fukawachan/PoseDollLab_Design/Hardware/PoseDoll44/docs/SHOULDER_REVH.zh-CN.md

# Rev H · 肩带与双臂机械集成

> 2026-09-20 分类修订：本版 8 个相交姿态均属于左右独立手臂的避让限制，查看页已改为橙色。42 个原样本未发现已建局部机构的结构冲突。下文历史设计进度及“不具备制造条件”的边界保持；新增肩部持姿机构请查看 Rev I。

本轮按“稳定节段包壳、活动区裸露”继续设计。Manny / Quinn 各有独立的肩带与双臂 CAD 总装，沿用 Rev G 的 1:2 候选比例，约 90.8 cm；没有改变关节中心或 44 轴定义。

先打开 [肩带与双臂机械查看页](../generated/revH/RevH_Shoulder_Review.html)。这里显示实际 CAD 的三角化结果，可以选择姿态、隐藏臂壳、显示占位件、旋转及点选零件。相交实体标红，失败样本保留。

## 这一轮增加了什么

每侧加入肩带前伸／后收、抬高／下压两轴，以及肩部屈伸、外展／内收、上臂扭转三轴，连接已有肘臂架。两侧合计 12 轴参与局部总装检查。头、躯干、手腕、前臂独立旋转、手、腿脚以及整机支架没有因此完成。

肩带根部两个竖轴的距离只有约 14.3 mm（Manny）、9.3 mm（Quinn）。新结构采用：

- 共用上轴承桥，保持两条原有竖直轴线。
- 两侧抬肩轴的轴承分别沿原轴线向前、向后移开，避免根部组件挤在一起；轴线本身没有平移。
- 前后转动的持姿摩擦盘上下分层，内侧切平，让相邻长轴通过。
- 肩部三轴共心，屈伸框架采用侧面开口的 U 形结构，让上臂侧举时能穿过开口。
- 上臂、前臂保留分体硬壳；肩带、肩关节和肘部裸露。

左右臂壳沿用各角色 Rev G 的左侧轮廓并镜像到右侧，是身体截面近似，不是左右 UE 皮肤表面的精确复制。肩、肘轴线仍分别取各侧原始配置。

## 已完成与尚未完成必须区分

本轮完成的是轴线、轴承位置、刚性承力框架与部分轴系的空间集成，不是已经能保持姿势、读出所有角度的完整肩部产品。

| 项目 | 当前状态 |
|---|---|
| 肩带 4 轴 | 有轴、轴套、框架及摩擦面候选；预紧受力闭环、轴端固定和调节方式未完成 |
| 肩部屈伸／外展 4 轴 | 共心支承与运动框架已集成；持姿组件尚未装入 |
| 上臂扭转 2 轴 | 轴套、轴及摩擦面候选已布置；固定、预紧与传感器未完成 |
| 肘部 2 轴 | 继承 Rev G 的局部结构；齿轮测角和预紧细节仍是候选 |
| 肩带测角 | 有 4 路磁铁、芯片和板形占位；板上器件、接插件、支架、走线和磁场验证待完成 |
| 肩部测角 | 6 路封装尚未布置，不能据空间检查认定已能读数 |
| 壳体和打印 | 已有臂壳；扣合、安装与接触边缘还需细化，没有制造放行 |

两块肩带前后转动的电路板外形向各自外侧偏置 4 mm，芯片仍对准转轴。这需要新的板上布局核对，不能直接当作旧 Rev B 电路板已经兼容。肩带磁铁与芯片之间的名义间隙只是几何候选。

## 如何看待姿态检查

原始对称抱臂会让两条前臂互相穿入；单纯同时给肩带和肩关节相同角度，也可能使手臂向中间相撞。这些样本仍保留为失败记录，没有通过缩小关节范围来隐藏它们。

新增的错开抱臂候选，让一条手臂位于另一条之前／之上，在两款当前局部 CAD 中都没有检测到超阈值穿插。它还没有包括头、手或完整躯干表面，因此只是可继续研究的姿势，不能视为完整人偶已经满足抱臂验收。

肩膀下压时让肩关节适当补偿，可使手臂保持竖直；肩带前伸加耸肩时，肩关节也可调节到双臂平行前伸。这些是新的明确姿态，不会替换原始失败数据，也不会自动修改用户的实际传感器输入。

[检查报告](../verification/REVH_REPORT.zh-CN.md)给出全部统计、失败样本、轴线核对、分件尺寸和单位末端载荷计算。

## 接下来需要解决的工程关口

1. 补齐肩部屈伸／外展持姿组件，并闭合各关节的金属预紧受力路径；不能靠加紧打印框架来冒充设计完成。
2. 完成轴端限位、正向传力、可拆固定及轴套的轴向保持，核对夹紧后是否仍有正确的转动间隙。
3. 完成 6 路肩部测角和 4 路肩带板的真实电子封装，检查组合运动中的引线长度与弯曲空间。
4. 加入躯干、颈头、手腕与手后重做组合姿态、质量、持姿力矩、操作力和全身碰撞检查。
5. 裸露区保留清楚的抓握和检修通道；壳体不再跨关节封闭。

目前不需要打印、测量或采购。STEP 文件是候选 CAD，金属件并未全部对应到已选定的采购件。UE 插件与 Python 模拟器保持原状；此前颈部位置误差和 Quinn 的独立 UE 适配仍待解决。
