fukawachan/PoseDollLab_Design/Hardware/PoseDoll44/docs/SHOULDER_REVI.zh-CN.md

# Rev I · 肩部持姿机构

本版继续 Manny / Quinn 各自的 1:2、约 90.8 cm 候选尺寸。新增左右肩部屈伸、外展的四套持姿机构，保持关节中心、轴线和臂长。外壳仍只覆盖稳定肢段，肩带与关节活动区裸露。

[打开交互查看页](../generated/revI/RevI_Shoulder_Review.html)，可以按“只看肩部”放大四套机构。页面呈现实际 CAD；橙色表示左右手臂需在摆姿时避让，红色才表示当前登记的局部结构冲突。详见 [检查和预算报告](../verification/REVI_REPORT.zh-CN.md)。

## 这次增加的机械连接

每侧屈伸轴的摩擦组件放在肩部内侧，外展轴组件放在前侧。通过沿既有轴线安排零件位置，保留人物关节中心。外展前轴的光滑轴径由 4 mm 改为 6 mm，后侧 4 mm 支点保留；屈伸光滑轴径继续为 6 mm。

每套组件包含 16 个独立 CAD 零件：

| 功能 | 零件 |
|---|---|
| 承载和传力 | 一体带盘金属轴、D 形连接、轴向固定垫片和内侧 M3 螺钉 |
| 摩擦保持 | 可更换带定位耳摩擦片、金属反力板 |
| 预紧 | 两片反向串联碟簧、钢垫片、带 D 槽止挡盖、外侧 M3 螺钉 |
| 支承与磨损界面 | 径向轴套、止推复合垫片 |
| 固定至打印框架 | 两颗 M3 螺钉、两颗嵌入式六角螺母 |

预紧受力路径为：金属止挡盖 → 碟簧 → 钢垫片 → 止推垫片 → 金属反力板 → 摩擦片 → 一体轴盘 → 轴和轴端螺钉。打印支座传递关节作用力，但不夹在这一轴向预紧回路中。M3 螺钉用于轴端和支座固定；真正转动支承的表面是光滑轴段。

打印输出端已有 D 形孔、轴端紧固件及实际让位孔。孔和轴的候选间隙不是最终加工公差，回差和抗松方案仍要验证。新摩擦片材料还未冻结，不可用假定的摩擦系数直接订料。

## 对原结构的改动

肩带连接路径绕开内侧摩擦盘，再从盘内侧连接肩部轴承。横梁提高至肩轴上方 30 mm，避开大幅抱臂时的同侧上臂壳。这改变的是支架走向，轴的运动中心没有移动。

外展盘的安装耳、螺母槽和加强连接与打印框架一体生成。外展内环开设 3.3 mm 直通工具孔和后支轴孔，供装配阶段从后方接近内侧 M3 螺钉。屈伸轴先在内环未装时固定。工具通道的名义 CAD 包络已检查，实物工具、公差、后支轴固定方式及维修手感仍待验证。

## 以后组装的先后关系

以下用于检查设计的可装配性，尚不是给用户执行的装配说明：

1. 先安装肩带轴承与屈伸外环，此时不装内部外展环。插入屈伸带盘轴，从关节中心装内侧垫片及螺钉。
2. 放入外展内环与前侧带盘轴；暂不装后侧 4 mm 支轴，也不装中心的扭转轴套和轴。从后侧穿过 3.3 mm 工具通道，装外展内侧螺钉。随后装回后支轴、扭转轴套与扭转轴。
3. 将摩擦片定位耳放入金属反力板，再用两颗 M3 和可从内侧接近的螺母固定反力板。
4. 按指定顺序放入止推垫片、钢垫片、两片反向碟簧和止挡盖，装外侧轴端螺钉。
5. 在单关节测试中确认预紧、轴向游隙和正反向回差，再制定正式垫片调整与防松要求。

预紧不是要求用户凭手感随便把螺丝拧紧；当前候选用金属止挡尺寸限定碟簧高度。零件误差与磨损补偿需要后续明确垫片档位及测量办法，日常摆姿时不应反复松紧螺丝。

## 制造与后续工作

新增的带盘轴、反力板、止挡盖等是定制金属加工候选，已输出独立 STEP，不能当作 PLA 零件打印。螺钉、螺母、碟簧与止推件是采购候选；加工图、公差、表面处理及采购清单仍待冻结。我会继续完成这些设计，不要求用户自己选型。

本版尚不能作为可制造全身。接下来需要细化新 D 形接口的夹紧与回差、摩擦材料与预紧调整，补齐六路肩部测角和线束，并逐步接上其余身体模块。四路肩带、上臂扭转及旧肘关节仍有历史未完成项。整机质量和全身干涉也要随新零件加入重新核算。

现在不用打印或购买零件。A1 mini、0.4 mm 喷嘴、PLA 继续作为刚性打印件的试制基线。

## 工程入口

- [CadQuery 总装源文件](../cad/revI/shoulder_integration.py) · [独立摩擦组件](../cad/revI/shoulder_clutch.py)
- [CQ-editor 入口](../cad/revI/open_in_cq_editor.py) · [重建脚本](../tools/Build-RevI.ps1)
- [Manny STEP 总装](../generated/revI/manny/Manny_shoulder_assembly.step) · [Quinn STEP 总装](../generated/revI/quinn/Quinn_shoulder_assembly.step)
- [Rev H 历史查看页](../generated/revH/RevH_Shoulder_Review.html)：原始相交数据保留，已同步采用新的避让分类。

UE 插件、Python 模拟器和原始下载方案未因本轮硬件设计修改。
