fukawachan/PoseDollLab_Design/Hardware/PoseDoll44/docs/SHOULDER_REVJ.zh-CN.md

# Rev J · 肩部夹紧与外展测角

本轮把四处 D 形传力接口细化为可拆卸金属夹头，并把左右肩外展的两路测角装进当前总装。Manny / Quinn 各自的关节中心、1:2 候选比例、44 轴顺序和运动范围均保持。

这是可审查的 CAD 安装方案，尚未制造放行。现在不用打印、测量或采购。

## 新增结构

每款增加四套相同的 D6 夹头，用于左右肩屈伸和外展。夹头为定制金属件，暂按铝建模；它不是 PLA 打印件，也不要求使用者自己加工。

- 6 mm D 轴进入 6.06 mm、平面距中心 2.53 mm 的开口金属孔。
- 横向 M2×10 螺钉收紧开缝；独立 M3 轴端固定件保留。
- 两个 M2×4 法兰螺钉把夹头接到打印关节框架，螺母嵌在可接近的六角槽内。
- 两个法兰孔在模块横截面中位于 (−5.9, −5.9) 和 (+5.9, −5.9) mm，避开原来的扭转摩擦面。
- 打印支撑使用半环连接肋，绕开夹头和收紧耳；外展内框增加两条 2.2 mm 工具通道。

D 形负责几何传力，夹紧负责消除轴孔松动，轴端件负责保持装配位置。夹紧后的真实回差尚未得到验证。法兰孔间隙、摩擦预紧、打印件蠕变和上臂扭转轴本身的间隙也会影响整机，不能仅凭缩小一个孔宣称精度提高到某个数值。

## 两路测角安装

沿肩外展轴的后端布置磁铁，电路板固定在外侧框架，磁铁跟随内侧外展框架转动。两款共用传感器组件尺寸，各自支架仍接在原关节中心。

| 项目 | 当前候选 |
|---|---|
| 电子板 | 现有 sensor_revB 的真实 STEP，18 × 20 mm |
| 板模型 | 包含板体、AS5048A、四个被动器件、背面插座，共 7 个实体 |
| 后端轴 | 定制非磁性 4 mm 铝轴，两段 D 形；径向 M2 固定到内框 |
| 磁铁 | 6 × 2.5 mm，径向充磁圆磁铁 |
| 名义间隙 | 磁铁表面至芯片封装表面 2.8 mm |
| 磁铁固定 | D 形杯、轴向固定螺钉、粘接防转床、可拆保护桥 |
| 电路板安装 | 6 mm 尼龙内螺纹支柱、绝缘垫片、尼龙 M2 螺钉 |
| 接线 | 背面插座为真实模型；配对插头和弯线空间仍是待核实占位 |

独立测角 STEP 是零件组；PCB 支撑桥与肩部外框是一体结构，包含在两款人物总装的 flex_ring 中，没有重复导出到独立零件组。

磁铁周围优先使用非磁性轴和紧固件。圆形磁铁必须和杯体可靠粘接以防相对转动；保护桥负责轴向防脱，不替代防转粘接。胶种、装配方式和旋转防滑试验尚未确定。磁杯 D 形连接的装配间隙也尚未做回差验收。

磁铁与芯片中心应同轴，气隙和偏心会影响测量，附近铁磁材料可能干扰磁场。这些原则来自 [ams 磁铁选型指南，第 3、9–13、20–21 页](https://ams-osram.com/documents/20143/80162/AnglePositionOnAxis_AN000271_2-00.pdf/bd13692b-b589-af7f-560c-4d62bf25d9dd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)。2.8 mm 是本设计的几何候选，并非厂家保证此总装精度的数值。

实际 STEP 板厚为 1.51 mm，制板接口名义为 1.6 mm；当前模型按真实 STEP 定位。生产前需要按板厚和器件高度重新完成公差链，不应把这 0.09 mm 差异当作已经实测的尺寸。

数字检查会计算相对转角、同轴偏差和封装表面气隙。左右安装方向不同，几何角度符号分别为 −1 / +1；这不是 AS5048A 原始读数的最终方向标定。传感器读数方向、零位和磁场诊断仍需后续验证。

## 装配顺序

以下是 CAD 工具通道所采用的顺序，还不是新手最终装配手册。检查使用 2 mm 的 M2 工具杆和 3 mm 的 M3 工具杆包络，没有验证手掌空间、拧紧力矩或完整插入轨迹。

1. 将夹头法兰固定在各自打印框架内。放入六角螺母，再装两颗 M2×4；内框的两条工具孔用于外展夹头。此时内部轴套、扭转轴和后端测角件尚未装入。
2. 将屈伸轴装入外侧框架，按顺序收紧其 D 夹头并装内端垫片与 M3。此时外展内框、扭转轴和手臂尚未装入。
3. 加入外展内框和前端外展轴，收紧外展 D 夹头，从后方中心通道装前端轴的内侧 M3。后端测角轴与扭转轴此时必须留空。
4. 加入后端测角轴，通过径向 M2 将 D 轴固定在内框。再装扭转轴系及手臂。
5. 套入磁杯并拧紧杯内轴向 M2；随后完成磁铁防转粘接与保护桥。电路板此时尚未装上，以便拧磁铁盖。
6. 安装绝缘支柱、垫片及真实 PCB，再安装线束。线束的插头、走向、应力释放和活动余量仍要另行完成设计。

金属轴、夹头孔和尼龙紧固件都尚未冻结采购规格。标准 M2 内六角头的名义 3.8 mm 直径、2 mm 高度可参照 [MISUMI 尺寸资料](https://uk.misumi-ec.com/files/images/products/docs/hexsocketheadcapscrews.pdf)。尼龙螺钉模型采用直径 3.5 mm、高 1.4 mm 的头部包络，这是待匹配采购件的尺寸约束，不代表已确认某个商品。

## 剩余四路肩部测角

本轮另外使用同一块真实 PCB，试排了屈伸轴向内侧延长、扭转轴向顶部延长的位置。完整碰撞结果在 [测角与试排记录](../verification/revJ_readout_check.json) 中。

这些试排没有被计入已集成轴数，也没有被画成已通过的占位。若 PCB 与同侧框架或轴端相交，仍是结构问题。下一轮应考虑独立的小板、调整轴端组件或传动取角；不能把当前两路外展的成功直接复制成六路都完成。

## 边界和下一步

- 当前肩带、肩部、双肘共 12 个轴进入局部运动总装。其余 32 轴尚未在此总装集成。
- 本轮实际安装候选仅覆盖两路肩外展测角；四路肩带仍是占位，肘部传动尚待完成。
- 新夹头、螺母支座、工具孔附近的强度与变形尚未验证。打印薄壁与长期夹紧后的压溃、金属开缝弹性、螺纹啮合、轴套固定和防松都需要继续设计或实测。
- 碟簧和摩擦片保持 Rev I 候选；材料、摩擦系数、预紧公差、耐久与手感未验证。
- 两臂互碰保留为摆姿限制；邻接肢段、关节内部及归属不明的碰撞仍是结构问题。
- 维持 A1 mini、0.4 mm 喷嘴、PLA 的刚性分件规划。包围盒能放下不等于已生成可打印包；本轮未生成制造放行的 STL 或切片。
- 头、颈、躯干表面、手、全身支架与线束尚未参加完整碰撞验收；既有颈部位置误差和 Quinn 独立 UE 适配仍待处理。

下一步优先补齐屈伸／扭转测角、轴向固定和线束，随后推进躯干与下肢。详细数字结论见 [Rev J 检查报告](../verification/REVJ_REPORT.zh-CN.md)。
