fukawachan/PoseDollLab_Design/Hardware/PoseDoll44/docs/SHOULDER_REVK.zh-CN.md

# Rev K · 紧凑扭转测角安装

状态：数字设计候选，未制造放行、未实测。现在不用采购、打印或补测工具。

## 支撑方式：按用户最新要求

人偶本体不依赖固定的桌夹、立柱或底座来限定动作。站、坐、仰卧、俯卧与侧卧列为后续全身设计场景；摆好后可由独立外部物体托住。**外部支撑物本轮不设计**。内部关节轴承座、测角板托座和胸部承力框仍属于人偶骨架，需要继续检查自身干涉。

当前局部 CAD 固定一个数学参考坐标，只用于算相对姿态，不代表要求人偶锁在实体支架上。原 44 轴中骨盆三轴的名字保留兼容性，但取消固定支架后，其实体参考方案要另行设计，不能把未知输入当作测得零值。当前 UE 的 Placement 仍可控制场景整体放置；本轮不改软件。

详见 [支撑方式约定](../mechanical_manifest/support_policy.json)。本轮肩臂检查不能代表完整站、坐、躺已经验证。

## 这轮完成的结构

Manny、Quinn 各加入左右两套上臂扭转测角组件。加上 Rev J 的左右外展，每款现在有四处肩部测角安装候选。肩屈伸两路仍未装入。保留 44 轴顺序、两款各自的关节中心与约 90.8 cm 的 1:2 候选尺度。稳定肢段用臂壳，肩部活动区继续裸露。

- 用独立的 **12 × 10 × 1.0 mm 小板**取代扭转位置原先放不下的 18 × 20 mm 板。AS5048A、供电和六线 SPI 网表与 Rev B 相同。
- 扭转金属轴与磁铁杯合成一个定制铝件，缩短顶部堆叠。磁铁为 6 × 2.5 mm 径向/直径方向充磁候选；不能用轴向充磁件代替。
- 磁铁加可拆机械保护盖，两颗黄铜 M2×3 顶丝固定；胶层只承担待验证的防转配合，轴向保持不只依赖胶。
- 轴下端增加 D4 形接口和径向 M2×6 固定螺钉，使手臂与磁铁轴建立机械传角关系。该接口尚未进行夹紧回差和耐久验证。
- 测角板由两个**后装可拆托座**和两个绝缘夹盖固定。托座必须独立，不能与肩框合并打印，否则带保护盖的磁铁轴装不进去。

[查看实际总装](../generated/revK/RevK_Shoulder_Review.html) · [检查报告](../verification/REVK_REPORT.zh-CN.md) · [紧凑扭转组件 STEP](../generated/revK/components/compact_twist_encoder_assembly.step)

## 局部基准尺寸

局部 +Z 沿扭转轴指向肩顶部；原肩关节中心为 Z=0。局部 X 在左肩对应世界 +X，在右肩对应世界 -X；小板托座沿前后方向布置，避开内侧螺钉。以下是名义设计值，不是测得精度。

| 特征 | 尺寸 / mm |
|---|---:|
| 金属轴下端 | Z=-24 |
| 下端 D4 平面距轴心 | 1.50 |
| 打印 D 孔候选 | D4.10，平面距轴心 1.55 |
| 修整后固定轴座顶面 | Z=5.50 |
| 一体轴杯底面 | Z=5.70 |
| 磁铁底面 / 顶面 | Z=6.50 / 9.00 |
| 保护盖顶面 | Z=9.60 |
| 传感器封装表面 | Z=10.50 |
| 磁铁至封装名义气隙 | 1.50 |
| 小板背面基准 | Z=12.495 |
| 固定立柱顶面 | Z=10.695 |
| 后装托座板面 | Z=11.495 |
| 板夹盖名义高度 | 0.80 |
| 板夹盖 M2×6 进入固定柱的长度 | 3.40 |

STEP 的 FR4 实体为 0.91 mm，KiCad 的制造板厚设置为 1.0 mm；铜层、模型偏置与制造板厚不能混用。托座按 1.0 mm 板厚设定。板厚公差、装配偏心和轴向窜动还会改变真实气隙。

轴杯到固定座的 0.20 mm 名义间隙、磁铁径向 0.10 mm 胶层空间、板边定位间隙都是待实物校核的候选，不应据此认为打印与装配已经合格。

## 必须遵守的装配顺序

这是一份供后续放行时细化的顺序，现在不要求动手。

1. 先完成原有屈伸与外展内部紧固件，再装外展后端测角轴。保持 Rev J 的内部螺钉先装顺序。
2. 在独立扭转轴上装磁铁、保护盖及两颗径向顶丝。此时轴尚未插入肩框，顶丝有直线工具通道。
3. 将完整的轴、磁铁、保护盖从上方插入扭转轴套。此时小板托座、板子、夹盖和轴下端径向螺钉均未安装。
4. 对齐手臂 D 形孔，插入轴下端，再装下端径向 M2×6 螺钉。
5. 放入左右两个可拆托座，再放小板、夹盖与 M2×6 螺钉。螺钉为几何候选，不能给尚未测试的打印螺纹指定装配扭矩。
6. 在外肩框装合前插入短 FPC 并关闭锁扣，再完成肩部总装。FPC 型号、转接板及全行程活动线束尚未完成设计。

工具检查使用明确的分步已装零件清单。它证明的是已建几何中的直杆、板子、轴及连接器服务包络没有超阈值阻挡；没有证明手指能伸入、实际扭矩合适、零件在公差极限下仍能装入，也没有证明无需拆解即可维护。

## 小板与连接器

原生 KiCad 工程：[sensor_revC_mini](../electronics/sensor_revC_mini/PoseDoll_AS5048A_revC_mini.kicad_pro)。

六线保持为：1 GND、2 +3V3、3 SCK、4 MOSI、5 MISO、6 CS_N。仅使用 3.3 V 供电。使用新连接器后不能直接插旧 JST 线束；排线两端编号、接触面和转接板需要单独设计。

连接器候选为 Hirose FH19C-6S-0.5SH(10)，0.5 mm 间距，适配厚度 **0.20 ± 0.03 mm** 的 FPC，六线排线宽度 3.5 mm。不能默认用常见 0.3 mm 排线。封装焊盘根据 [Hirose 原厂图 EDC3-155621-07](https://www.hirose.com/en/product/document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) 建立；已保存 [原始尺寸 PDF](../references/revK/FH19C-6S-0.5SH_drawing.pdf)。

CAD 中 U1、四个无源器件与板体来自实际 KiCad STEP；连接器使用 **5.15 × 3.15 × 1.0 mm 保守尺寸包络**，不是厂家精细 STEP。4 mm 短排线是服务占位，不能代替完整活动线束。锁扣打开的服务包络取 1.9 mm 高。

电气检查采用双层板、0.15 mm 走线／间距、0.25 mm 铜至板边、0.6/0.3 mm 过孔。连接器焊膏孔当前采用四边内缩 0.025 mm 的候选，投板前仍需对照厂家模板建议复核。没有输出量产下单包，也没有进行信号完整性或 EMC 验证。详情见 [提取接口与规则](../electronics/sensor_revC_mini/mechanical_interface.json)。

## 本轮保留的问题

肩屈伸板在 Quinn 的后收＋下压样本中仍会碰到胸部内部承力框，因此没有计入已完成安装。旧扭转直排试放也曾碰到内部螺钉；它已由本轮紧凑轴杯方案替代，失败记录保留用于追踪，不能当成当前总装结论。

四处肩带、两处肘测角仍有占位或转接未完成；肩带与扭转持姿预紧、完整轴向保持、全行程排线、供电转接、躯干、颈头、手与下肢尚未完成。完整 44 轴装配仍只有 12 轴参与当前局部总装。

真实磁场强度、偏心、附近铁磁件的影响、回差、蠕变、耐久与手感都待后续分阶段实测。本轮气隙和转角检查仅是几何关系，不代表 AS5048A 已有真实读数。
