fukawachan/PoseDollLab_Design/Hardware/PoseDoll44/docs/SHOULDER_REVL.zh-CN.md

# Rev L · 肩部屈伸测角安装

Manny、Quinn 各补入左右屈伸测角组件。加上已有的外展和扭转，**每款三轴肩关节的六处测角安装均已建立 CAD 候选**。这不包含肩带四轴，也不代表全身 44 轴完成。

[交互查看页](../generated/revL/RevL_Shoulder_Review.html) · [检查报告](../verification/REVL_REPORT.zh-CN.md) · [拆装层次图](../generated/revL/components/flex_exploded.png)

## 为什么这样改

Rev K 的小板直排试放在 Quinn 肩带后收、下压时碰到胸部内部承力框。这轮沿用 12 × 10 mm 小板，改用较矮的轴端螺钉、套在金属止挡帽外的磁铁杯，并把板子绕测量轴旋转 90°。小板背面从旧试排的 63.995 mm 移到 61.771 mm，缩短 2.224 mm。

不移动人物关节中心，不改臂长，不缩小原关节限位。仍采用约 90.8 cm 的 1:2 候选尺寸；稳定肢段包壳，肩部活动区裸露。**人偶本体不依赖固定外部支架，外部支撑物暂不设计**。站、坐、仰卧、俯卧、侧卧是后续全身场景，当前肩臂检查不代表全身场景已完成。

## 转角如何传递

机械路径为：屈伸输出框 → 原金属 D 形驱动与屈伸轴 → D 形止挡帽 → 带配合平面的磁铁杯 → 磁铁。测角板经两根独立固定柱连接屈伸反力板，与肩带输出框一起运动。

磁铁杯和止挡帽靠平面配合传角，两颗侧面顶丝负责轴向保持。磁铁暂按径向留 0.10 mm 胶层防转，并用可拆保护盖挡住外圈；粘接剂、真实回差和耐久尚待选型与实测。没有将磁铁只粘在螺钉头上，也没有让测角板承受手臂重量。

两根固定柱装在反力板上，固定孔与原离合安装螺钉分开。离合的弹簧、止挡高度与金属闭合受力路径保持；止挡帽材料改为铝，轴端螺钉改为钛合金候选，因此材料强度、局部接触压力、锁紧和持姿仍须验证。

## 主要名义尺寸

局部 +Z 从肩关节中心沿屈伸轴指向胸口，左侧对应世界 -Y，右侧对应世界 +Y。小板坐标相对该局部坐标绕 Z 转了 90°。

| 特征 | 名义尺寸 / mm |
|---|---:|
| 原离合基面 | Z=43.000 |
| 止挡帽底面 / 顶面 | Z=50.376 / 53.376 |
| M3 矮头螺钉头径 / 高度 | 5.70 / 1.65 |
| 磁铁杯底面 / 顶面 | Z=50.576 / 58.276 |
| 磁铁杯外径 | 17.40 |
| 杯底与螺钉顶面之间的轴向空隙 | 0.15 |
| 磁铁下面杯底厚度 | 0.60 |
| 磁铁底面 / 顶面 | Z=55.776 / 58.276 |
| 保护盖顶面 / 外径 | Z=58.876 / 19.00 |
| 传感器封装表面 | Z=59.776 |
| 磁铁到封装名义气隙 | 1.50 |
| 小板背面基准 | Z=61.771 |
| 两根固定柱中心 | X=0，Y=±11.90 |
| 固定柱本体高度 / 六角对边 | 12.771 / 3.50 |
| 固定柱底部 M2 进入反力板 | 2.50 |
| 板夹 M2×6 进入固定柱 | 3.20 |

反力板新增的两孔是贯通 M2 底孔，螺柱端部停在 Z=44.50，距摩擦片顶面保留 0.50 mm。不能让螺柱伸到摩擦片上。磁铁杯保护盖顶丝的底孔留了退刀深度，止挡帽侧面螺纹孔通至已有中心孔。CAD 螺纹按底孔与外螺纹包络表达，未画螺旋牙形。

打印保护盖的局部环壁约 0.75 mm，部分配合仅有 0.05 mm 径向余量；这些是**待调整的配合候选**，还不能当作 PLA 打印后可直接装好的尺寸。金属件孔位、公差与表面质量仍需后续加工图和实物校核。当前不要求打印、采购或测量。

## 分步装配顺序

以下是已建零件中的名义顺序，还不是制造放行说明书。

1. 完成原屈伸离合和内部 D 形驱动的紧固件。使用新铝止挡帽及 M3×8 矮头螺钉，先拧好轴端螺钉，再装磁铁杯。原弹簧高度由金属止挡决定。
2. 把空磁铁杯沿轴线套到止挡帽的配合平面上，装两颗 M2×4 侧面顶丝。此时固定柱、小板和板夹都未装。
3. 安放磁铁、保护盖与两颗 M2×3 顶丝。磁铁充磁必须沿直径方向；真实磁场与防转粘接还未验证。
4. 拧入两根六角固定柱。扳手从各固定柱朝关节外侧的方向接近，握住固定柱底部六角，避免穿过离合垫片。
5. 放入两个独立板托座，再沿轴向放小板、板夹和 M2×6 螺钉。固定柱及板夹均能拆下。
6. 在工作台上的局部组件中插入 FPC、操作连接器锁扣。先装好屈伸反力板与肩带输出框的 M3 安装螺钉，再与肩带上游机构合装；Quinn 若完全装合后再从该方向伸螺丝刀，会受到上游框架阻挡。

工具检查记录了每一步明确的已装零件。它涵盖直杆、扳手包络、磁铁杯几个插入位置以及各个板上器件的保守轴向插入包络；没有验证手指抓握、实际装配扭矩、全公差装配或无需拆解的维修。肩带上游的最终轴向保持仍待设计，不能将上述顺序理解为全身装配已经打通。

## 电子与校准

继续使用 [Rev C mini KiCad 工程](../electronics/sensor_revC_mini/PoseDoll_AS5048A_revC_mini.kicad_pro)，原理图、PCB 与六线 3.3 V SPI 接口没有改动。本轮不重新声称完成电子实测。

小板的板体、AS5048A 和四个无源件来自已有 KiCad STEP；FPC 连接器是厂家尺寸包络，短排线仍是占位。板旋转 90° 后，在我们的 CAD 参考轴定义中增加了 -90° 的名义零位偏置，检查脚本已显式扣除。这个数值不是 AS5048A 实际上电原始读数；实际磁铁方向、芯片零位与左右正负仍须校准。

轴端螺钉候选为 [Accu SSB-M3-8-TI5](https://accu-components.com/us/socket-button-screws/422924-SSB-M3-8-TI5)，厂家列出的头径 5.7 mm、头高 1.65 mm、2 mm 内六角用于当前包络；[来源记录](../references/revL/button_screw_source.json)保留具体字段。未确认供货与实际承载，不可随意用普通高头 M3 替换。铝帽、钛螺钉及黄铜顶丝减少磁铁附近的铁磁材料，但附近仍有钢轴、反力板和弹簧；当前几何气隙不能证明磁场质量。

## 继续设计的部分

肩带四轴测角、肘部传角转接、肩带与扭转持姿预紧、完整轴向保持、活动线束和转接、躯干、下肢、颈头及手尚未完成。取消固定外部支架后的骨盆三轴实体参考继续保留待定，不改原通道名字，不把未知测量当作零值。UE 插件和 Python 模拟器没有因本轮修改。
