fukawachan/PoseDollLab_Design/Hardware/PoseDoll44/docs/SIZE_REVIEW_BEFORE_EXTERNAL.zh-CN.md

# 外置改版前的尺寸评估

修正后的结论：下一版采用用户已同意的“局部采集 + 外置电源/USB 接口盒”。**现有文件不能直接等比例缩放，但尚无证据证明重新设计的小型版必然昂贵或不划算。** 现有 1:2 图纸暂作比较基线，不能把 91 cm 身高、6 mm 磁铁或当前关节外径当作不可突破的设计下限。是否缩小，应由重新布置后的关节尺寸、载荷、动作空间、装配步骤和实际报价决定。

本轮只完成尺寸、接口及装配约束评估；没有生成缩小版 CAD，也没有开始制造外置版电子设备。既有 Rev N1 模型、PCB、固件和查看器均未被这次评估修改。

## 当前实际基线

- Manny 的 UE 参考表面缩放高度为 907.93 mm，Quinn 为 907.70 mm，均约 91 cm。这里是角色参考高度，不是实物量测。
- Rev N1 含原背部设备和线束的估重分别约 3.20 / 3.16 kg。它们确实比普通美术人偶更大、更重；减重和降低操作阻力有价值。
- 每款已有 39 块 12 × 10 mm 小测角板、2 块 18 × 20 mm 肩外展测角板、M2/M3 紧固件、4/6 mm 工作轴颈和指定碟簧。接头为 1 mm 间距 SH6。小板尺寸已经从当前两款制造清单的实体包络核对。
- 现有方案仍需要加工方交付精密轴系和预装关节、贴片方交付 PCBA，以及预压接线束；它本来就不是完全靠打印和拧几颗普通螺丝完成的产品。

## 磁铁与关节尺寸补充核对（2026-09-23）

先前把“不允许直接缩放”进一步写成“小型化收益不足”，证据不充分，已在本文件和配套 JSON 中修正。此修正不表示已经完成更小的关节或批准某个缩小比例。

**6 mm 的来源是当前传感器方案和早期配套磁铁基线，不是市场买不到更小磁铁。** 本项目早期物料表采用 AS5048A 与 AS5000-MD6H-2（Ø6 × 2.5 mm）组合；没有做过足以证明该尺寸成本最优的报价比较。小型化也不必首先改磁铁，需先识别真正占空间的结构。

| 产品目录核对 | 可支持的结论 | 不可推断的结论 |
|---|---|---|
| [Magnet Baron 3 × 2 mm 直径方向充磁磁铁](https://themagnetbaron.com/products/100pcs-3mm-x-2mm-1-8-x-1-16-disc-magnets-diametrically-magnetized)，100 颗标价 USD 16.99 | 确有更小规格及并不高的目录单价（约 USD 0.17/颗，未含运税） | 页面库存信息混合显示，未确认可立即发货；没有磁场均匀性/传感器匹配鉴定，不能据此采购替换 |
| [K&J D24DIA](https://www.kjmagnetics.com/d24dia-neodymium-diametric-cylinder-magnet)，约 Ø3.175 × 6.35 mm，1–49 颗档 USD 0.35/颗 | 更小直径的直径方向充磁磁铁也有目录供应 | 此件更长，并非能直接减少本项目轴向高度的候选 |
| [Infineon AS5048A 产品资料](https://www.infineon.com/part/AS5048A)给出 30–70 mT 磁场范围 | 磁铁选择须与传感器磁场要求配合 | 目录吸力、磁铁直径或单点表面场强不能替代芯片感应区域的场分布与角度误差检查 |

价格仅为查阅时的页面记录，不是到手报价，也不是制造选型。更小的磁铁需要复核磁化方向、场分布、间距、偏心及角度误差；不能保证原 AS5048A 与任意小磁铁都兼容。必要时可比较另一种传感器架构，但当前没有更换器件或固件。

**关节有重新紧凑设计的空间，当前尺寸不是已证明的最小值。** 在当前 Manny 制造清单中，肘关节的磁铁 Ø6 mm，磁铁杯外径 16.4 mm、保持盖外径 19.2 mm，摩擦圆环外径约 26 mm（不含止转耳）。较大的杯还包围止挡帽和保持结构，所以把磁铁改成 Ø3 mm，并不会自动让这套关节缩小一半。腰部下摩擦环外径为 36 mm，胸部为 32 mm；这是现有摩擦和载荷方案的结果，不是磁铁强制的外径。

现有机构也已经有 4 mm 与 6 mm 工作轴颈的区别。紧凑化可以比较：减少输出连接耳和独立隔柱、缩短轴向堆叠、合并非活动支座、调整板和插头方向、按部位采用不同规格。以上均是设计研究方向，尚无新 CAD 或装配验证。

若保持同样的所需扭矩，缩小摩擦有效半径会增加所需预紧力（简化关系 T≈μ·F·r，多摩擦面另计）。但是人偶同时缩小、减重和移出设备后，所需保持力矩也会下降；应联合重算，不能拿原约 3.2 kg 设计的载荷要求当作小型版永远不变的条件。

加工成本取决于零件复杂度、装夹次数、公差、标准件/定制件比例、批量和预装工序。更小并不必然更贵；减少零件和装夹也可能抵消尺寸变小带来的难度。若必须采用更紧公差或微小紧固件，则可能增加加工和用户维修难度。目前没有报价，不能给出净成本结论。

## 为什么不能把所有文件一起缩放

| 约束 | 当前设计 | 等比例缩小造成的变化 |
|---|---|---|
| 磁铁与安装杯 | Ø6 mm 磁铁，示例杯孔 Ø6.2 mm | 缩至 90% 后孔为 Ø5.58 mm，现有磁铁装不下 |
| 小板与板托 | 12 mm 板宽，示例板托内侧宽 12.2 mm | 缩至 90% 后间距 10.98 mm，现有板装不下 |
| 插头、螺丝、碟簧 | 现成实物规格 | 改小安装位不会改小买来的实物；改型需重做配合和载荷核对 |
| 测角和转动配合 | 1.5 mm 名义芯片面间距、0.05 mm 等候选配合量 | 要按传感器磁场、加工和装配误差重新确定，不能与骨长一起缩放 |
| 走线和工具空间 | 活动传感器线候选弯曲半径 12 mm，电源 15 mm；螺丝刀/插拔通道另留 | 原线材和工具不会等比例变小，需要重新布置和检查 |

上述孔/板托例子取自现有通用关节源码；它们只证明直接缩放不兼容现有零件，**不能据此断言重新设计的小型关节做不出来**。线束弯曲半径仍是本项目候选，尚未得到实物反复弯曲寿命验证。[JST SH 官方图纸](https://www.jst-mfg.com/product/pdf/eng/eSH.pdf)给出了固定的插头尺寸和间距。

如果只缩短骨骼、保留原关节模块，关节和插头会相对更粗，肩、髋、肘、膝附近的可用空间减少，可能更早接触。具体哪些姿态受限需要对新模型重新检查；本轮没有把这种风险冒充为已经仿真出的碰撞结果。所有零件真能理想等比缩放时，纯几何碰撞关系反而不变，现实问题来自固定尺寸的器件、配合和线材。

## 缩小的收益和代价

| 相对当前线性尺寸 | Manny 参考身高 | Quinn 参考身高 |
|---|---:|---:|
| 100.0% | 90.8 cm | 90.8 cm |
| 90.0% | 81.7 cm | 81.7 cm |
| 80.0% | 72.6 cm | 72.6 cm |
| 66.7% | 60.5 cm | 60.5 cm |

这些是算术示例，不是已通过验证的尺寸选项。理想情况下所有材料、壁厚、器件都缩至 80%，质量可按 0.8³ ≈ 51.2% 变化，重力矩按 0.8⁴ ≈ 41.0% 变化，因此不能简单说“更小一定更弱或更难保持姿势”。真实人偶中的板、螺丝、线和配合不能全部照缩，不能按这两个比例预测实际减重和手感。

重新设计小型版有可能更轻、更便于搬动；代价是重做多轴关节、紧固与预紧件选型、测角板托、装配通道、全身动作和线束验证。若采用更细小零件或更紧密布置，预装、插拔、检验与后期维护要求也会上升。这些是需要检查的项目，不能只凭现有元件装不进缩小后的孔位，就判断重新设计的小型版代价大于收益。当前缺少紧凑关节对比、加工报价和小型样机，因此成本变化与可缩小百分比均未确定。设计和验证工作增加，也不等于用户最终采购、装配和维修成本一定增加。

0.2 mm 喷嘴可能改善部分打印细节，但不能解决现成芯片/接头尺寸、金属轴系配合和螺丝刀空间；此处没有必要先购买另一台打印机或喷嘴。

## 外置改版与后续尺寸比较的约束

1. 当前交付图纸仍为各自 UE 参考骨架的 1:2 基线。若研究缩小版，两款应各自统一缩放解剖长度，保留人物比例、测量轴语义和活动范围目标；新关节中心由新比例确定，不能为了塞入旧关节只缩短某几段肢体。
2. 重新紧凑布置本地采集板，取消背部大电子仓及只服务电子仓的突出载架，给背手动作让出空间；保留真正的肩颈/脊柱承重结构。
3. 把电源与 USB 网关放外部；小板、局部支路保护和柔性线仍需留在人偶内。原背部组件约 0.54 kg 不能全部当作确定减重。
4. 将真实插头、拔插和工具通道、线束服务弯纳入新布局，不以难维修的小型接头或削减动作范围换取外观紧凑。
5. 新布局完成后重新计算质量、重心与各关节保持需求，再决定哪些预紧参数能降低。重量减轻并不自动使原摩擦关节更容易掰动。
6. 继续 41 个相对测量轴 + 3 个固定骨盆协议槽；整体位置和全部整体转动由 UE 调整。固定支架和 IMU 不在此改版范围。

外置主要减少突出厚度和机内设备负担，**不会让人偶变矮**。若后续仍需更小身高，应作为保留人物比例的独立小型化设计，不能在切片器里缩放现有 STL。

证据：[两款比例复核](../verification/revM_proportions.json)、[当前 Rev N1 结果](../verification/revN_review_summary.json)、[本次尺寸计算与输入哈希](../verification/size_review_before_external.json)、[外置架构利弊](CHEST_AND_EXTERNAL_REVN.zh-CN.md)。
