fukawachan/PoseDollLab_Design/Hardware/PoseDoll44/verification/H0_REPORT.md

# H0 工程报告 · 整机布局 Rev A / 机械配合 Rev B

结论：继续数字设计，不以用户先完成试片实测为前提。Rev B 按 A1 mini / 0.4 mm / PLA 的工程假设调整通孔并生成未来试片；当前不要求用户打印或测量。整机制造与实物性能尚未验证。

## 已执行

- 44 轴映射，六区域 6/6/9/9/7/7；原虚拟轴顺序一致。
- 13 个编号打印件均为单一有效实体，单件包络不超过 160 mm；3 件 fit 试片留作设计完成后的验证。
- 单轴 0～145° 每 5° 共 30 个名义姿态：本模型参与检查的动/静实体无正体积干涉。不是连续扫角、公差或承载证明。
- KiCad ERC、DRC 与原理图一致性检查通过；详细启用/忽略规则见 JSON 报告，未添加违规豁免来隐藏失败。
- 单轴诊断固件在 ESP-IDF 6.1 编译；协议故障测试、诊断界面构造和现有模拟器测试已运行，见对应日志。
- 现有受版本管理的软件文件没有修改。本轮没有运行实体 UE Capture/Undo/重开测试。

## 布局与负载

中立头顶参考点 Z=681 mm，已超过原约500 mm目标；不是尺寸冻结。质量集中参数预算为 2.904 kg，不是称重。区域/网关 PCB、连接器维护空间和支架是候选包络。

三类关节是尺寸/能力假设：

|类别|圆柱半径×轴向长 mm|主螺栓/轴 mm|能力假设 Nm|模块质量假设 g|
|---|---|---|---|---|
|S|12×12|4|0.12|24|
|M|18×16|6|0.6|48|
|L|26×20|8|3.0|95|

H1 是较宽敞的台架夹具，不能当作已封装的 S/M/L 身体模块。当前 32 mm 传感器板和紧凑多轴支架还需共同缩小/避让。

预算采用 τ=轴方向·Σ(r×mg)；对给定形状另列 Σ(mg·垂轴距离) 的方向无关上界。后者是保守包络，**不是已经出现的实际最坏负载**；保持目标按上界×1.5+0.02 Nm 线束余量。质量集中、线束余量与能力假设都需实物修正。

|轴|12姿态重力最大 Nm|方向无关上界 Nm|设计保持目标 Nm|能力假设 Nm|
|---|---:|---:|---:|---:|
|pelvis.pitch|1.157|6.1891|9.3037|3.0|
|pelvis.roll|0.0421|5.9899|9.0049|3.0|
|waist.pitch|0.9591|3.3161|4.9941|3.0|
|waist.roll|0.0421|2.9739|4.4809|3.0|
|pelvis.yaw|0|2.2632|3.4148|3.0|
|chest.roll|0.0421|1.8939|2.8609|3.0|
|waist.yaw|0|1.8114|2.7371|3.0|
|chest.yaw|0.0|1.8114|2.7371|3.0|

结论：当前大关节能力假设无法覆盖保守预算。需要减重、收拢轴中心、重新布置支架和夹持面，而不能直接拧紧所有关节。强度/蠕变/疲劳未做结论。

## 碰撞与走线

完整布局保留 12 个具名姿态和 64 个固定种子随机姿态的球包络筛查。进一步对 12 个姿态中的关节、传感器板、区域板与接头维护包络做了 OCC 交集：

|姿态|相交包络对数|
|---|---:|
|neutral|23|
|arms_forward|23|
|arms_overhead|29|
|arms_side|23|
|hands_on_hips|24|
|arms_crossed|32|
|forehead|24|
|sitting|23|
|crouch|29|
|head_tilt|23|
|hip_abduction|23|
|palms_turn|23|

这些是实心设计包络的相交，不全等于真实空心支架撞击；它们也**不能被忽略当作已解决**。需要紧凑三轴支架详细设计和连续运动/工具/线束审查。具名姿态是设定角度，不证明手实际碰到额头或髋部。

六区域节点位置已调整。12 姿态中的端点直线距离+60 mm 假设余量上取整后，44 条最长 250 mm。它不是沿关节表面的走线长度，更不是可裁线单；弯曲、应力释放、插拔空间仍待设计。
CAN 候选线性顺序 G0→N1→N5→N6→N3→N2→N4，端点终端，电源单独分路。不是把多个分支星形连成 CAN。

## 电气预算与实现范围

44传感器、6 MCU、7 CAN收发器及缓冲余量，按3.3V负载和85%降压效率估算，5V输入 2.277 A；加30%余量 2.96 A。5V/4A仅为候选规格，未选择适配器或完成保护/热设计。
九传感器区域若用线性稳压，预算耗散 0.765 W，因此完整区域应设计降压电源，不能照抄台架DevKit的供电。
CAN：17帧/周期×100Hz×135bit + 60诊断帧/秒×135bit，500kbit/s下约47.52%；未含实测重发和错误风暴，不是通过60%占用目标的证据。
支架粗估力矩 12.27 Nm（重心150mm + 手20N作用于400mm），桌夹/桌面未选型。

只完成自制传感器板与单轴USB诊断。区域节点/网关PCB、保护/隔离供电、CAN固件、完整cohort USB协议、UE实体设备配置和校准尚未实现。无采购生产Gerber，无烧录、OTP写入或实物通电。

## Rev B 打印配合设计依据

已读取用户提供的《PLA材料比较》对话，并核对官方补偿功能文档及一条社区原始反馈。社区个例不作为精度保证。当前孔径：M2 2.6、M3 3.6、M4 4.8、M6 6.8 mm；多片支架 M3 3.8 mm。M5 5.8 mm 仅保留规则。
CAD 中的装配余量与切片补偿分开记录；未来切片初始 XY 补偿为0、自动圆孔补偿关闭，避免叠加未标定修正。轴套座和磁铁座单独处理，不套用螺丝通孔余量。
孔径误差 -0.4/-0.2/0/+0.1 mm 只是敏感性情景，不是实测分布；参见 print_fit_sensitivity.json 与 [设计依据](../docs/DESIGN_BASIS.zh-CN.md)。这些假设不能证明定位、承载或所有打印方向合格。

## 继续设计与后续实物验证

1. 采用 print_fit_profile_revB.json 中的未标定假设继续设计；不等待用户补工具或试片。
2. 设计端继续完成轴套保持、磁铁定心、五金选型、紧固件和工具净空；在最终实物测试包中明确装配件与检验方法。
3. 完成紧凑三轴详细结构，实测相邻磁铁、负载与手感后扩展一侧肢体。
4. 节点/网关与UE实体链路独立验收后进入全44台架和整机。

软件基线：7c22e075fe0efe295ce2935a8bb2a92cff0b6def。原profile SHA256：a7047b7c1bdefaee37acf547d5a823cc2f89d08f5c3e9cd9710a6f6bf79ef224。
