fukawachan/PoseDollLab_Design/Hardware/PoseDoll44/verification/REVL_REPORT.zh-CN.md

# Rev L · 肩部屈伸测角检查

状态：数字设计候选，未制造放行、未实测。两款各新增左右屈伸安装；加上已有外展、扭转，每款六处肩关节测角安装候选。肩带不包括在这六处中。

## 总装检查

| 角色 | 实体及占位 | 无局部结构冲突 | 同时没有双臂互碰 | 肩关节测角安装 |
|---|---:|---:|---:|---:|
| Manny | 335 | 36/36 | 32/36 | 6 |
| Quinn | 335 | 36/36 | 30/36 | 6 |

原有 72 个离散肩臂姿态通过局部结构检查。阈值为相交体积 0.02 mm³。10 个独立双臂相交样本继续作为橙色摆姿限制；内部及相邻节段冲突仍标红。另有两款合计 12 个“肩带极限位置＋屈伸角度”组合，仅复查涉及本轮新增／修改件的配对，未发现相交；它们不能作为全总装新增姿态通过数。

检查先核对 Rev K 及其 Rev J 继承几何、比例和结果的 SHA256，并断言未改零件保持原 Shape 对象。原有未改件配对复用此前检查结果；每个姿态中涉及本轮变化的配对都重新做 BRep 相交。同一运动节段内的变化配对另行检查，只有明确螺钉／螺纹底孔对被解释为预期配合。

每款增加 46 个实体／占位，并修改 6 个既有实体，共 335 个；板上元器件也分别计数，**不是采购 335 件**。全部逻辑实体有效、单一实体。当前仍为 12/44 轴参与局部总装，人物比例、关节中心和原角度限位不变。

## 新组件与胸部承力框的距离

| 角色 | 最近的原有样本 | 最近零件 | 距离 / mm |
|---|---|---|---:|
| Manny | back_down | l_flex_sensor_board_M2x6_0 | 9.144 |
| Quinn | down | l_flex_sensor_board_cap_0 | 1.805 |

这些是名义 CAD 距离，不包含制造公差、手部挤压、骨架变形或完整躯干表面。小板背面基准从旧直排试放的 63.995 mm 改为 61.771 mm，缩短 2.224 mm。前期小板方向试排见 [研究记录](revL_head_probe.json)，它只检查了板与连接器包络，最终总装结论以本报告为准。

## 装配、测角与电路

- 64 条原离合／外展工具通道、36 条原扭转装配通道、76 条新增屈伸工具与插入检查通过，共 176 条。记录中明确区分工作台子装配与肩带上游尚未装入的阶段。
- 六处测角在两款各 36 姿态下完成 432 条同轴、相对角度及封装表面气隙检查。外展名义气隙为 2.8 mm；扭转和屈伸为 1.5 mm。
- 独立屈伸模块另检查 -50° 至 160° 每 10° 一个角度，共 22 项。新板的 90° 安装方向在 CAD 参考中产生 -90° 零位偏置，检查明确处理了该偏置；不是对真实传感器原始零值的预测。
- 沿用 Rev C mini 的原理图与 PCB。哈希核对确认它们及既有 ERC、DRC、未连接和原理图一致性结果未变，既有检查均为零项；本轮没有进行电子实测。

工具包络通过不等于装配扭矩、公差极限、手指抓握或无需拆解维修已经验证。FPC 只有短直插段，完整活动线束与转接没有完成。[详细装配顺序](../docs/SHOULDER_REVL.zh-CN.md)

## 持姿估算

| 角色 | 最不利轴下游已建质量 / g | 加每腕 100 g 的取样力矩上界 / N·m | μ=0.15、552 N 假设下的余量 |
|---|---:|---:|---:|
| Manny | 184.3 | 0.372 | 2.01 |
| Quinn | 175.3 | 0.349 | 2.14 |

预算只覆盖现有屈伸和外展离合，按打印件实心 PLA、铝帽、钛螺钉与黄铜固定柱的假定密度计算；握力、动态、线束回弹、磨损与蠕变未计入验收。止挡高度保持原值，但铝帽的局部承压、螺纹强度和钛螺钉承载未验证，以上余量不是实测额定负载。完整假设见 [负载记录](revL_load_budget.json)。

## 双臂摆姿限制

| 角色 | 样本 | 独立双臂相交对数 |
|---|---|---:|
| Manny | arms_crossed | 9 |
| Manny | forward_shrug_reach | 13 |
| Manny | crossed_staggered | 4 |
| Manny | scan_abduct_-30 | 9 |
| Quinn | down | 1 |
| Quinn | back_down | 4 |
| Quinn | arms_crossed | 9 |
| Quinn | forward_shrug_reach | 52 |
| Quinn | crossed_staggered | 3 |
| Quinn | scan_abduct_-30 | 19 |

## 交付与后续

[交互查看页](../generated/revL/RevL_Shoulder_Review.html) · [Manny STEP](../generated/revL/manny/Manny_shoulder_assembly.step) · [Quinn STEP](../generated/revL/quinn/Quinn_shoulder_assembly.step) · [独立屈伸测角组件 STEP](../generated/revL/components/flex_encoder_assembly.step)

[44 轴状态](../mechanical_manifest/dual_character_mechanics_revL.json) · [CAD 清单，非采购表](../mechanical_manifest/revL_assembly_inventory.json) · [源文件与结果快照](revL_design_audit.json)

肩带测角、肘部传角、肩带／扭转持姿、轴向保持、完整线束、躯干和下肢等继续待设计。人偶本体不依赖固定外部支架，外部支撑物暂不设计；站、坐、躺尚未进入完整全身检查。原骨盆三轴实体参考待定，通道名称保留兼容性。UE 插件、Python 模拟器与原下载方案未修改。现在不用打印、采购或补测工具。
