fukawachan/PoseDollLab_Design/Hardware/PoseDoll44/verification/REVM_REPORT.zh-CN.md

# Rev M 完整数字原型验证报告

生成时间：2026-09-23T04:45:23.602021+00:00。状态：**完整数字原型候选，未制造放行、未实物鉴定**。

本次交付覆盖 Manny 与 Quinn 两款完整机械人偶。整体位置及全部整体旋转由 UE 手动调整；骨盆三槽为固定参考，其余 41 槽为测量。活动/形变部位裸露，稳定节段使用可拆刚性外壳。

## 两款整机结果

| 项目 | Manny | Quinn |
|---|---:|---:|
| 人物参考高度（mm） | 907.930 | 907.699 |
| 左臂肩至指尖总长 / 参考身高 | 0.403459 | 0.391168 |
| CAD 实体数量 | 1999 | 1999 |
| 打印候选 STL | 187 | 187 |
| 完整刚体离散姿态 | 164 | 164 |
| 发现相邻/内部结构交叠的姿态 | 0 | 0 |
| 41 轴测角几何复核次数 | 6744 | 6744 |
| 机械限位轴数 | 41 | 41 |
| 新增臂壳装配通道检查 | 18 | 18 |
| 含线束预留估重（kg） | 3.231 | 3.186 |
| 最小名义持姿 / 重力需求 | 1.564 | 1.630 |
| 线束跨度抽样比较次数 | 186240 | 186240 |
| 预算总输入电流（A） | 1.976 | 1.976 |
| 预算最低节点输入（V） | 4.074 | 4.074 |

两款关节中心与已提取人物比例基线一致；这不代表外壳逐点复制角色皮肤，也不保证 Quinn 的软件绑定无需额外适配。最小持姿余量对应 manny / waist.pitch, quinn / waist.pitch。

颈部使用 neck_01、neck_02 与 head 参考位置的等效共心枢轴；它不是 UE 的 head 骨原点。635 个最终配置离线样本中，头部参考点最大轨迹差异为 Manny 14.32 mm、Quinn 16.52 mm，超出此前 1% 身高的参考目标；躯干分布式转动带来的上肢根部差异约 3.68 / 3.86 mm。结果没有标成全姿态位置一致。当前交付保留 41 轴机制，后续目标适配或 IK 应单独评估接触姿势，Quinn 预测也不等于 live Control Rig 已验证。

## 碰撞、限位与测角

检查包含每轴端点/中点及全身组合动作，共每款 164 个离散姿态。体积超过 0.02 mm³ 的同体、同区域、相邻机构交叠计为结构问题；设计中的指定螺纹接触单独限定。每款 neutral、trunk_bend、arms_forward 三种姿态用不缓存的完整检查复核缓存结果。

保留的非相邻接触按用户确认的规则列为摆姿限制：Manny 42 个姿态，Quinn 49 个姿态。查看器以橙色标出；原始接触对和体积没有删除。不能把“结构项通过”解释为这些动作可以直接穿过别的肢体。

41 轴均检查允许端点内无止挡交叠、越界 1° 出现止挡接触。实体芯片/磁铁面核对及刚体变换检查确认名义 1.5 mm 气隙与同轴关系；这不是磁场、14 位实际精度或实体零点校准。

仅新增的六组臂壳固定点验证了直线刀杆、螺钉头与螺母进入通道；按独立臂段先装壳的顺序。没有对全部紧固件做自动装配运动规划。整机碰撞是离散采样，不是连续全关节空间无碰撞证明。

## 持姿、强度与打印

载荷计算检查 191 个相对姿态，对每姿态使用任意重力方向的轴向力矩上界。包含真实 CAD 零件质量估算、PCBA 质量分配及线束 15% 质量预留。PEEK 干摩擦系数 0.15、弹簧名义力均为待测假设；不包含线束恢复力、冲击、加速、磨损和 PLA 蠕变。

腰部名义持姿约 5.19 N·m，在 100 mm 有效力臂处理想操作力约 52 N。完整人偶约 3.2 kg，手感须与持姿能力一起验收。强度文件只列螺钉、螺纹、键面及梁的简化需求，没有执行 FEA、没有给出材料合格裕量或整机额定载荷。

187 个打印候选的名义包络均可进入 180 mm 打印空间并在 X/Y 保留 3 mm 裙边。Manny 右小腿梁最紧，含裙边约 179.55 mm。未实际切片；支撑足迹、层间强度、孔位和翘曲仍须首件验证。金属轴系、POM/PEEK、弹簧、PCBA 需要采购或加工。

STL 还经过逐件闭合边、尺寸与体积检查。每款有 6 个名义实体的相切边需要半径 0.10 mm 的小圆筋作为打印工艺修正，另附同名 `_print_process.step`。名义总装 STEP 保留设计基准，打印使用已经修正的 STL；全部修正件在同样 164 个姿态中检查了与整机其余部件的干涉，并回算质量与持姿需求。网格闭合仍不替代实际切片和强度验收。

## 电路、线束与数据

四套 KiCad 工程的 ERC、DRC 和原理图/PCB 一致性为零违规。两种传感器板、区域板、电源板均有原生工程、Gerber/钻孔候选、BOM 与贴装坐标。区域/电源板原生 STEP 缺 5 / 1 个供应商模型，整机 CAD 用相应尺寸包络补充。USB 阻抗叠层、散热过孔工艺与代料要由制板方确认。

每款线束包含 41 条传感器、5 条 CAN 和 6 条电源线。164 个检查姿态加 1,000 个随机姿态独立验证端点距离不超过预留跨度；这只证明长度上界，不是弹性线束避碰、弯曲疲劳或信号完整性模拟。电源预算用 150 mA MCU 分配及 80% 效率等假设；200 mA 敏感性工况另列，不能当作已经满足全部余量。

六个节点已在 ESP-IDF 6.1 构建并打包。离线验证：55 项 Python 测试、9 个 C 核心场景及 C/Python 黄金字节一致性通过。未烧录，未打开硬件端口，未采集实物数据。校准工具使用显式设备和角色绑定、至少三角度/轴；交付校准工单仍标为未测。

UE 插件与模拟器保留用户原先测试通过的状态。本轮只新增硬件诊断、实体校准流程及离线协议转换；正式实时桥接、Quinn 专属绑定和实体 Capture 仍需接入测试。

## 证据与执行入口

- [整机检查原始记录](revM_complete_audit.json) · [比例核对](revM_proportions.json) · [离线映射轨迹差异](revM_kinematic_mapping.json) · [装配通道](revM_cover_assembly_access.json)
- [打印网格检查](revM_print_exports.json) · [工艺变体记录](revM_print_mesh_export.json) · [变体干涉复核](revM_print_process_clearance.json)
- [重力/持姿预算](revM_load_work.json) · [强度与操作力需求](revM_strength_handling_screen.json)
- [电路检查与哈希](revM_electronics_package.json) · [固件镜像记录](revM_firmware_package.json) · [离线测试](revM_offline_tests.json)
- [Manny 线束/电源计算](revM_harness_power_manny.json) · [Quinn 线束/电源计算](revM_harness_power_quinn.json)
- [查看器检查](browser_revM/checks.json) · [文件指纹清单](../generated/revM/delivery_manifest.json)
- [完整交付入口](../START_HERE.zh-CN.md) · [装配手册](../docs/ASSEMBLY_REVM.zh-CN.md) · [分阶段实物验收](../docs/BUILD_AND_CALIBRATE_REVM.zh-CN.md)

先由加工方完成一套高负载关节和受力梁首件，再验证单板/最长线束、单肢与一款整机。当前无需一次制造两整套；上述待测项目都有验收入口，未填写为通过。
