fukawachan/PoseDollLab_Design/Hardware/PoseDoll44/docs/revO2_review_source/REVIEW_AND_ITERATION2_PLAN.zh-CN.md

# PoseDoll Rev O：第一轮独立审查与第二轮执行方案

审查对象：`fukawachan/PoseDollLab_Design`，分支 `design/revO-desktop-external`。
固定审查提交：`f59e4d3a7ea3d0940b1810702cd5e1df181e0364`；父提交：`458f3b0646f724f3b74769defc98f5f6e9ec45a8`。

本文件是一份设计审查与实现任务书，不是已完成的第二轮 CAD、PCB、固件补丁或制造放行文件。阅读范围包括审查请求、核心关节与电路生成器、尺寸/载荷计算、Manny 480 明细、关节报告、板级检查汇总、G0/区域节点与传输核心、离线结果和验收脚本。未独立重跑 CadQuery、KiCad、ESP-IDF、UE；没有实物试验。随包 Python 只重算明确列出的算术与条件调度场景，不能替代工程验证。

标记：**E = 已有源码/报告证据**；**C = 条件推算**；**P = 推荐设计、尚待建模/选型/实测**。以下任何新尺寸均为探索目标，除明确标注厂家规格外，都不表示现成零件或已通过布局。

## 1. 总体结论和不变项

继续以 480 mm 解剖参考进行紧凑化，不因为现有 40×66 mm 采集板放不进上臂就升到 550 mm。优先关闭“金属预紧路径是否成立、能否装入/拆出、真实板位与线束、8 ms 时序”的问题。保留已经实现的 G0/N1 职责分离、44 槽协议及故障状态语义。

第二轮推荐主线：**可径向装配的精密轴承盒 + 与测角轴向基准分离的浮动制动盘；高载荷关节先验证双摩擦面；N3/N4 各拆为胸腔近端控制板和上臂四路端口板；先关闭一个高载荷单关节和一条完整单臂，再展开整机。**

不改变以下要求：41 测量轴 + 3 骨盆固定参考槽；N1–N6 通道数 3/6/9/9/7/7；G0 不采样；现有动作清单；Manny/Quinn 各自比例；480 参考完整直立本体目标 ≤500 mm、最终硬限制 ≤600 mm；本体含所有内部部件目标 ≤1.2 kg；不对标准件全局缩放；不修改旧 5 V 板为可接 12 V；不用软件固定骨盆代替物理支撑设计；原 Rev N1 备份不变。

拆板增加物理 PCB 数，但不增加逻辑采集节点、传感器槽或 CAN 测量记录。本方案中 N3/N4 每个变为两块板，体内主要采集 PCB 因而可以从六块变成八块，仍是六个采集节点。新增板间接头和线束必须计入质量。

## 2. 优先级问题表

P0 表示阻止 B 级单关节或结构定型；P1 表示阻止板件定型/单臂/整机验收。不是“先把 P1 忽略”。

| ID | 级别/证据 | 触发与影响 | 必须修改 | 验收证据 |
|---|---|---|---|---|
| R01 新增 | P0 / E | `compact_joint.py` 后盖 z=-10…-7.4；壳体切掉 z<-7.4 的同轴材料，实际轴向螺纹重叠为 0。不是仅仅未画螺旋线；预紧反力没有可靠的后盖保持结构。 | 恢复实际金属承力后盖/压环及啮合段，定义螺纹中径/小径、啮合长、公差、肩面、防松；或采用另行验算的螺钉端板。 | 接触/保持图、螺纹参考几何、最小啮合与拔脱/剥牙计算；不能仅凭零相交通过。 |
| R02 对应 O-02 | P0 / E | S4 孔径 6 mm，转轴进入包络 8.4 mm；M6/L6 孔 8 mm、挡肩 9 mm。装不进去。 | 优先可径向闭合的精密轴承盒。拆开外壳但留下不可穿过的一体衬套不算解决。 | 逐步装配/拆卸轨迹、工装包络、每步自由度、闭合后的同轴度与锁定方式。 |
| R03 新增 | P0 / E+C | 预紧经过转子盘和前方 POM 垫片；注释中的“独立轴向基准”未由实际力路实现。垫片还构成未计入的一处摩擦接触。 | 将测角转轴轴向定位与制动夹紧分离；为每个受力环建立自由体图。 | 调节全范围、磨损与温度组合下的轴向位置/间隙预算；实测预紧变化对测角误差和零位的影响。 |
| R04 新增 | P0 / C | 0.06 mm 直径间隙、4.6 mm 支承长度对应约 0.75° 倾斜量级；不是实测读数误差，但不能忽略。 | 双支承或加长有效支承，精密定位，跑合后再确定配合。 | 实际载荷方向反转、倾覆力矩下的转轴摆角、回差与重复性。 |
| R05 O-01 | P1 / E | 九路板仍是裁短的旧布局；480 上臂的约 40 mm 轴向空间容不下 66 mm。反向跨关节的近端传感器支路也可能增加肩部线束。 | 按近端五路/远端四路重新组织 N3/N4；实件布局先于走线。 | PCB、配合头、线尾、拔插路径、保护罩及动作路径一起验证。 |
| R06 O-03/O-04，新增加载荷解释 | P0/P1 / E+C | 1387 g 是混合预算；整关节质量集中到轴节点，头部重力矩全零；仅用固定骨盆的子树重量不足以涵盖足底支撑。 | 逐零件材质、所属刚体、本地 COM；补支撑/接触工况；按每轴结果选规格。 | 质量账闭合、真实 COM、各支撑模式的受力报告与保持/操作力区间。 |
| R07 O-05/O-08 | P1 / E | 五种板未布线，九路板有 335 个未连接项，另有 12 个过孔规则问题；5 V 只是分配模型。 | 选板厂工艺、调整热焊盘孔实现，完成布线和全链路保护。 | 完整 ERC/DRC、零未连接、电源最坏角、板间/支路短路、USB 回灌验证。 |
| R08 新增具体反例，O-08 | P1 / C | 每次相同 EPOCH 仍触发六节点 BOOT/ACK，节点在阻塞发送后才处理已排队 SYNC；可使 8 ms 窗失败。 | 把稳定采样与入网维护分开，消除无条件周期 ACK 风暴。 | 事件调度回归、加入/重启/断线、8/14 ms 实测和新鲜批次统计。 |
| R09 O-06/O-07 | P1 / E | 工具用实心圆柱、插头用盒子；多轴、实际偏置、支撑和动作路径未完成。 | 建真实中空工具/配合头/线尾，补关节刚体 owner、轴变换与扫掠。 | 能装、能拆、能维护、带线动作路径及实际 profile 一致性。 |
| R10 证据链 | P1 / E | 若干门槛硬编码；验证器失败后仍跑依赖金样；现有总结果会失败，但后续局部 PASS 可能复用旧文件。 | 每次独立 run_id，依赖失败即 BLOCKED，报告必须有当前输入哈希及完整记录集。 | 故意删除/替换报告、制造前序失败时不能得到相关 PASS。 |

## 3. 机械方案：先修能否承力和装配，再谈缩小

### 3.1 后盖不是“画出螺纹就好了”

E：`compact_joint.py::module()` 里：

```python
cap = ring(ro-.05, r+.3, -10, -7.4)
rows[0]['shape'] = rows[0]['shape'].cut(cylinder(ro, -9.1, -7.4))
```

切除半径覆盖整段壳体外半径。报告中 S4 壳体最低 z 也确为 -7.4。后盖与壳体只有端面边界，没有提供螺纹所需的重叠材料。在后盖被弹簧向外推时，不能依靠这个端面“贴着”承载。

P：后盖保留金属螺纹调节方式作为紧凑首选，但必须有真实内外螺纹参考包络。初始研究有效啮合不少于约 3 mm，最终数值由选定螺纹、实际材料、边缘壁厚、最大预紧和供应商加工能力确定；3 mm 本身不是强度合格证。外形实心相交检查中，配合线程用明确匹配的螺纹对规则处理，同时单独检查啮合、端面、止退；不能通过删除母材让相交归零。端板螺钉备选也必须计入耳座、工具空间、剪切/拉力、质量和尺寸。

### 3.2 可装配关节方案对比

| 方案 | 推荐级别 | 优点 | 代价和必须证明的条件 |
|---|---|---|---|
| 可径向闭合的精密轴承盒，磁铁座随转轴保留 | 首选 | 不依赖磁铁座穿过小轴承孔；保留测角转轴与磁铁的稳定关系。 | 两半定位与重复装配精度、壳体/衬套装入路径；配合靠止口/销及成对加工，而不是螺钉孔间隙。 |
| 整体轴承座 + 可拆的正向定位磁铁座或挡肩 | 备选 | 外座加工简单，有机会减少外形凸出。 | 增加同轴度、轴向定位和扭转松动误差；必须用台肩、键/定位面和正向防脱，不可仅靠胶或顶丝摩擦固定。 |
| 只拆外壳、衬套仍一体；或只删除磁铁防脱/挡肩 | 不接受 | 外观看起来可装。 | 装配障碍或安全/定位问题仍存在。 |

P：工作轴颈仍先研究 4/6 mm。高载荷模块把有效支承跨度约 12–16 mm 作为第一轮探索，采用两个支承区；直径间隙约 0.02–0.03 mm 仅作为供应商审查起点，需考虑材料、温度、夹紧变形和润滑，不能直接用作所有轴的生产公差。若跨度 14 mm、直径间隙 0.03 mm，几何倾斜量级约 0.123°；该值不包含轴挠曲、盒体误差或磁铁误差。

支承长度不必全部加到关节外部，可优先利用原输出轴颈一侧安排第二支承。若必须增加轴向长度，应进入肩/髋嵌套碰撞检查，不能以局部精度改进掩盖整机变大。

建议装配顺序如下，必须由新 CAD 验证每一步，而不是只照文字通过：

1. 供应方加工并配对前后/左右轴承盒的定位面、衬套和转轴，先确认夹紧后的圆度、同轴度和轴向定位面。
2. 在轴上安装需要从输出端套入的零件。浮动制动盘的驱动键、轴向滑动行程及可拆输出端保持件必须允许这一顺序；不得在不可拆挡肩两侧生成无法套入的环件。
3. 转轴及其磁铁座就位后，轴承盒从径向围合。所有衬套和止推定位件也必须支持该路径；若某件仍需穿越大磁铁座，要重新设计。
4. 安装不承担制动预紧的轴向定位/防脱结构，检查转轴转动阻力和轴向游隙。
5. 再装摩擦定子、两侧摩擦片、压板、导向件、选定弹簧和金属调节后盖，形成封闭预紧力路。
6. 调节并检查制动盘仍能轴向浮动，转轴轴向基准不随预紧移动。
7. 最后装磁铁机械保持件、传感板、板夹和线缆；检测气隙，标定，记录供应方预装结果。

日常用户装配应以预装校准的关节芯为单位，不要求用户在家调整精密半轴承盒的配合。更换板件和外部线束应有独立维护路径。

### 3.3 预紧路径必须真正独立

E：旧路径是后盖→弹簧→带键压板→摩擦片→转子盘→POM 垫片→壳体。POM 垫片是轴向受力的一环，且转子与它有摩擦接触。径向衬套不承担轴向力，并不能推出整个轴向基准不受预紧影响。

P：先在高载荷 L6 类模块实现独立支承轴 + 轴向浮动制动盘。推荐的夹紧闭环是：金属壳体/前定子→前摩擦片→浮动制动盘→后摩擦片→压板→碟簧→金属后盖→壳体。制动盘通过正向驱动结构传递扭矩，但允许必要的轴向滑动；磁铁转轴由独立的轴向定位件保持位置。

必须分析：浮动结构卡死后的力路、驱动键回差、定子平面度、两侧压力分布、接触面积、磨屑、温升、弹簧偏载及最坏磨损。制动盘刚性锁死在轴上、然后声称轴向浮动，也不能通过。允许滑移量要覆盖公差和磨损；不能凭一个任意 0.1 mm 数字决定。

小关节之后按实际载荷派生，不要求把新增高载荷结构不加区别复制到 41 个轴。

摩擦件询价/样片任务应立即启动而非等待整机：L6 初始样片按当前外径 24 mm、内径 8.4 mm、单片厚约 0.6 mm 的环面提供图纸，以约 50–350 N 夹紧范围、低速手动起停和 1000 次初筛为试验条件，请供应方提供可追溯衬片材质、匹配金属表面、厚度/平面度公差和允许面压。这些是询价与筛选输入，不是任何材料已额定合格。测试至少区分首次起动、跑合、磨损后和不同装配预紧；无法提供可追溯材料与实测摩擦区间时，不锁定弹簧和量产图。

## 4. 保持力、弹簧与手感

### 4.1 保持力推算

E：Manny 480 的分配模型给出腰俯仰重力矩 0.238393 N·m；假设线缆 0.02 N·m，乘 1.5 后要求 0.387590 N·m。它不是已完成整机的最坏真实载荷。

C：沿用 L6 摩擦环外半径 12 mm、内半径 4.2 mm，最低假设 μ=0.08：

| 模型 | 有效半径 | 满足 0.387590 N·m 所需轴向夹紧力 |
|---|---:|---:|
| 原单面，均匀压力 | 8.72593 mm | 555.23 N |
| 双面，均匀压力 | 8.72593 mm | 277.61 N |
| 双面，均匀磨损近似 | 8.10 mm | 299.07 N |

因此优先比较两个受控摩擦面，而不是把 350 N 探索上限随意改成 600 N。仍需使用真实最小摩擦系数、弹簧最小力、接触/磨损/温度最坏角重新计算。均匀磨损也只是一个近似模型，不是所有磨损状况的包络。

在上述双面近似中，350 N 对应约 0.4536 N·m；相对于当前 0.3876 预算有余量，但不能直接作为放行依据。压力约为 299 N / 397 mm² = 0.753 MPa（每个完整接触面），还未计平面度、开槽或局部压力峰值。

### 4.2 用可追溯弹簧替代未定义的波簧占位

厂家来源 SCHNORR 2024-02 目录印刷第 11 页：002100 的外径 12 mm、内径 6.2 mm、厚度 0.5 mm、自由高度 0.85 mm；在约 0.75h0 的目录点为 326 N。002200 同外/内径、厚度 0.6 mm、自由高度 0.95 mm，对应目录点为 552 N。这两者只是曲线比较候选，不是推荐直接购买的最终件。

P：优先比较 002100 或 002200 的两片/四片串联组，使用供应商完整力—位移曲线及公差选择工作点。串联保持同级力而增加可用位移，利于降低磨损和调节误差带来的力变化；不以并联盲目提高刚度。

C：四片 002100 理想串联，自由高度 3.40 mm，目录工作点高度约 2.35 mm，弹簧本体约 1.24 g。当前 3.2 mm“工作空间”不能据此宣布可装入，因为还需自由态装入、导向、垫片、调节行程和拆卸空间。先以约 4–4.5 mm 弹簧腔空间进行封装研究，再按实际装配方式复核。

目录点不能代替实物保持力：尤其 326 N 相比上述 299 N 需求的余量不大，还要考虑弹簧力公差及摩擦不确定性。不得只取一行目录值就锁定零件。

### 4.3 两个摩擦面不会自动让人偶更好掰

C：按现有 μ 范围 0.08–0.22，若以低端 μ 调到满足保持要求，高端摩擦假设对应约 1.066 N·m。60 mm 握持力臂的“仅摩擦”操作力约 17.76 N；逆重力抬起时还需加上 0.2384 + 0.02 N·m，约为 22.07 N。

这不是实测手感，也不能把 0.22/0.08 当成测得的静/动摩擦比。但它暴露了原操作力公式只算摩擦、未算抬起/放下外载差别的问题。增加摩擦面主要降低所需夹紧力，不会在保持能力相同的条件下自动降低需要克服的制动扭矩。

修改载荷报告：分别列保持力矩、起动力矩、滑动力矩，抬起/放下两方向操作力，真实握持位置和邻接关节是否同时被带动。实测摩擦副的重复性比凭空提高 μ 更重要。用户无需预先选择摩擦系数；若最终需改成“松开锁钮才可摆姿”，才构成交互要求变更。

## 5. N3/N4 板件与线束：近端五路、远端四路

### 5.1 为什么不是再裁一次板边

E：当前 `build_revo_electronics.py` 从旧生成器拿元件和原位置，删端口后重画边框。九路板仍有 126 个元件、40×66 mm；导出的 XY 是真实库 courtyard，但 Z、配合插头和线尾仍多为假设。上臂 1D 放不下只说明这个布局失败。

### 5.2 推荐主线 A：控制/近端留胸腔，四路端口在上臂

保持每侧 N3/N4 的九路编号不变，将锁骨两轴、肩部三轴作为近端五路；肘屈伸、前臂扭转、腕屈伸/偏转作为远端四路。这里是网络分区，不表示五个传感器都固定在胸腔：肩部中间旋转件的线路仍需按真实所属刚体走线。

每侧布置：

- 胸腔内一块 MCU + CAN + 降压 + 近端五端口板，初始边界研究 36×48 mm。
- 上臂刚性段一块四端口板，初始边界研究 26×30 mm，保留每端口缓冲和保护/去耦。
- 两板间跨肩是共用 SPI + 四条 CS + 电源/回流，不增加 MCU 或 CAN 节点。

最少逻辑导线是 3 条 SPI + 4 条 CS + V3V3 + GND = 9 条，不应把它当成推荐物理线芯数。初始比较 14 芯线：3 SPI、4 CS、2 电源、5 GND；最终针序由信号回流与电流预算确定。各信号方向、保护、断电状态和 CS 上拉必须与当前端口语义一致。

参考连接器可研究 JST SM14B-SRSS-TB 的 14 路侧入头，与匹配的 SH 线端件配套；厂家头部宽 16 mm。四个传感器口使用 SM06B-SRSS-TB/BM06B-SRSS-TB 对应的六路 SH 头，宽 8 mm。厂家侧入头约 2.9 mm 高、顶入头约 4.25 mm 高，但必须加上配合头、针脚、线尾和动态弯曲，不把头部高度当作线束总高。

N3/N4 的 CAN 接口随 MCU 留在胸腔，避免为上臂 MCU 专门将 CAN 干线折返进手臂。原始近端传感器支路也不再被迫全部朝远端 MCU 汇集。净跨肩线芯数要按每条线的固定/转动 owner 统计，不能笼统宣称“所有肩部线都只剩 14 根”。

SPI 初始仍用 250 kHz。控制板—端口板连线先以 ≤120 mm、最远芯片路径 ≤250 mm 做工程长度预算，之后按真实走线调整；这不是 AS5048A 规定的通用距离极限，也不是 250 kHz 一定可用的保证。用端接候选阻值、真实柔性线、返回地和示波器测量建立条件；不能为了腾空间取消每端口三态隔离。 远端 SCK/MOSI 支路应有独立的驱动/源端阻尼研究，返回 MISO 的三态、源端阻尼和失电状态也须核对；不能把原来只在板内使用的共享 SPI 直接拉成长 T 形线而不增加验证。新增驱动器和阻尼件要纳入原理图、PCB、功耗和质量。

胸腔必须同时容纳 N2、N3、N4、真实胸腰/肩轴机构、插头和维护路径。若它们只能靠突出背包/胸包安装，主线 A 不通过。

### 5.3 备选 B 和换控制器的边界

| 方案 | 初始尺寸研究 | 线束/维护 | 判断 |
|---|---|---|---|
| A：胸腔五路控制板 + 上臂四路端口板 | 36×48 + 26×30 mm | 跨肩共享 SPI，检查断电与信号完整性；新增板间预压接线束 | 默认主线；先验证真实胸腔容积。 |
| B：整个 N3/N4 留在上臂，主控和九路端口折叠/叠放 | 主控约 32×36、端口约 32×34 mm；总厚度由实物决定 | 板间短连接不跨活动关节；近端传感器线和 CAN 仍要出入肩部 | 当 A 的胸腔确实容不下时启用；尤其检查臂横截面和抱臂/背手。 |
| C：换更小 MCU/取消模块 | 未定 | GPIO、供电、开发板转量产、固件端口和烧录均增加工作 | A/B 证实失败后再升级，不作为第一反应。 |
| 九路原始传感器线全移到外部桌面 | 无合理紧凑收益证明 | 大量跨关节导线，长 SPI 与柔性阻力 | 不采用。 |

两种板位研究应止于真实元件布局、线束和动作包络比较，选中后再完成布线；不需要先完成两套可制造 PCB。

### 5.4 可量化的封装修改

优先保留 ESP32-S3-WROOM-1-N8、TPS62162DSGR 和 TCAN332DR，不在第一轮引入新 MCU。WROOM-1 的厂家尺寸是 18×25.5×3.1 mm。所有板型重新布局，不复制旧板元件坐标。

端口缓冲可由 SN74LVC125APWR 的 TSSOP-14 换为 **SN74LVC125ABQAR** 的 WQFN-14，厂家尺寸由含引脚约 5×6.4 mm 变成 3×2.5 mm。九个缓冲芯片的名义封装面积差约 220.5 mm²；这不是 PCB 能减少同样面积的保证。更新厂家推荐焊盘、引脚对应、热/裸露焊盘连接和钢网，保持 OE/CS 上下电状态；小封装由 PCBA 厂完成，用户不手焊。

板可以研究四层结构，但线宽、孔径、层叠、阻抗/回流与装配工艺必须明确。不能把用更小封装或更多层写成“自动可布通”。

5 V 电源并未因拆板而自动保持六支路保护：每节点的支路必须包含其远端端口板和传感器用电；远端 3.3 V 线的压降、失联和信号回灌也要测试。

## 6. 质量和载荷模型必须一起重做

E：762.139 g 关节实体子集 + 625 g 工程分配 = 1387.139 g，超目标 187.139 g；这既不是实称，也不是完整 CAD 总质量。当前全部 sensor STEP 实体统一赋予 PCB 密度，钢针/塑料/芯片等材料没有区分。所有关节质量集中在轴节点，头部质量点同样位于节点，解释了头俯仰重力矩也为零的现象。

P：新增 `mass_properties_revO2.json`，每个实体具备 `part_id/material/owner/local_com/mass/mass_source/uncertainty`。PCBA 用元件质量或 PCBA 实称取代统一体积密度；未建模分配仍须保留并分项，不删除。轴承固定件归父刚体、转子归子刚体，实际线束分段归属，不把整模块都算到转动端。

支撑工况至少包含：骨盆被手或支撑件托住、双脚接触桌面、单脚/坐姿/跪姿、左右侧卧与俯卧。站立时踝/膝可能承受上身经接触反力传来的力矩，不能继续只算“骨盆固定时脚部后代的重量”。接触分配不确定时采用合理包络并注明假设，不给出虚假的唯一反力。

减重路线按以下顺序做，并交付每项前后体积/质量及新增零件账：

1. 先用真实质量和 COM 纠正预算；修正方向可能增重，不能只接受有利变化。
2. 在承载区域之外轻量化固定座、合并重复安装耳和 PCB 托；保持预紧闭环、定位面和螺纹根部材料。
3. 比较带加强筋铝压板 + 薄耐磨钢片，而不是把钢压板等厚换成塑料。
4. 按每一轴真实载荷、支撑模式和精度选族；取消 `family()` 仅靠名称硬绑定大规格的最终选型逻辑。
5. 最后优化外壳、头脚空腔和连杆截面；保留人体可握持形状和安全边缘。

C：按现有三档环面和 11/16/14 个数量，1.2 mm 钢压板的纯环面约 108.9 g。研究 1.5–1.8 mm 铝承力层 + 0.2 mm 钢耐磨片，纯环面可少约 34.6–43.9 g；未计定位键、加强筋、粘接/机械保持和新双面夹紧件，且须验证挠度。这不是已取得的整机净减重。

板件拆分首先解决位置，不是大幅减重。主线 A 的两个候选板总面积 2508 mm²，相比旧 2640 mm²，按 1.2 mm 和旧 FR4 密度，每侧裸板只少约 0.293 g；新连接器、线束可能使电子部分净增重。

建议设内部设计检查点：名义完整预算争取 ≤1150 g，留下约 50 g 不确定量，但正式用户目标仍是 ≤1200 g，不能用这个内部预算掩盖缺失零件。后续若无法达到，应提交真实超重来源和取舍，而不是修改分配数获得 PASS。

## 7. 电气、时序与数据有效性

### 7.1 已经可以保留的固件部分

E：Rev O 已以独立编译角色实现 G0；G0 不初始化 SPI，N1 三路腰数据经 CAN 接收。`pd_o_dispatch()` 覆盖 N1–N6，核心保留固定/缺失/故障字语义，批次开始会清除旧数据。这个改动方向正确，不需要回退成 N1 兼任网关。

### 7.2 相同 EPOCH 反复 BOOT/ACK 的具体风险

E：G0 每约 100 ms 发 EPOCH。区域节点对每一个 EPOCH 都阻塞发送 BOOT 和 ACK，即使 epoch 未变化；之后才从队列处理 SYNC。`acquire(e.us,...)` 把从 SYNC 的 ISR 接收时间到采样完成的时间与 8000 µs 比较，所以排队和控制发送消耗的时间属于采样窗。

C：随包脚本提供一个条件调度场景：相同 EPOCH 后，六节点均先处理该 EPOCH；G0 的 SYNC 优先上总线；BOOT ID 又高于 ACK 优先级，先完成六个 BOOT，再完成 ACK。沿用仓库每帧 135 bit、每轴 700 µs 的保守分配：

| 节点 | 处理 SYNC 前等待 | 采样分配 | 从 SYNC 接收到采样结束 |
|---|---:|---:|---:|
| N1 | 1.89 ms | 2.10 ms | 3.99 ms |
| N2 | 2.16 ms | 4.20 ms | 6.36 ms |
| N3 | 2.43 ms | 6.30 ms | 8.73 ms |
| N4 | 2.70 ms | 6.30 ms | 9.00 ms |
| N5 | 2.97 ms | 4.90 ms | 7.87 ms |
| N6 | 3.24 ms | 4.90 ms | 8.14 ms |

这个场景尚无 SDK 延迟，却已有节点超过 8 ms。它不是实物必然行为，也不是逐比特真实填充仿真；它足以说明常规 48.6% 总线占用和 11.49 ms 理想数据调度不能证明要求满足。

P：稳定状态的同一 epoch 不得无条件触发每个节点双回复。将新 epoch 建立、节点加入、重启与正常采样分状态，正常有效数据可以作为在线证据；入网/恢复握手采取定向或分时、限速，并保留超时重试和完整 boot/epoch 防陈旧关系。旧 epoch、旧 seq 和重启后的旧包不得接受；不能仅删除 ACK 破坏初次入网。

初次建立与故障恢复可以报告缺失/故障，但不能把这种时间窗纳入“全部正常有效”统计后伪称达到正常态指标。健康稳态、注入故障和恢复时延分别报告；分母和预热边界预先定义。

### 7.3 不优先靠提高 SPI 时钟或缩减诊断解决时序

E：当前每轴读取 5 个寄存器，每个 `read_reg()` 为命令 + NOP 两个 16 bit 帧，线上的正常读取共 10 帧，在 250 kHz 下是 640 µs，尚不含 SDK。

P/C：可研究相邻读命令的流水回应，将 5 次读组织为 5 个命令 + 最后一次取回，若厂家协议与台架证实等价，则纯线时为 384 µs，九路约少 2.304 ms。此次未取得并复核当前官方 AS5048A 完整 SPI 数据手册，故此项只列为优化研究，不能直接替换生产驱动。实现前必须确认 CS 帧间要求、返回数据归属、首帧丢弃、跨传感器切换、parity/EF、清错后的恢复，以及断线、非零 OTP 和磁场异常的语义一致。没有厂家序列依据时保留现有驱动。

保持 8/14 ms 门槛；补高优先级任务、绝对周期调度、回调/队列延迟记录。不能把 `vTaskDelay(1)` 的调度抖动忽略为零，也不能仅靠平均采样耗时放行。

### 7.4 99.9% 指标不能只看 presence

E：传输核心故意允许“节点在线且有 PD_FAULT 字”的完整诊断批次，这是正确的故障表达。presence=63 不等于 41 个角度正常。

P：健康台架分别记录：六节点新鲜批次率、41 个角度均正常的批次率、故障字比例、陈旧数据误判次数。故障注入时验证 PD_FAULT/PD_MISSING 和正常零角度的区分，不把故障字当可用于运动的正常样本。固定骨盆槽保持 PD_FIXED，不变成传感器读到的零。

### 7.5 电源与 PCB

C：沿用当前电流分配和 85% 降压效率，3.3 V 总负载预算约 6.026 W，输入约 7.089 W。1 m 的 24 AWG 电源对加 0.06 Ω 接触电阻，在电源 -5% 时：5 V 方案约 1.618 A、线末约 4.380 V、外线和接触损耗约 0.598 W；12 V 约 0.630 A、11.256 V、0.091 W。两者均未计内部干线、支路保护压降、启动电流和真实效率，不代表实物结果。

推荐本轮电气台架先保持 5 V/24 AWG 基线，完整建立保护、压降和温升模型。只有在满足供电余量与线缆柔性的情况下才定为最终；若无法满足，制作独立的 12 V 合格电路版本重新检查，不能将旧板直接接 12 V。

必须交付六个内部受保护分支、外部入口反接/过压或瞬态保护、连接器额定值/针序、远端端口板供电与失电 IO 状态、USB 仅数据/防回灌、G0 与 N4 两端端接，以及每段 CAN 的实际长度/支线/折返。星形供电不代表 CAN 可以星形连接。

0.2 mm 过孔有两条合法修法：确认供应商支持该孔径及焊盘/塞孔/钢网工艺后采用真实板厂规则；或改成规则允许的孔径并按模组推荐热焊盘重新排布。不得只缩小 DRC 最小孔径，也不能在拥挤焊盘内把所有孔机械改成 0.3 mm 而不检查短路/焊接。ERC/DRC 应包含 warning 审查与明确 disposition，不仅 errors；必须零未连接、检查原理图与板网表一致。

## 8. 文件改动和依赖顺序

新文件名为建议；可与仓库命名风格统一。不要运行 `Build-RevO.ps1 -Stage Initialize`。修改应在现有分支的新提交完成，保留审查快照和旧版独立生成目录。

| 次序 | 现有文件/建议新增 | 交付 | 前置条件 |
|---|---|---|---|
| 0 | `verify_revo.py`、`report_revo.py`、`build_revo_firmware.py`、`Build-RevO.ps1` | run_id、输入/工具链/输出哈希、依赖图、BLOCKED 状态；历史报告只读 | 固定 f59e4d3 为比较点 |
| 1A | `compact_joint.py`、`desktop_revO.json`；新增 `assembly_plan_revO2.json`、`load_path_revO2.json` | L6 装配版、实际后盖、径向轴承盒、独立轴向定位、浮动制动盘、弹簧候选 | 0；先画接口/剖面及装配顺序 |
| 1B | `build_revo_electronics.py`、`network_revO.json`；新增 `board_partition_revO2.json`、`harness_graph_revO2.json` | A/B 真实布局比较，近端/远端接口与端口一一对应，带线 3D 包络 | 0；与 1A 接口同步，不先布两套板 |
| 2 | `export_joints.py`；新增 `check_assembly_paths.py`、`check_load_paths.py`、`check_service_envelopes.py` | 拆装轨迹、约束/保持/线程啮合、动态间隙、真实工具验证 | 1A；不能靠相交表替代所有检查 |
| 3 | `study_revo.py`；新增 `mass_properties_revO2.json`、`support_cases_revO2.json` | 真实 owner/COM、支撑反力、分轴保持/操作力；重新确定 S4/M6/L6 选型 | 1A/1B 实体质量和装配方式 |
| 4 | 新 PCB 工程、实际连接器 STEP、弹簧/摩擦副图纸及报价需求 | 一套选中的可布线/可装配主板架构，B 级样件工艺包候选 | 2/3；供应方工艺确认 |
| 5 | `Firmware/PoseDollFullBody/revO/main/main.c`、`pd41_gateway.c`、G0 测试 | 握手状态机、调度对抗测试、当前协议回归；选做 SPI 流水研究 | 网络映射冻结；不改变旧核心/备份 |
| 6 | 新多轴 CAD、实际机械 profile；`revO_pose_cases.json` | 肩/髋/腕嵌套、完整单臂、位置偏置/镜像/限位和线束路径 | 单关节及板位数字门槛通过；真实摩擦/线束试验作为实物门槛 |
| 7 | 整机 CAD/线束/BOM/viewer 和生成报告 | Manny/Quinn 完整高度/质量/动作；完成 480 后比较 450/420 | 6；更大候选只在小型失败原因明确后研究 |

时序和证据脚本可与机械设计并行，但不能因固件通过就跳过机械门槛。不是要求用户先买齐全身件再测试。

## 9. 下一轮验收门槛

### V0：结果可追溯

每个报告必须包含提交、源文件及配置/参考 STEP 哈希、生成器/工具链版本、run_id、完整命令、退出码、输出哈希和测试范围。全套 PCB 必须恰好覆盖预期板型及逻辑节点，不能对空列表调用 all() 得到 PASS。解析失败/缺文件/错误 schema 都不能判 PASS。

测试运行目录隔离；上游编译失败时金样检查为 BLOCKED_DEPENDENCY，不读旧 golden。缺失本地 5.16 GB 备用输出应标 BLOCKED_MISSING_LOCAL_ARTIFACT，不能当作软件回归，也不能宣称备用版完整通过。当前历史总离线结果有实际退出码 0 的记录，不因为潜在证据链风险就追溯声称它造假。

### V1：能装、能拆、能承力

每一实体有正确刚体 owner 和固定/活动/服务角色；装配计划可逆；需要的防脱、键、螺纹、衬套、板夹和弹簧导向不是占位。预紧闭环以及承载连接成立；主轴轴向定位独立；最坏公差/温度/磨损下仍能装配和工作。必须计算动态小间隙，不能仅用“交叠体积低于阈值”来忽略小刮碰。

真实中空 pin-spanner 可绕过输出轴：内径按轴的最大包络、工具公差和装卸余量选择。例如 D6 对应内径约 ≥6.6 mm 只是首轮工具探索值；带联轴件/挡圈后的最大包络可能更大。该改动不允许将工具区域整体列白名单。

### V2：真实板位和线束

全部 PCBA、焊点/针脚、配合头、线尾、应力释放、固定件和可拆盖建模；主线 A 的胸腔三节点布局与远端板均通过；各节点完整端口数和管脚保留。检查上臂轴向及横截面、胸肩转动、维护通道、线束可达与弯曲。短 SPI 使用示波器确认上升/下降、振铃、门限/采样裕量；250 kHz 是时钟条件，不是长线认证。

### V3：保持/精度与实物单关节

沿用测试计划：全行程校准后误差目标 ≤1°，重复性 ≤0.3°；真实线束下持姿 60 s 漂移 ≤0.5°；邻轴转动引入的寄生读数变化 ≤0.3°，并区分机械串动与磁干扰；至少 1000 次代表性往返后复测。记录 30/60 mm 或实际可握持位置的正反操作力，不改变原阈值换 PASS。没有实际记录，保持 NOT_RUN_PHYSICAL。

### V4：板级与七节点电气台架

全 ERC/DRC、网表、零未连接、六支路保护和 USB 回灌检查完成。七个物理 CAN 节点、六份测量记录，500 kbit/s、60 Hz；最长节点从 SYNC 接收到采样完成 ≤8 ms，批次合格数据接收 <14 ms（核心的 14 ms 边界是拒收，测试需要明确严格边界）；分别记录排队、采样、CAN、USB和调度延迟。

健康台架至少 30 min，完整新鲜批次目标 ≥99.9%，同时报告全 41 轴正常值批次率；陈旧/故障冒充正常新鲜角度为 0。故障实验覆盖每个节点和传感器的断线、启动、重启、欠压以及队列压力；专门覆盖相同 EPOCH 和新 epoch。不能扩大采样窗或把故障帧算作正常角度来满足指标。

### V5：单臂→整机→UE

真实肩/髋/腕轴偏置、关节嵌套和镜像方向进入 device profile；解剖参考文件不能作为已校准机械 profile。动作包含原清单，侧卧/俯卧要有世界姿态、支撑接触与外接线，不能保留空角度字典当作已检查。

先 5° 路径采样，近接触按 1° 或适应细分/扫掠；离散结果只覆盖所检查轨迹，不宣称连续全空间。除不穿透，还要保证线材应变、松弛和连接器不受拉，允许接触只限明确的人体/支撑接触对，不能整个相邻机构白名单。

完整直立本体目标 ≤500 mm（480 参考），硬限制 ≤600 mm；本体全部内部部件 ≤1.2 kg，外置盒和外接线分别记录。先数字质量，再实称确认。最后验证实际标定后的 Capture、Undo/Redo、Clutch、区域遮罩和冻结后编辑。通过 V1/V2 不表示 V3–V5 已通过。

## 10. 只有用户才能决定的取舍

目前建议不修改任何目标；板型拆分、小封装 PCBA、精密轴承盒和电源详细实现属于设计工作，不需要把这些普通技术选择推给用户。

仅在数据证明必要时请求：放宽 480 参考对应的 ≤500 mm 完整本体目标、接受超过 1.2 kg、改变可直接掰动的交互（例如每次需解锁）、放弃某个既定动作，或引入改变原主控/传感器基线且增加预算/重验证范围的架构。未经用户明确同意不得越过硬限制或删轴。报价尚未取得，不能宣称本路线更便宜或给出虚假的到手成本。

## 11. 证据入口

仓库链接全部固定到审查提交；后续应在自己的提交中生成新证据而非覆盖旧记录。

- [审查请求](https://github.com/fukawachan/PoseDollLab_Design/blob/f59e4d3a7ea3d0940b1810702cd5e1df181e0364/Hardware/PoseDoll44/docs/REVIEW_REQUEST_REVO.zh-CN.md)
- [状态总表](https://github.com/fukawachan/PoseDollLab_Design/blob/f59e4d3a7ea3d0940b1810702cd5e1df181e0364/Hardware/PoseDoll44/verification/revO/status.json)
- [关节源码](https://github.com/fukawachan/PoseDollLab_Design/blob/f59e4d3a7ea3d0940b1810702cd5e1df181e0364/Hardware/PoseDoll44/cad/revO/compact_joint.py)
- [关节生成与检查](https://github.com/fukawachan/PoseDollLab_Design/blob/f59e4d3a7ea3d0940b1810702cd5e1df181e0364/Hardware/PoseDoll44/cad/revO/export_joints.py)
- [关节参数](https://github.com/fukawachan/PoseDollLab_Design/blob/f59e4d3a7ea3d0940b1810702cd5e1df181e0364/Hardware/PoseDoll44/mechanical_manifest/desktop_revO.json)
- [关节原始报告](https://github.com/fukawachan/PoseDollLab_Design/blob/f59e4d3a7ea3d0940b1810702cd5e1df181e0364/Hardware/PoseDoll44/verification/revO/joint_study.json)
- [尺寸/质量/时序计算](https://github.com/fukawachan/PoseDollLab_Design/blob/f59e4d3a7ea3d0940b1810702cd5e1df181e0364/scripts/study_revo.py)
- [Manny 480 明细](https://github.com/fukawachan/PoseDollLab_Design/blob/f59e4d3a7ea3d0940b1810702cd5e1df181e0364/Hardware/PoseDoll44/generated/revO/layouts/manny_480/study.json)
- [电路生成器](https://github.com/fukawachan/PoseDollLab_Design/blob/f59e4d3a7ea3d0940b1810702cd5e1df181e0364/scripts/build_revo_electronics.py)
- [沿用的元件/网络定义](https://github.com/fukawachan/PoseDollLab_Design/blob/f59e4d3a7ea3d0940b1810702cd5e1df181e0364/Hardware/PoseDoll44/tools/build_regional_revM.py)
- [电气检查汇总](https://github.com/fukawachan/PoseDollLab_Design/blob/f59e4d3a7ea3d0940b1810702cd5e1df181e0364/Hardware/PoseDoll44/verification/revO/electronics_placement.json)
- [电源/布线说明](https://github.com/fukawachan/PoseDollLab_Design/blob/f59e4d3a7ea3d0940b1810702cd5e1df181e0364/Hardware/PoseDoll44/docs/WIRING_AND_POWER_REVO.zh-CN.md)
- [固件入口](https://github.com/fukawachan/PoseDollLab_Design/blob/f59e4d3a7ea3d0940b1810702cd5e1df181e0364/Firmware/PoseDollFullBody/revO/main/main.c)
- [G0 分发](https://github.com/fukawachan/PoseDollLab_Design/blob/f59e4d3a7ea3d0940b1810702cd5e1df181e0364/Firmware/PoseDollFullBody/revO/main/pd41_gateway.c)
- [传输核心](https://github.com/fukawachan/PoseDollLab_Design/blob/f59e4d3a7ea3d0940b1810702cd5e1df181e0364/Firmware/PoseDollFullBody/main/pd41_core.c)
- [离线验证器](https://github.com/fukawachan/PoseDollLab_Design/blob/f59e4d3a7ea3d0940b1810702cd5e1df181e0364/scripts/verify_revo.py)
- [离线原始结果](https://github.com/fukawachan/PoseDollLab_Design/blob/f59e4d3a7ea3d0940b1810702cd5e1df181e0364/Hardware/PoseDoll44/verification/revO/offline/results.json)
- [门槛汇总生成器](https://github.com/fukawachan/PoseDollLab_Design/blob/f59e4d3a7ea3d0940b1810702cd5e1df181e0364/scripts/report_revo.py)
- [现有验收要求](https://github.com/fukawachan/PoseDollLab_Design/blob/f59e4d3a7ea3d0940b1810702cd5e1df181e0364/Hardware/PoseDoll44/docs/TEST_PLAN_REVO.zh-CN.md)

厂家资料（本次核对封装/目录页，不代表已完成板级或机械资格鉴定）：

- [TI SN74LVC125A，Rev T，p1 封装表，订货表 BQAR](https://www.ti.com/lit/ds/symlink/sn74lvc125a.pdf)
- [Espressif ESP32-S3-WROOM-1/1U v1.8，印刷 p42 尺寸](https://www.espressif.com/sites/default/files/documentation/esp32-s3-wroom-1_wroom-1u_datasheet_en.pdf)
- [JST SH 官方目录，p3 接头尺寸](https://www.jst-mfg.com/product/pdf/eng/eSH.pdf)
- [SCHNORR 2024-02，印刷 p11 弹簧尺寸及工作点](https://www.schnorr-group.com/fileadmin/4_Downloads/Brochures/SCHNORR_Produktbroschuere_EN_2024-02.pdf)
- [TI TPS6216x 数据手册](https://www.ti.com/lit/ds/symlink/tps62162.pdf)
- [TI CAN Physical Layer Requirements](https://www.ti.com/lit/an/slla270/slla270.pdf)
- [Infineon AS5048A 产品页](https://www.infineon.com/part/AS5048A)。本次产品页可读，但完整 SPI 手册链接未能取回；SPI 流水项因此保留为有条件研究。

随包 `review_calculations.py` 与 JSON 是可复算的独立算术，不是本仓库生成器的替代品，也不得导入 `status.json` 后让任何 CAD/硬件项变 PASS。
