fukawachan/PoseDollLab_Design/Hardware/PoseDoll44/generated/revM/electronics/THIRD_PARTY_NOTICES.md

# Third-party library notice — Rev M electronic design package

Pinned KiCad symbols, footprints and associated 3D library models originate from the installed KiCad 10 official libraries, compiled by the KiCad community. Original names and available in-file source/author metadata are retained in the project libraries. Project edits include board-specific connectors/envelopes, pin definitions and local model paths.

KiCad libraries use Creative Commons Attribution-ShareAlike 4.0 with KiCad's electronic-design exception. The official license and exception are at:
https://www.kicad.org/libraries/license/
https://creativecommons.org/licenses/by-sa/4.0/legalcode

This notice does not assign a new license to the user's repository or third-party semiconductor documentation. Manufacturer names identify components; no manufacturer approval of PoseDoll is implied.

`GRM219R61E106KA12D_max_with_solder.step` and the additional maximum-size envelopes in the mechanical assembly were generated for this design from cited dimensions. They are not vendor-supplied exact models. Regional and power `board_native.step` exports lack some vendor models; use the full mechanical assembly for the stated allocation checks.

The local library copy is a design-specific subset. Retain this notice and the corresponding library license documents when redistributing it.
