fukawachan/PoseDollLab_Design/Hardware/PoseDoll44/verification/REVC_REPORT.zh-CN.md

# Rev C 数字设计审查

**已完成这一版的数字检查；整机尚未达到制造放行状态。现在无需打印、采购或填写测量表。**

## 当前证据

- 保留原来的 44 路轴 ID、排列、父子链和正方向；实体轴位单独导出。
- 全身模型 251 个装配对象，中立姿势无实体穿插。13 个离散姿势中 12 个无穿插。
- 保留的碰撞：双腿外展 60° 且双臂垂下时，手腕与膝叉架相碰；把双臂外展 35° 后，同样的腿部姿势无穿插。没有从报告中删除原测试姿势。
- H2 三种独立摩擦夹具：所有零件实体有效，所有非预期零件相交为零；每种按 15° 步长检查一圈，共 72 个角度样本，无动静干涉。
- 12 个打印 STL 为闭合网格，逐件在 160 mm 包络内。它们仍是研究件，不是整机打印包。
- 18×20 mm 双面 AS5048A 板：ERC、DRC、未连接项和原理图一致性均为零违规。

## 负载与需要继续解决的问题

当前质量预算 2.01 kg，含未建模五金/节点/线束余量；它不是实际 BOM 称重。357 个重力情景中，pelvis.pitch 的样本保持目标最高，为 2.52 N·m。对应的全配置三角不等式上界目标为 6.91 N·m。两者分别是抽样设计依据和保守上界，不能混称为已证实的最大负载。

H2 是便于逐层检查的独立夹具。按当前轴分级直接复制，光这些夹具就约 7.55 kg，不能装进 2.01 kg 的全身预算。正式关节必须与叉架共用支座，减少重复金属框架，再重新计算质量、运动和持姿力。

完整摩擦组件、最终紧固件、线束/插头弯曲空间、固定支架、区域节点与网关都还没有进入全身可制造装配。**这些是尚未完成的设计工作，不能归因于用户没有实测。**

## 可查看的文件

- [最新入口](../START_HERE.zh-CN.md)
- [全身 STEP](../generated/revC/step/HW44_revC_candidate.step)
- [H2 结构与装配说明](../docs/H2_CLUTCH.zh-CN.md)
- [完整机器可读审查](revC_review.json)
- [全部碰撞样本](revC_motion_samples.json)
- [负载计算及每项质量假设](revC_load_sizing.json)

全部物理验收继续保持 not_run/null。数字检查没有覆盖实物摩擦、磁场串扰、磨损、供电、总线和 UE 全身实时链路。
