fukawachan/PoseDollLab_Design/Hardware/PoseDoll44/verification/REVE_REPORT.zh-CN.md

# Rev E 双角色比例与运动检查

## 当前结论

**Manny、Quinn 两款的中立比例基准已建立并通过数字检查；动态一致性与机械制造均未放行。**

| 检查 | Manny | Quinn |
|---|---:|---:|
| 44 轴 ID、顺序、轴定义、父子链保持不变 | 通过 | 通过 |
| 主要肢体长度、肩宽、髋宽，相对误差 ≤ 1% | 通过 | 通过 |
| 中立骨骼标志点误差 ≤ 身高 0.5% | 通过 | 通过 |
| 14 组多轴目标中心 | 组内间距为 0 | 组内间距为 0 |
| 参考 STEP 几何有效性 | 92 个有效参考实体 | 92 个有效参考实体 |
| 独立运动比较 | 1087 个样本 | 1087 个样本 |
| 最大手腕位置误差 | 2.399 mm | 2.516 mm |
| 最大头部位置误差 | 9.547 mm | 11.014 mm |
| 动态位置目标：身高的 1% | ≤ 6.053 mm，未通过 | ≤ 6.051 mm，未通过 |
| 该角色既有 UE 适配 | 5 组已有引擎结果用于交叉核对 | 尚未完成 |
| 新实体配置在 UE 中验收 | 未运行 | 未运行 |
| 实际装配/持姿/测角/寿命测试 | 未运行 | 未运行 |

数字模型的长度误差接近浮点运算精度，只说明参数一致，不代表打印或装配能达到同样精度。

## 为什么颈部没有通过

最大误差发生在头部 yaw=75°、pitch=55°、roll=35° 同时达到上限时。当前人偶以一个共心三轴关节转动头部；UE 分别转动 neck_01、neck_02、head，头部的位置轨迹因此不同。Manny 偏差约 9.55 mm，Quinn 约 11.01 mm。四肢比例已经纠正，颈部仍需机构和目标适配联合设计。

进行了两种枢轴调整研究：移动单个共心枢轴，以及分别移动颈部三轴。后一方案在拟合姿势中误差较小，但在未参与拟合的极端姿势中仍失败，因此**没有应用到正式参数**。不得把拟合样本通过当作全范围通过。

[单枢轴研究](revE_neck_pivot_study.json) · [分轴研究](revE_distributed_neck_pivot_study.json)

## 检查方法和适用范围

每款有 232 个设计样本（16 个命名姿势、88 个单轴端点、128 个随机组合），另有 855 个独立样本（不同随机种子的 512 个组合及 7×7×7 的颈部网格）。每个样本用物理参数做正向运动学，再与角色自己的中立骨长及 UE 的旋转分配规则比较，不是只从同一张 CAD 图上重复量尺寸。

Manny 的预测模型另与仓库保存的 5 组实际 UE 骨骼结果交叉核对，最大差异约 0.000012 mm。这证明当前坐标转换和骨链推导与那些已有样本一致；本轮没有重新执行真实 Control Rig 采集与关键帧写入验收。

Quinn 的预测使用她自己的网格骨长；当前导出的共享 Control Rig 初始骨架与她的网格参考骨架最大相差约 17.90 mm（1:3 尺度）。因此 Quinn 的离线比较不能代替她在 UE 中的验收。需要独立适配、指纹和 N 姿势校准。

双手靠拢与手到额头样本已经按参考表面的指定指端点求解到达；这只证明点可达，不证明整个手掌贴合、不穿插、能操作或站得稳。全身零件干涉、握持外形、地面接触及固定支架还要在实际机构模型中检查。随机角度组合也不等于全部可实现的动作范围。

## 提取与出处

参考数据来自当前本地 UE 5.8.2 项目：每款 89 根网格参考骨骼，Manny 46,098 个顶点 / 92,178 个三角形，Quinn 43,761 个顶点 / 87,280 个三角形。使用 GeometryScript 从临时 DynamicMesh 读取几何及权重，不保存或改写角色资产。网页仅使用减面后的显示数据；所有尺寸和运动计算使用完整源数据。

提取使用独立无界面 UE 进程；早期 FBX 导出在 NullRHI 下失败，正式结果来自后续 GeometryScript 路径。该进程完成两套 JSON 后，因项目已有的 GameFeatures AssetManager 错误返回 1；因此记录的是“提取文件完整且读取成功”，不是“命令行项目检查全部成功”。相关输出保留在 `reference_export_ue.log` 和 `reference_export_console.log`。

- [原始提取登记](../reference/ue58/extraction.json)
- [两款尺寸与来源哈希](revE_proportion_baselines.json)
- [全部角度和误差明细](revE_kinematic_comparison.json)
- [CAD 参考实体登记](revE_layout_geometry.json)
- [数字设计登记表](../mechanical_manifest/dual_character_design_revE.json)

## 下一阶段

围绕正确的肩、髋等中心重做承力叉架与共心结构，集成摩擦组件、传感器和走线；解决颈部运动差异；为 Quinn 做独立 UE 适配；用两款完整装配重新计算质量、保持扭矩和支架负荷，再生成最终装配与打印包。旧 Rev C 全身比例已经被替代，旧关节研究与电路成果仍可继续使用。
