fukawachan/PoseDollLab_Design/Hardware/PoseDoll44/cad/revG/shoulder_review.template.html

POSEDOLL 44 · REV G · HUMAN FORM STUDY

# 分段保留人形，活动区域保持裸露

Manny / Quinn · 约 90.8 cm 候选尺寸 · 肩带运动参考 · 稳定部位包壳，形变部位裸露

正面侧面斜侧面运动参考点重置视图

拖动旋转 · 滚轮缩放
完整体表仅作比例与动作参考；实体肩带保持裸露。

## 原有肩带两轴的作用

0.0 mm

当前左肩中心相对自然姿势的位移

方向 | 位移 / mm

肩带及上臂骨架参考线胸背参考点（不是外壳安装点）随肩移动的参考点（该区裸露）

当前外壳规则

上臂、前臂等稳定主体保留分段硬壳。肩带、肩胛活动区、腋下和关节连接区露出机械骨架。

不设置软皮、关节护套或浮动肩盖。壳片只固定于单个刚性节段，并在运动区提前收边。

当前验证边界

44 轴模型已有肩带前伸／后收及抬降。新比例下的实体肩带机构、完整壳边、走线与实际抓握仍未验证。

绿色与橙色点显示相对运动，不能理解为两点之间将安装外壳。

分段硬壳与裸露区域设计说明
截面、位移与检查结果
Quinn 弯肘 145° 与裸露活动区
Quinn 中线臂壳 CAD 研究
