fukawachan/PoseDollLab_Design/Hardware/PoseDoll44/references/migrated_datasheets/JST_SH_drawing.png

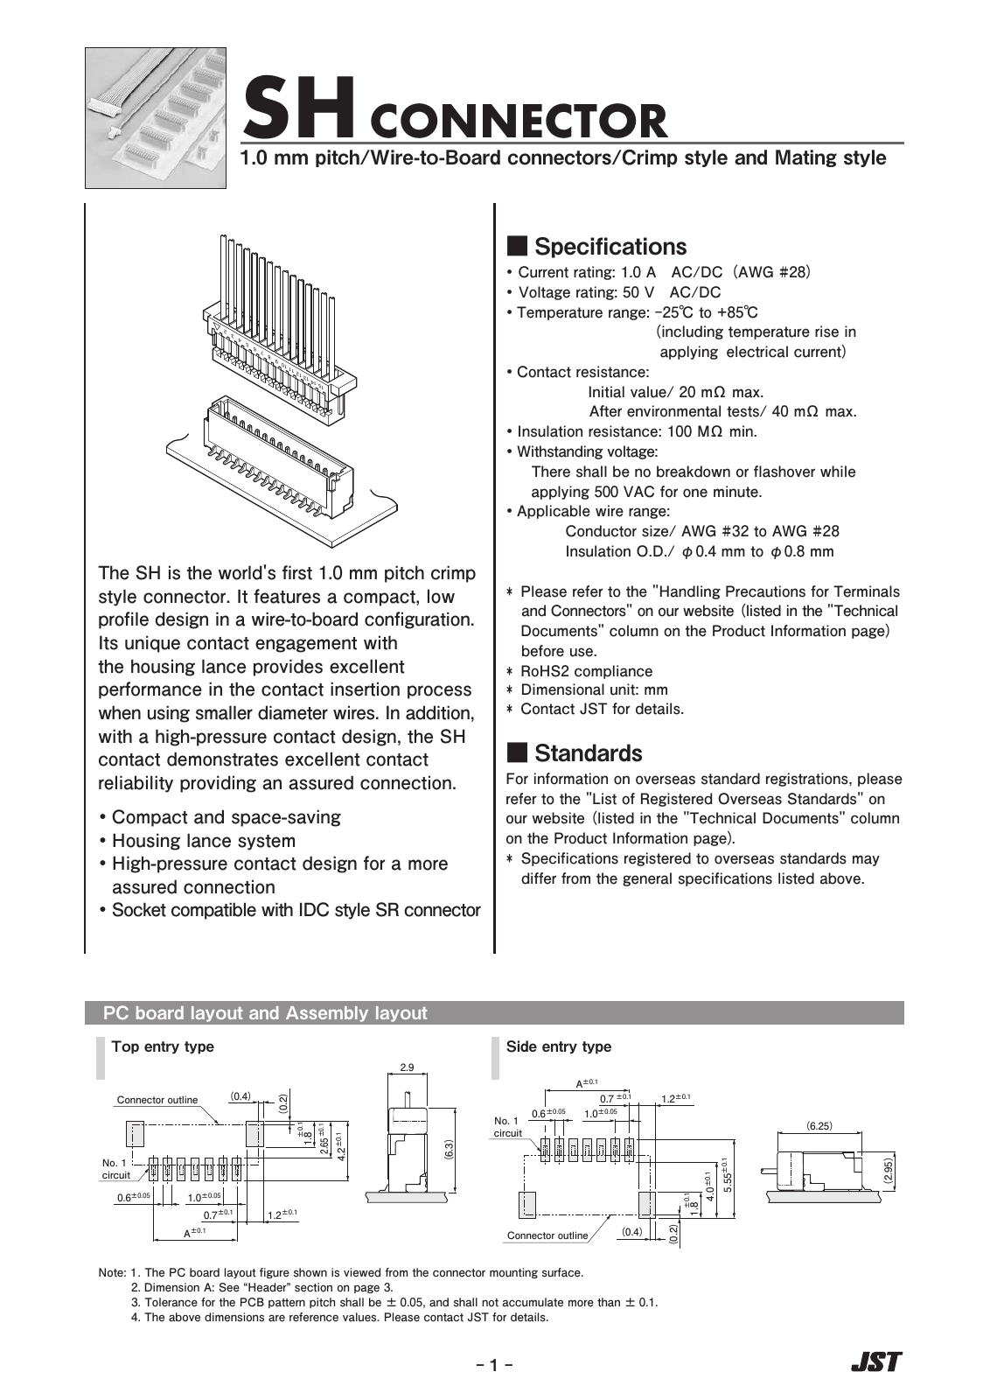
Hardware/PoseDoll44/references/migrated_datasheets/JST_SH_drawing.png
