fukawachan/PoseDollLab_Design/Hardware/PoseDoll44/references/migrated_datasheets/PJ-002AH_drawing.png

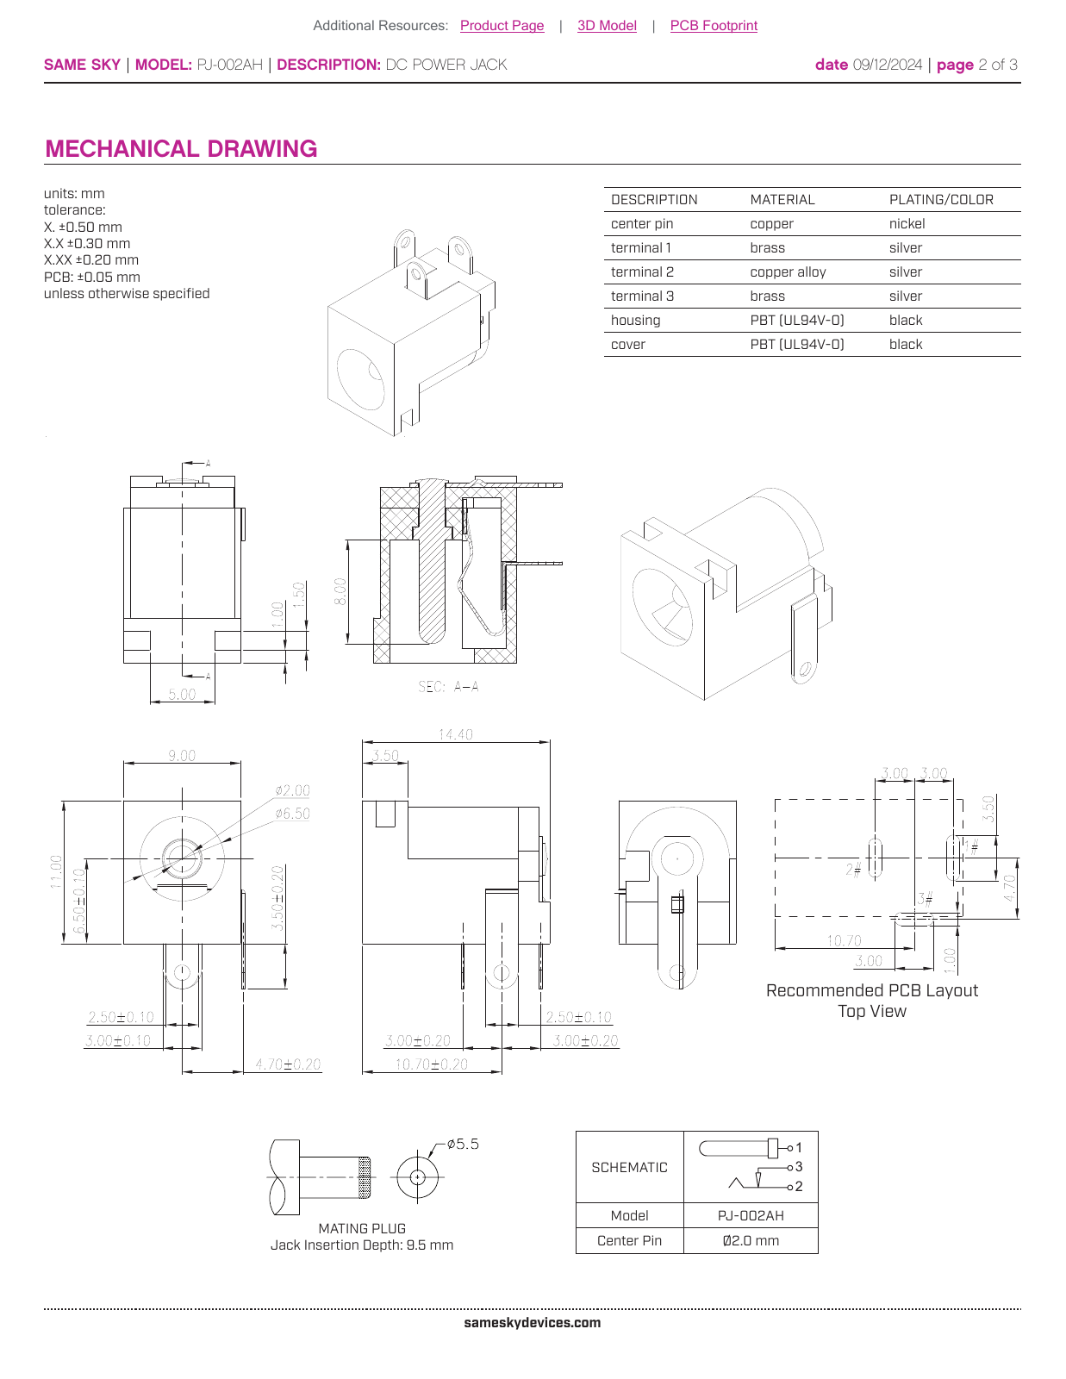
Hardware/PoseDoll44/references/migrated_datasheets/PJ-002AH_drawing.png
