fukawachan/PoseDollLab_Design/Hardware/PoseDoll44/references/revK/FH19C_drawing-2.png

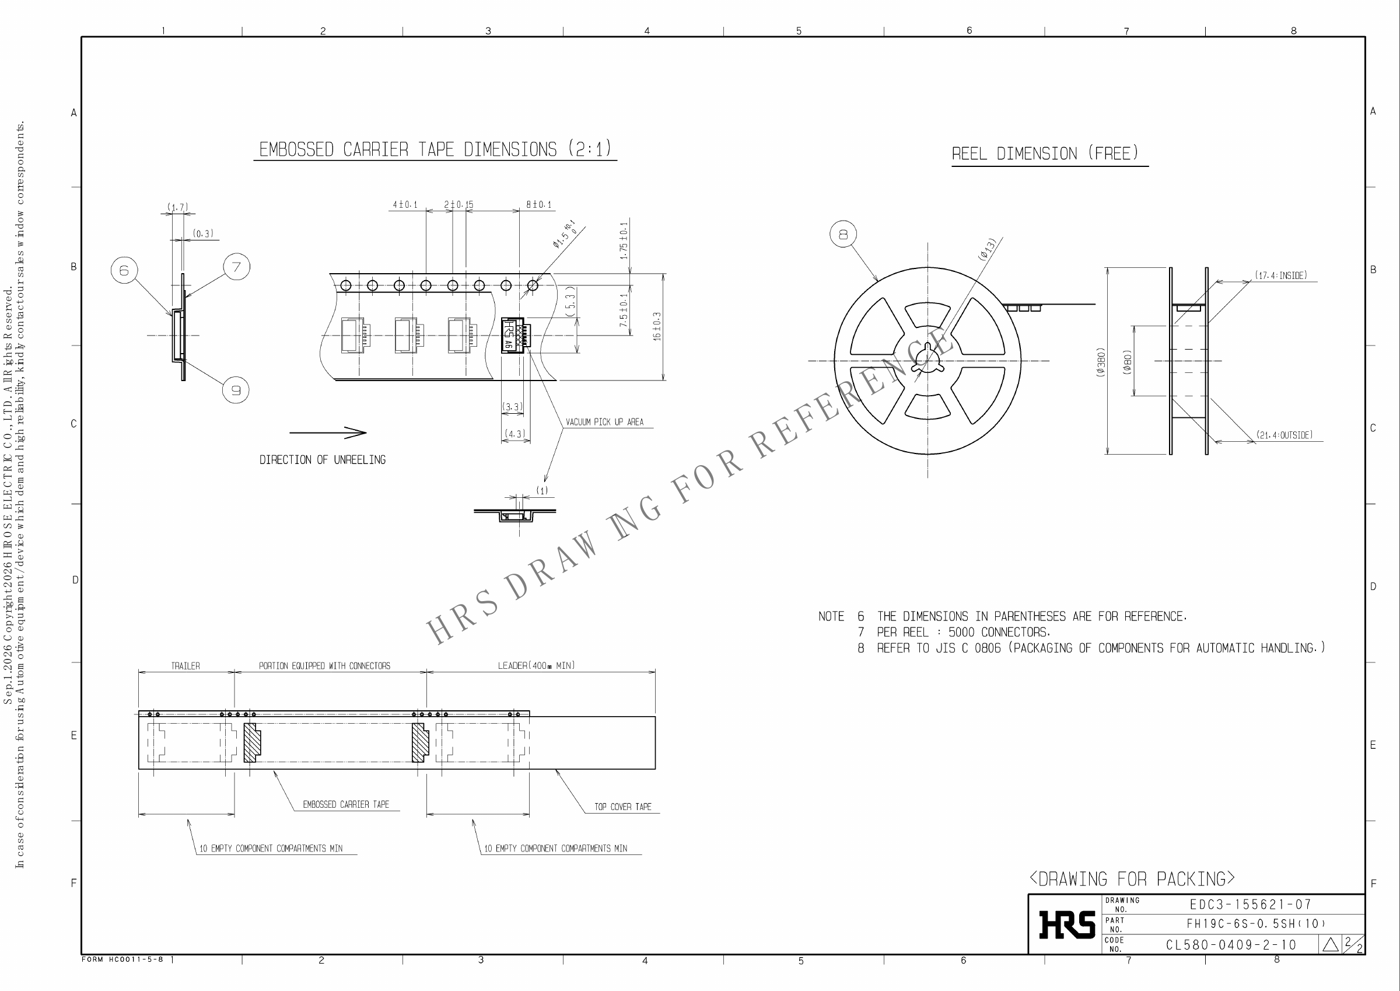
Hardware/PoseDoll44/references/revK/FH19C_drawing-2.png
