fukawachan/PoseDollLab_Design/Hardware/PoseDoll44/verification/browser_revM/electronics.png

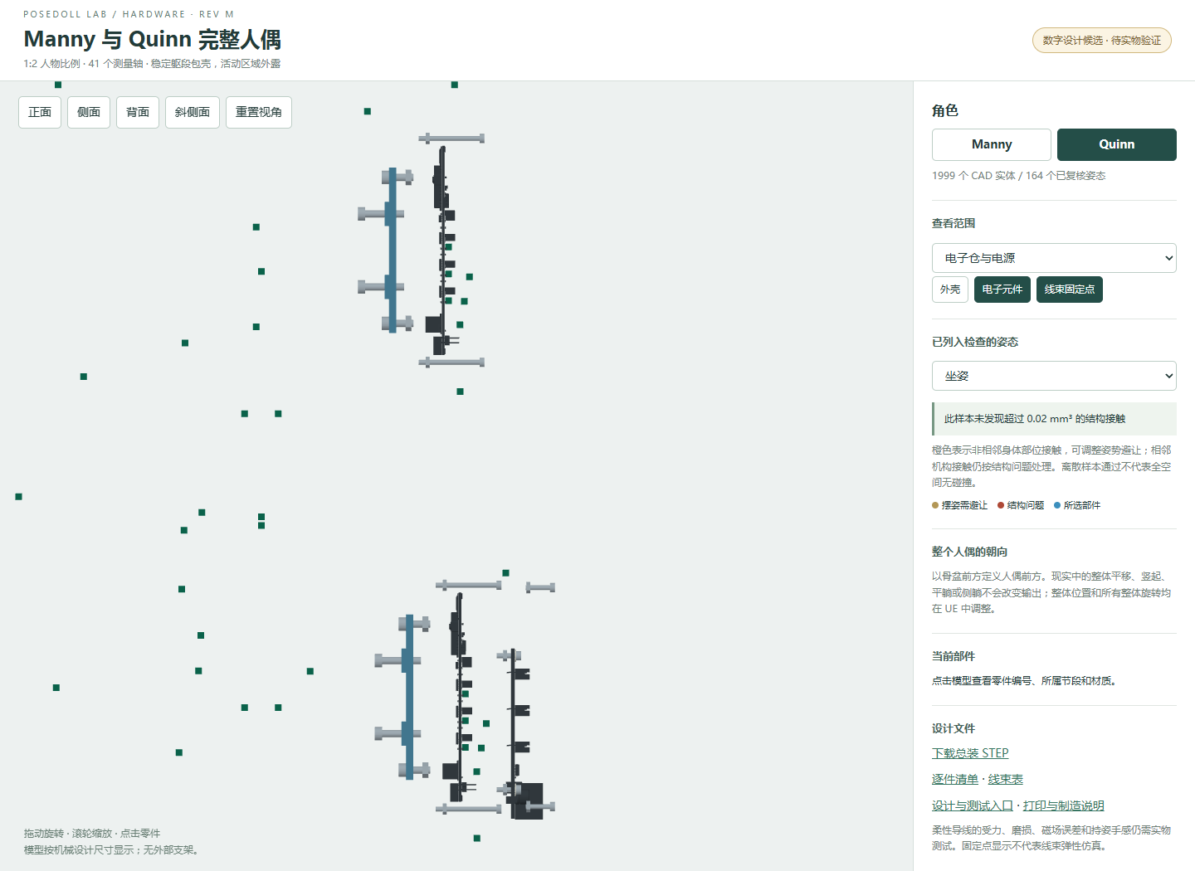
Hardware/PoseDoll44/verification/browser_revM/electronics.png
