fukawachan/PoseDollLab_Design/Hardware/PoseDoll44/verification/revO/physical_test_log_template.csv

test_id | date | operator | specimen | material | nozzle_mm | layer_mm | nominal_dimension_mm | measured_dimension_mm | instrument | uncertainty_mm | raw_log_path | status | notes
A01 |  |  |  |  |  |  |  |  |  |  |  | NOT_RUN
A02 |  |  |  |  |  |  |  |  |  |  |  | NOT_RUN
B_angle |  |  |  |  |  |  |  |  |  |  |  | NOT_RUN
B_holding |  |  |  |  |  |  |  |  |  |  |  | NOT_RUN
C_crosstalk |  |  |  |  |  |  |  |  |  |  |  | NOT_RUN
D_arm |  |  |  |  |  |  |  |  |  |  |  | NOT_RUN
E_electrical_30min |  |  |  |  |  |  |  |  |  |  |  | NOT_RUN
F_full_body_UE |  |  |  |  |  |  |  |  |  |  |  | NOT_RUN
