fukawachan/PoseDollLab_Design/Hardware/PoseDoll44/generated/revM/manny/procurement_routes.csv

part_id | owner | category | material | quantity | candidate_part_number | thread | length_mm | fastener_form | CAD_envelope_mm | action | STEP | STL | note
l_yaw_bush_top | chest | 加工塑料 | pom | 1 |  |  |  |  | 6.0 x 6.0 x 10.0 | POM-C / 未填充 PEEK / PA12 按材质分别加工；薄件不等同 PLA 打印 | parts/l_yaw_bush_top.step |  | Machined POM-C plain sleeve. CAD is installed/compressed state; free OD is +0.030 +/-0.005 mm above nominal, housing bore +0.000..+0.010. Finish running bore after installation. No clutch axial preload. Pull-out and thermal qualification required.
l_yaw_bush_lower | chest | 加工塑料 | pom | 1 |  |  |  |  | 6.0 x 6.0 x 8.0 | POM-C / 未填充 PEEK / PA12 按材质分别加工；薄件不等同 PLA 打印 | parts/l_yaw_bush_lower.step |  | Machined POM-C plain sleeve. CAD is installed/compressed state; free OD is +0.030 +/-0.005 mm above nominal, housing bore +0.000..+0.010. Finish running bore after installation. No clutch axial preload. Pull-out and thermal qualification required.
l_elev_bush_27 | clavicle_l.protract_frame | 加工塑料 | pom | 1 |  |  |  |  | 6.0 x 6.0 x 6.0 | POM-C / 未填充 PEEK / PA12 按材质分别加工；薄件不等同 PLA 打印 | parts/l_elev_bush_27.step |  | Machined POM-C plain sleeve. CAD is installed/compressed state; free OD is +0.030 +/-0.005 mm above nominal, housing bore +0.000..+0.010. Finish running bore after installation. No clutch axial preload. Pull-out and thermal qualification required.
l_elev_bush_43 | clavicle_l.protract_frame | 加工塑料 | pom | 1 |  |  |  |  | 6.0 x 6.0 x 6.0 | POM-C / 未填充 PEEK / PA12 按材质分别加工；薄件不等同 PLA 打印 | parts/l_elev_bush_43.step |  | Machined POM-C plain sleeve. CAD is installed/compressed state; free OD is +0.030 +/-0.005 mm above nominal, housing bore +0.000..+0.010. Finish running bore after installation. No clutch axial preload. Pull-out and thermal qualification required.
l_yaw_carriage | clavicle_l.protract_frame | 加工金属 | aluminum_7075 | 1 |  |  |  |  | 25.0 x 28.367 x 68.05 | 按 STEP 加工并检验配合；复杂框架先反馈 DFM | parts/l_yaw_carriage.step |  | Machined yaw carriage, keyed D4 end and two original elevation bearings; bolt-on G4 reaction plate support; reamed press-fit sleeve seat, see retained_bushes manifest; reamed press-fit sleeve seat, see retained_bushes manifest
l_flex_bush_-36.5 | clavicle_l | 加工塑料 | pom | 1 |  |  |  |  | 5.0 x 8.0 x 8.0 | POM-C / 未填充 PEEK / PA12 按材质分别加工；薄件不等同 PLA 打印 | parts/l_flex_bush_-36.5.step |  | Machined POM-C plain sleeve. CAD is installed/compressed state; free OD is +0.030 +/-0.005 mm above nominal, housing bore +0.000..+0.010. Finish running bore after installation. No clutch axial preload. Pull-out and thermal qualification required.
l_flex_bush_-27.5 | clavicle_l | 加工塑料 | pom | 1 |  |  |  |  | 5.0 x 8.0 x 8.0 | POM-C / 未填充 PEEK / PA12 按材质分别加工；薄件不等同 PLA 打印 | parts/l_flex_bush_-27.5.step |  | Machined POM-C plain sleeve. CAD is installed/compressed state; free OD is +0.030 +/-0.005 mm above nominal, housing bore +0.000..+0.010. Finish running bore after installation. No clutch axial preload. Pull-out and thermal qualification required.
l_clavicle_output_frame | clavicle_l | 加工金属 | aluminum_7075 | 1 |  |  |  |  | 41.5 x 62.587 x 69.41 | 按 STEP 加工并检验配合；复杂框架先反馈 DFM | parts/l_clavicle_output_frame.step |  | Machined clavicle link, D4 middle key transfers elevation torque, M2 radial retainer; original shoulder centre preserved; reamed press-fit sleeve seat, see retained_bushes manifest; reamed press-fit sleeve seat, see retained_bushes manifest
l_abduct_bush_-20.5 | upperarm_l.flex_frame | 加工塑料 | pom | 1 |  |  |  |  | 5.0 x 6.0 x 6.0 | POM-C / 未填充 PEEK / PA12 按材质分别加工；薄件不等同 PLA 打印 | parts/l_abduct_bush_-20.5.step |  | Machined POM-C plain sleeve. CAD is installed/compressed state; free OD is +0.030 +/-0.005 mm above nominal, housing bore +0.000..+0.010. Finish running bore after installation. No clutch axial preload. Pull-out and thermal qualification required.
l_abduct_bush_20.5 | upperarm_l.flex_frame | 加工塑料 | pom | 1 |  |  |  |  | 5.0 x 8.0 x 8.0 | POM-C / 未填充 PEEK / PA12 按材质分别加工；薄件不等同 PLA 打印 | parts/l_abduct_bush_20.5.step |  | Machined POM-C plain sleeve. CAD is installed/compressed state; free OD is +0.030 +/-0.005 mm above nominal, housing bore +0.000..+0.010. Finish running bore after installation. No clutch axial preload. Pull-out and thermal qualification required.
l_flex_ring | upperarm_l.flex_frame | 加工金属 | aluminum_7075 | 1 |  |  |  |  | 32.0 x 42.0 x 77.895 | 按 STEP 加工并检验配合；复杂框架先反馈 DFM | parts/l_flex_ring.step |  | Rev J removable split metal drive hub; flange fixed with two M2 screws, nut pockets and tool relief; strain/creep not verified; 7075-T6 metal candidate required for reamed interference-fit radial bush seats; no PLA press-fit claim; reamed press-fit sleeve seat, see retained_bushes manifest; reamed press-fit sleeve seat, see retained_bushes manifest
l_abduct_ring_and_twist_seat | upperarm_l.abduct_frame | 加工金属 | aluminum_7075 | 1 |  |  |  |  | 20.645 x 28.0 x 31.0 | 按 STEP 加工并检验配合；复杂框架先反馈 DFM | parts/l_abduct_ring_and_twist_seat.step |  | Machined metal shoulder abduction ring and twist reaction face; top thrust face Z5.5, radial bush does not carry preload; integral positive travel stops; D6.04 nominal sleeve seat and captured D7.4 lower flange; outer friction contact radius increased to 10 mm
l_twist_bush | upperarm_l.abduct_frame | 加工塑料 | pom | 1 |  |  |  |  | 7.4 x 7.4 x 13.8 | POM-C / 未填充 PEEK / PA12 按材质分别加工；薄件不等同 PLA 打印 | parts/l_twist_bush.step |  | Flanged POM-C D6 sleeve, D4.06 running bore; D7.4 x0.8 flange trapped between lining top -9 and housing shoulder -8. Nominal axial float .2 mm.
l_twist_rotor_face | upperarm_l | 加工金属 | aluminum_7075 | 1 |  |  |  |  | 2.8 x 20.0 x 20.0 | 按 STEP 加工并检验配合；复杂框架先反馈 DFM | parts/l_twist_rotor_face.step |  | Positive D4 drive; axial spring force reacts into the fixed metal shoulder seat; integral travel tab reacts directly into bearing frame; outer friction contact radius increased to 10 mm
l_twist_lining | upperarm_l.abduct_frame | 加工塑料 | peek | 1 |  |  |  |  | 1.0 x 20.0 x 20.0 | POM-C / 未填充 PEEK / PA12 按材质分别加工；薄件不等同 PLA 打印 | parts/l_twist_lining.step |  | ; unfilled PEEK ring R3.15..10, dry contact candidate
l_arm_upperarm_shell_front | upperarm_l | 打印 | shell | 1 |  |  |  |  | 31.857 x 62.724 x 63.005 | PLA 候选，按随件 STL 和切片复核要求 | parts/l_arm_upperarm_shell_front.step | print_candidates/l_arm_upperarm_shell_front.stl | 1.8 mm partial rigid arm cover; two M2x20 through captive rear nuts into closed centreline rail lugs; front straight hex access, remove before servicing joints; pose clearance sampled digitally
l_arm_upperarm_shell_back | upperarm_l | 打印 | shell | 1 |  |  |  |  | 39.431 x 63.372 x 73.533 | PLA 候选，按随件 STL 和切片复核要求 | parts/l_arm_upperarm_shell_back.step | print_candidates/l_arm_upperarm_shell_back.stl | 1.8 mm partial rigid arm cover; two M2x20 through captive rear nuts into closed centreline rail lugs; front straight hex access, remove before servicing joints; pose clearance sampled digitally
r_yaw_bush_top | chest | 加工塑料 | pom | 1 |  |  |  |  | 6.0 x 6.0 x 10.0 | POM-C / 未填充 PEEK / PA12 按材质分别加工；薄件不等同 PLA 打印 | parts/r_yaw_bush_top.step |  | Machined POM-C plain sleeve. CAD is installed/compressed state; free OD is +0.030 +/-0.005 mm above nominal, housing bore +0.000..+0.010. Finish running bore after installation. No clutch axial preload. Pull-out and thermal qualification required.
r_yaw_bush_lower | chest | 加工塑料 | pom | 1 |  |  |  |  | 6.0 x 6.0 x 8.0 | POM-C / 未填充 PEEK / PA12 按材质分别加工；薄件不等同 PLA 打印 | parts/r_yaw_bush_lower.step |  | Machined POM-C plain sleeve. CAD is installed/compressed state; free OD is +0.030 +/-0.005 mm above nominal, housing bore +0.000..+0.010. Finish running bore after installation. No clutch axial preload. Pull-out and thermal qualification required.
r_elev_bush_27 | clavicle_r.protract_frame | 加工塑料 | pom | 1 |  |  |  |  | 6.0 x 6.0 x 6.0 | POM-C / 未填充 PEEK / PA12 按材质分别加工；薄件不等同 PLA 打印 | parts/r_elev_bush_27.step |  | Machined POM-C plain sleeve. CAD is installed/compressed state; free OD is +0.030 +/-0.005 mm above nominal, housing bore +0.000..+0.010. Finish running bore after installation. No clutch axial preload. Pull-out and thermal qualification required.
r_elev_bush_43 | clavicle_r.protract_frame | 加工塑料 | pom | 1 |  |  |  |  | 6.0 x 6.0 x 6.0 | POM-C / 未填充 PEEK / PA12 按材质分别加工；薄件不等同 PLA 打印 | parts/r_elev_bush_43.step |  | Machined POM-C plain sleeve. CAD is installed/compressed state; free OD is +0.030 +/-0.005 mm above nominal, housing bore +0.000..+0.010. Finish running bore after installation. No clutch axial preload. Pull-out and thermal qualification required.
r_yaw_carriage | clavicle_r.protract_frame | 加工金属 | aluminum_7075 | 1 |  |  |  |  | 25.0 x 28.367 x 68.05 | 按 STEP 加工并检验配合；复杂框架先反馈 DFM | parts/r_yaw_carriage.step |  | Machined yaw carriage, keyed D4 end and two original elevation bearings; bolt-on G4 reaction plate support; reamed press-fit sleeve seat, see retained_bushes manifest; reamed press-fit sleeve seat, see retained_bushes manifest
r_flex_bush_-36.5 | clavicle_r | 加工塑料 | pom | 1 |  |  |  |  | 5.0 x 8.0 x 8.0 | POM-C / 未填充 PEEK / PA12 按材质分别加工；薄件不等同 PLA 打印 | parts/r_flex_bush_-36.5.step |  | Machined POM-C plain sleeve. CAD is installed/compressed state; free OD is +0.030 +/-0.005 mm above nominal, housing bore +0.000..+0.010. Finish running bore after installation. No clutch axial preload. Pull-out and thermal qualification required.
r_flex_bush_-27.5 | clavicle_r | 加工塑料 | pom | 1 |  |  |  |  | 5.0 x 8.0 x 8.0 | POM-C / 未填充 PEEK / PA12 按材质分别加工；薄件不等同 PLA 打印 | parts/r_flex_bush_-27.5.step |  | Machined POM-C plain sleeve. CAD is installed/compressed state; free OD is +0.030 +/-0.005 mm above nominal, housing bore +0.000..+0.010. Finish running bore after installation. No clutch axial preload. Pull-out and thermal qualification required.
r_clavicle_output_frame | clavicle_r | 加工金属 | aluminum_7075 | 1 |  |  |  |  | 41.5 x 54.413 x 69.41 | 按 STEP 加工并检验配合；复杂框架先反馈 DFM | parts/r_clavicle_output_frame.step |  | Machined clavicle link, D4 middle key transfers elevation torque, M2 radial retainer; original shoulder centre preserved; reamed press-fit sleeve seat, see retained_bushes manifest; reamed press-fit sleeve seat, see retained_bushes manifest
r_abduct_bush_-20.5 | upperarm_r.flex_frame | 加工塑料 | pom | 1 |  |  |  |  | 5.0 x 6.0 x 6.0 | POM-C / 未填充 PEEK / PA12 按材质分别加工；薄件不等同 PLA 打印 | parts/r_abduct_bush_-20.5.step |  | Machined POM-C plain sleeve. CAD is installed/compressed state; free OD is +0.030 +/-0.005 mm above nominal, housing bore +0.000..+0.010. Finish running bore after installation. No clutch axial preload. Pull-out and thermal qualification required.
r_abduct_bush_20.5 | upperarm_r.flex_frame | 加工塑料 | pom | 1 |  |  |  |  | 5.0 x 8.0 x 8.0 | POM-C / 未填充 PEEK / PA12 按材质分别加工；薄件不等同 PLA 打印 | parts/r_abduct_bush_20.5.step |  | Machined POM-C plain sleeve. CAD is installed/compressed state; free OD is +0.030 +/-0.005 mm above nominal, housing bore +0.000..+0.010. Finish running bore after installation. No clutch axial preload. Pull-out and thermal qualification required.
r_flex_ring | upperarm_r.flex_frame | 加工金属 | aluminum_7075 | 1 |  |  |  |  | 32.0 x 42.0 x 77.895 | 按 STEP 加工并检验配合；复杂框架先反馈 DFM | parts/r_flex_ring.step |  | Rev J removable split metal drive hub; flange fixed with two M2 screws, nut pockets and tool relief; strain/creep not verified; 7075-T6 metal candidate required for reamed interference-fit radial bush seats; no PLA press-fit claim; reamed press-fit sleeve seat, see retained_bushes manifest; reamed press-fit sleeve seat, see retained_bushes manifest
r_abduct_ring_and_twist_seat | upperarm_r.abduct_frame | 加工金属 | aluminum_7075 | 1 |  |  |  |  | 20.645 x 28.0 x 31.0 | 按 STEP 加工并检验配合；复杂框架先反馈 DFM | parts/r_abduct_ring_and_twist_seat.step |  | Machined metal shoulder abduction ring and twist reaction face; top thrust face Z5.5, radial bush does not carry preload; integral positive travel stops; D6.04 nominal sleeve seat and captured D7.4 lower flange; outer friction contact radius increased to 10 mm
r_twist_bush | upperarm_r.abduct_frame | 加工塑料 | pom | 1 |  |  |  |  | 7.4 x 7.4 x 13.8 | POM-C / 未填充 PEEK / PA12 按材质分别加工；薄件不等同 PLA 打印 | parts/r_twist_bush.step |  | Flanged POM-C D6 sleeve, D4.06 running bore; D7.4 x0.8 flange trapped between lining top -9 and housing shoulder -8. Nominal axial float .2 mm.
r_twist_rotor_face | upperarm_r | 加工金属 | aluminum_7075 | 1 |  |  |  |  | 2.8 x 20.0 x 20.0 | 按 STEP 加工并检验配合；复杂框架先反馈 DFM | parts/r_twist_rotor_face.step |  | Positive D4 drive; axial spring force reacts into the fixed metal shoulder seat; integral travel tab reacts directly into bearing frame; outer friction contact radius increased to 10 mm
r_twist_lining | upperarm_r.abduct_frame | 加工塑料 | peek | 1 |  |  |  |  | 1.0 x 20.0 x 20.0 | POM-C / 未填充 PEEK / PA12 按材质分别加工；薄件不等同 PLA 打印 | parts/r_twist_lining.step |  | ; unfilled PEEK ring R3.15..10, dry contact candidate
r_arm_upperarm_shell_front | upperarm_r | 打印 | shell | 1 |  |  |  |  | 31.857 x 62.724 x 63.005 | PLA 候选，按随件 STL 和切片复核要求 | parts/r_arm_upperarm_shell_front.step | print_candidates/r_arm_upperarm_shell_front.stl | 1.8 mm partial rigid arm cover; two M2x20 through captive rear nuts into closed centreline rail lugs; front straight hex access, remove before servicing joints; pose clearance sampled digitally
r_arm_upperarm_shell_back | upperarm_r | 打印 | shell | 1 |  |  |  |  | 39.431 x 63.372 x 73.533 | PLA 候选，按随件 STL 和切片复核要求 | parts/r_arm_upperarm_shell_back.step | print_candidates/r_arm_upperarm_shell_back.stl | 1.8 mm partial rigid arm cover; two M2x20 through captive rear nuts into closed centreline rail lugs; front straight hex access, remove before servicing joints; pose clearance sampled digitally
l_flex_clutch_flanged_shaft | upperarm_l.flex_frame | 加工金属 | aluminum_7075 | 1 |  |  |  |  | 27.0 x 27.0 x 33.376 | 按 STEP 加工并检验配合；复杂框架先反馈 DFM | parts/l_flex_clutch_flanged_shaft.step |  | Custom steel 6 mm journal; integral flange, inner D drive, outer D cap seat, two M3 blind threads; integral travel tab reacts directly into bearing frame
l_flex_clutch_keyed_lining | clavicle_l | 加工塑料 | peek | 1 |  |  |  |  | 1.0 x 25.0 x 27.2 | POM-C / 未填充 PEEK / PA12 按材质分别加工；薄件不等同 PLA 打印 | parts/l_flex_clutch_keyed_lining.step |  | 1 mm replaceable lining; coefficient and wear unqualified; inner radius 6.8 mm leaves a 0.3 mm radial clearance to protected inner travel tabs; unfilled machined PEEK candidate, dry contact; actual torque and creep must be qualified
l_flex_clutch_reaction_plate | clavicle_l | 加工金属 | aluminum_7075 | 1 |  |  |  |  | 4.0 x 27.4 x 42.0 | 按 STEP 加工并检验配合；复杂框架先反馈 DFM | parts/l_flex_clutch_reaction_plate.step |  | 3 mm steel reaction plate with keyed lining recess and two M3 frame mounts; spring thrust closes through plate; Rev L two M2 through pilot bores at +/-11.9 for separate brass sensor standoffs; 1.0 mm minimum radial ligament; integral positive travel stops; D14.50 x0.85 upper retaining counterbore, flat Z3.15
l_flex_clutch_radial_bush | clavicle_l | 加工塑料 | pom | 1 |  |  |  |  | 2.8 x 14.4 x 14.4 | POM-C / 未填充 PEEK / PA12 按材质分别加工；薄件不等同 PLA 打印 | parts/l_flex_clutch_radial_bush.step |  | POM radial guide, clear of thrust faces; press fit/retention pending; D14.40 x0.70 flange at Z3.20..3.90, captured below thrust washer Z4.00; 0.15 total nominal axial float
l_flex_clutch_thrust_washer | clavicle_l | 采购标准件 | thrust | 1 | PCMW 102001.5 E |  |  |  | 1.5 x 20.0 x 20.0 | SKF PCMW 102001.5 E；以当前 STEP 尺寸核对 | parts/l_flex_clutch_thrust_washer.step |  | SKF dimension candidate; PTFE face towards rotating spring seat; washer retention pending
l_flex_clutch_spring_seat | upperarm_l.flex_frame | 加工金属 | metal | 1 |  |  |  |  | 0.5 x 20.0 x 20.0 | 按 STEP 加工并检验配合；复杂框架先反馈 DFM | parts/l_flex_clutch_spring_seat.step |  | Steel spring seat; thrust washer separates rotation from fixed reaction plate
l_flex_clutch_disc_spring_a | upperarm_l.flex_frame | 采购碟簧 | spring | 1 | SCHNORR 002200 |  |  |  | 0.688 x 12.0 x 12.0 | 按弹簧型号和装配方向，不按 CAD 色彩选型 | parts/l_flex_clutch_disc_spring_a.step |  | SCHNORR 002 200 dimensional candidate at catalog test height
l_flex_clutch_disc_spring_b | upperarm_l.flex_frame | 采购碟簧 | spring | 1 | SCHNORR 002200 |  |  |  | 0.688 x 12.0 x 12.0 | 按弹簧型号和装配方向，不按 CAD 色彩选型 | parts/l_flex_clutch_disc_spring_b.step |  | Opposed pair in series: force is not doubled
l_flex_clutch_keyed_stop_cap | upperarm_l.flex_frame | 加工金属 | aluminum | 1 |  |  |  |  | 3.0 x 12.8 x 14.0 | 按 STEP 加工并检验配合；复杂框架先反馈 DFM | parts/l_flex_clutch_keyed_stop_cap.step |  | Rev L aluminum stop cap retains original metal stop heights and adds outside D flat for magnet cup; local contact stress and fatigue unqualified
l_flex_clutch_outer_M3x8 | upperarm_l.flex_frame | 采购紧固件 | titanium | 1 | SSB-M3-8-TI5 | M3 | 8 | button_head | 5.7 x 5.7 x 9.65 | 按螺纹、长度、材料和实际头部包络一起核对 | parts/l_flex_clutch_outer_M3x8.step |  | Rev L M3x8 titanium Grade 5 button screw dimension candidate (Accu SSB-M3-8-TI5); cylindrical head envelope 5.7 x 1.65, 2 mm hex, strength/procurement not released
l_flex_clutch_drive_retainer_washer | upperarm_l.flex_frame | 加工金属 | metal | 1 |  |  |  |  | 1.0 x 10.0 x 10.0 | 按 STEP 加工并检验配合；复杂框架先反馈 DFM | parts/l_flex_clutch_drive_retainer_washer.step |  | Separate washer retains D drive in printed output hub
l_flex_clutch_inner_M3x8 | upperarm_l.flex_frame | 采购紧固件 | fastener | 1 |  | M3 | 8 | button_head | 5.7 x 5.7 x 9.65 | 按螺纹、长度、材料和实际头部包络一起核对 | parts/l_flex_clutch_inner_M3x8.step |  | M3x8 ISO7380-1 low-profile button screw, 1.65 mm nominal head height; independent output-hub retention, no spring adjustment
l_flex_clutch_mount_M3x10_0 | clavicle_l | 采购紧固件 | fastener | 1 |  | M3 | 10 | screw_head_to_drawing | 5.5 x 5.5 x 13.0 | 按螺纹、长度、材料和实际头部包络一起核对 | parts/l_flex_clutch_mount_M3x10_0.step |  | Reaction plate to printed support; simplified thread
l_flex_clutch_mount_M3_nut_0 | clavicle_l | 采购紧固件 | fastener | 1 |  | M3 |  | hex_nut | 2.4 x 5.5 x 6.351 | 按螺纹、长度、材料和实际头部包络一起核对 | parts/l_flex_clutch_mount_M3_nut_0.step |  | Captured hex nut, accessible from inside of support
l_flex_clutch_mount_M3x10_1 | clavicle_l | 采购紧固件 | fastener | 1 |  | M3 | 10 | screw_head_to_drawing | 5.5 x 5.5 x 13.0 | 按螺纹、长度、材料和实际头部包络一起核对 | parts/l_flex_clutch_mount_M3x10_1.step |  | Reaction plate to printed support; simplified thread
l_flex_clutch_mount_M3_nut_1 | clavicle_l | 采购紧固件 | fastener | 1 |  | M3 |  | hex_nut | 2.4 x 5.5 x 6.351 | 按螺纹、长度、材料和实际头部包络一起核对 | parts/l_flex_clutch_mount_M3_nut_1.step |  | Captured hex nut, accessible from inside of support
l_abduct_clutch_flanged_shaft | upperarm_l.abduct_frame | 加工金属 | aluminum_7075 | 1 |  |  |  |  | 25.376 x 27.0 x 27.0 | 按 STEP 加工并检验配合；复杂框架先反馈 DFM | parts/l_abduct_clutch_flanged_shaft.step |  | Custom steel 6 mm journal; integral flange, inner D drive, outer D cap seat, two M3 blind threads; integral travel tab reacts directly into bearing frame
l_abduct_clutch_keyed_lining | upperarm_l.flex_frame | 加工塑料 | peek | 1 |  |  |  |  | 1.0 x 25.0 x 27.2 | POM-C / 未填充 PEEK / PA12 按材质分别加工；薄件不等同 PLA 打印 | parts/l_abduct_clutch_keyed_lining.step |  | 1 mm replaceable lining; coefficient and wear unqualified; inner radius 6.8 mm leaves a 0.3 mm radial clearance to protected inner travel tabs; unfilled machined PEEK candidate, dry contact; actual torque and creep must be qualified
l_abduct_clutch_reaction_plate | upperarm_l.flex_frame | 加工金属 | aluminum_7075 | 1 |  |  |  |  | 4.0 x 27.4 x 42.0 | 按 STEP 加工并检验配合；复杂框架先反馈 DFM | parts/l_abduct_clutch_reaction_plate.step |  | 3 mm steel reaction plate with keyed lining recess and two M3 frame mounts; spring thrust closes through plate; integral positive travel stops; D14.50 x0.85 upper retaining counterbore, flat Z3.15
l_abduct_clutch_radial_bush | upperarm_l.flex_frame | 加工塑料 | pom | 1 |  |  |  |  | 2.8 x 14.4 x 14.4 | POM-C / 未填充 PEEK / PA12 按材质分别加工；薄件不等同 PLA 打印 | parts/l_abduct_clutch_radial_bush.step |  | POM radial guide, clear of thrust faces; press fit/retention pending; D14.40 x0.70 flange at Z3.20..3.90, captured below thrust washer Z4.00; 0.15 total nominal axial float
l_abduct_clutch_thrust_washer | upperarm_l.flex_frame | 采购标准件 | thrust | 1 | PCMW 102001.5 E |  |  |  | 1.5 x 20.0 x 20.0 | SKF PCMW 102001.5 E；以当前 STEP 尺寸核对 | parts/l_abduct_clutch_thrust_washer.step |  | SKF dimension candidate; PTFE face towards rotating spring seat; washer retention pending
l_abduct_clutch_spring_seat | upperarm_l.abduct_frame | 加工金属 | metal | 1 |  |  |  |  | 0.5 x 20.0 x 20.0 | 按 STEP 加工并检验配合；复杂框架先反馈 DFM | parts/l_abduct_clutch_spring_seat.step |  | Steel spring seat; thrust washer separates rotation from fixed reaction plate
l_abduct_clutch_disc_spring_a | upperarm_l.abduct_frame | 采购碟簧 | spring | 1 | SCHNORR 002200 |  |  |  | 0.688 x 12.0 x 12.0 | 按弹簧型号和装配方向，不按 CAD 色彩选型 | parts/l_abduct_clutch_disc_spring_a.step |  | SCHNORR 002 200 dimensional candidate at catalog test height
l_abduct_clutch_disc_spring_b | upperarm_l.abduct_frame | 采购碟簧 | spring | 1 | SCHNORR 002200 |  |  |  | 0.688 x 12.0 x 12.0 | 按弹簧型号和装配方向，不按 CAD 色彩选型 | parts/l_abduct_clutch_disc_spring_b.step |  | Opposed pair in series: force is not doubled
l_abduct_clutch_keyed_stop_cap | upperarm_l.abduct_frame | 加工金属 | metal | 1 |  |  |  |  | 3.0 x 14.0 x 14.0 | 按 STEP 加工并检验配合；复杂框架先反馈 DFM | parts/l_abduct_clutch_keyed_stop_cap.step |  | D key follows shaft; cap seats on metal shaft end; shim selection/retention and backlash need physical validation
l_abduct_clutch_outer_M3x8 | upperarm_l.abduct_frame | 采购紧固件 | fastener | 1 |  | M3 | 8 | screw_head_to_drawing | 5.5 x 5.5 x 11.0 | 按螺纹、长度、材料和实际头部包络一起核对 | parts/l_abduct_clutch_outer_M3x8.step |  | Simplified thread envelope; axial cap retention, not hand tightness setting
l_abduct_clutch_drive_retainer_washer | upperarm_l.abduct_frame | 加工金属 | metal | 1 |  |  |  |  | 1.0 x 10.0 x 10.0 | 按 STEP 加工并检验配合；复杂框架先反馈 DFM | parts/l_abduct_clutch_drive_retainer_washer.step |  | Separate washer retains D drive in printed output hub
l_abduct_clutch_inner_M3x8 | upperarm_l.abduct_frame | 采购紧固件 | fastener | 1 |  | M3 | 8 | screw_head_to_drawing | 5.5 x 5.5 x 11.0 | 按螺纹、长度、材料和实际头部包络一起核对 | parts/l_abduct_clutch_inner_M3x8.step |  | Independent output-hub retention; does not set clutch spring compression
l_abduct_clutch_mount_M3x10_0 | upperarm_l.flex_frame | 采购紧固件 | fastener | 1 |  | M3 | 10 | screw_head_to_drawing | 5.5 x 5.5 x 13.0 | 按螺纹、长度、材料和实际头部包络一起核对 | parts/l_abduct_clutch_mount_M3x10_0.step |  | Reaction plate to printed support; simplified thread
l_abduct_clutch_mount_M3_nut_0 | upperarm_l.flex_frame | 采购紧固件 | fastener | 1 |  | M3 |  | hex_nut | 2.4 x 5.5 x 6.351 | 按螺纹、长度、材料和实际头部包络一起核对 | parts/l_abduct_clutch_mount_M3_nut_0.step |  | Captured hex nut, accessible from inside of support
l_abduct_clutch_mount_M3x10_1 | upperarm_l.flex_frame | 采购紧固件 | fastener | 1 |  | M3 | 10 | screw_head_to_drawing | 5.5 x 5.5 x 13.0 | 按螺纹、长度、材料和实际头部包络一起核对 | parts/l_abduct_clutch_mount_M3x10_1.step |  | Reaction plate to printed support; simplified thread
l_abduct_clutch_mount_M3_nut_1 | upperarm_l.flex_frame | 采购紧固件 | fastener | 1 |  | M3 |  | hex_nut | 2.4 x 5.5 x 6.351 | 按螺纹、长度、材料和实际头部包络一起核对 | parts/l_abduct_clutch_mount_M3_nut_1.step |  | Captured hex nut, accessible from inside of support
r_flex_clutch_flanged_shaft | upperarm_r.flex_frame | 加工金属 | aluminum_7075 | 1 |  |  |  |  | 27.0 x 27.0 x 33.376 | 按 STEP 加工并检验配合；复杂框架先反馈 DFM | parts/r_flex_clutch_flanged_shaft.step |  | Custom steel 6 mm journal; integral flange, inner D drive, outer D cap seat, two M3 blind threads; integral travel tab reacts directly into bearing frame
r_flex_clutch_keyed_lining | clavicle_r | 加工塑料 | peek | 1 |  |  |  |  | 1.0 x 25.0 x 27.2 | POM-C / 未填充 PEEK / PA12 按材质分别加工；薄件不等同 PLA 打印 | parts/r_flex_clutch_keyed_lining.step |  | 1 mm replaceable lining; coefficient and wear unqualified; inner radius 6.8 mm leaves a 0.3 mm radial clearance to protected inner travel tabs; unfilled machined PEEK candidate, dry contact; actual torque and creep must be qualified
r_flex_clutch_reaction_plate | clavicle_r | 加工金属 | aluminum_7075 | 1 |  |  |  |  | 4.0 x 27.4 x 42.0 | 按 STEP 加工并检验配合；复杂框架先反馈 DFM | parts/r_flex_clutch_reaction_plate.step |  | 3 mm steel reaction plate with keyed lining recess and two M3 frame mounts; spring thrust closes through plate; Rev L two M2 through pilot bores at +/-11.9 for separate brass sensor standoffs; 1.0 mm minimum radial ligament; integral positive travel stops; D14.50 x0.85 upper retaining counterbore, flat Z3.15
r_flex_clutch_radial_bush | clavicle_r | 加工塑料 | pom | 1 |  |  |  |  | 2.8 x 14.4 x 14.4 | POM-C / 未填充 PEEK / PA12 按材质分别加工；薄件不等同 PLA 打印 | parts/r_flex_clutch_radial_bush.step |  | POM radial guide, clear of thrust faces; press fit/retention pending; D14.40 x0.70 flange at Z3.20..3.90, captured below thrust washer Z4.00; 0.15 total nominal axial float
r_flex_clutch_thrust_washer | clavicle_r | 采购标准件 | thrust | 1 | PCMW 102001.5 E |  |  |  | 1.5 x 20.0 x 20.0 | SKF PCMW 102001.5 E；以当前 STEP 尺寸核对 | parts/r_flex_clutch_thrust_washer.step |  | SKF dimension candidate; PTFE face towards rotating spring seat; washer retention pending
r_flex_clutch_spring_seat | upperarm_r.flex_frame | 加工金属 | metal | 1 |  |  |  |  | 0.5 x 20.0 x 20.0 | 按 STEP 加工并检验配合；复杂框架先反馈 DFM | parts/r_flex_clutch_spring_seat.step |  | Steel spring seat; thrust washer separates rotation from fixed reaction plate
r_flex_clutch_disc_spring_a | upperarm_r.flex_frame | 采购碟簧 | spring | 1 | SCHNORR 002200 |  |  |  | 0.688 x 12.0 x 12.0 | 按弹簧型号和装配方向，不按 CAD 色彩选型 | parts/r_flex_clutch_disc_spring_a.step |  | SCHNORR 002 200 dimensional candidate at catalog test height
r_flex_clutch_disc_spring_b | upperarm_r.flex_frame | 采购碟簧 | spring | 1 | SCHNORR 002200 |  |  |  | 0.688 x 12.0 x 12.0 | 按弹簧型号和装配方向，不按 CAD 色彩选型 | parts/r_flex_clutch_disc_spring_b.step |  | Opposed pair in series: force is not doubled
r_flex_clutch_keyed_stop_cap | upperarm_r.flex_frame | 加工金属 | aluminum | 1 |  |  |  |  | 3.0 x 12.8 x 14.0 | 按 STEP 加工并检验配合；复杂框架先反馈 DFM | parts/r_flex_clutch_keyed_stop_cap.step |  | Rev L aluminum stop cap retains original metal stop heights and adds outside D flat for magnet cup; local contact stress and fatigue unqualified
r_flex_clutch_outer_M3x8 | upperarm_r.flex_frame | 采购紧固件 | titanium | 1 | SSB-M3-8-TI5 | M3 | 8 | button_head | 5.7 x 5.7 x 9.65 | 按螺纹、长度、材料和实际头部包络一起核对 | parts/r_flex_clutch_outer_M3x8.step |  | Rev L M3x8 titanium Grade 5 button screw dimension candidate (Accu SSB-M3-8-TI5); cylindrical head envelope 5.7 x 1.65, 2 mm hex, strength/procurement not released
r_flex_clutch_drive_retainer_washer | upperarm_r.flex_frame | 加工金属 | metal | 1 |  |  |  |  | 1.0 x 10.0 x 10.0 | 按 STEP 加工并检验配合；复杂框架先反馈 DFM | parts/r_flex_clutch_drive_retainer_washer.step |  | Separate washer retains D drive in printed output hub
r_flex_clutch_inner_M3x8 | upperarm_r.flex_frame | 采购紧固件 | fastener | 1 |  | M3 | 8 | button_head | 5.7 x 5.7 x 9.65 | 按螺纹、长度、材料和实际头部包络一起核对 | parts/r_flex_clutch_inner_M3x8.step |  | M3x8 ISO7380-1 low-profile button screw, 1.65 mm nominal head height; independent output-hub retention, no spring adjustment
r_flex_clutch_mount_M3x10_0 | clavicle_r | 采购紧固件 | fastener | 1 |  | M3 | 10 | screw_head_to_drawing | 5.5 x 5.5 x 13.0 | 按螺纹、长度、材料和实际头部包络一起核对 | parts/r_flex_clutch_mount_M3x10_0.step |  | Reaction plate to printed support; simplified thread
r_flex_clutch_mount_M3_nut_0 | clavicle_r | 采购紧固件 | fastener | 1 |  | M3 |  | hex_nut | 2.4 x 5.5 x 6.351 | 按螺纹、长度、材料和实际头部包络一起核对 | parts/r_flex_clutch_mount_M3_nut_0.step |  | Captured hex nut, accessible from inside of support
r_flex_clutch_mount_M3x10_1 | clavicle_r | 采购紧固件 | fastener | 1 |  | M3 | 10 | screw_head_to_drawing | 5.5 x 5.5 x 13.0 | 按螺纹、长度、材料和实际头部包络一起核对 | parts/r_flex_clutch_mount_M3x10_1.step |  | Reaction plate to printed support; simplified thread
r_flex_clutch_mount_M3_nut_1 | clavicle_r | 采购紧固件 | fastener | 1 |  | M3 |  | hex_nut | 2.4 x 5.5 x 6.351 | 按螺纹、长度、材料和实际头部包络一起核对 | parts/r_flex_clutch_mount_M3_nut_1.step |  | Captured hex nut, accessible from inside of support
r_abduct_clutch_flanged_shaft | upperarm_r.abduct_frame | 加工金属 | aluminum_7075 | 1 |  |  |  |  | 25.376 x 27.0 x 27.0 | 按 STEP 加工并检验配合；复杂框架先反馈 DFM | parts/r_abduct_clutch_flanged_shaft.step |  | Custom steel 6 mm journal; integral flange, inner D drive, outer D cap seat, two M3 blind threads; integral travel tab reacts directly into bearing frame
r_abduct_clutch_keyed_lining | upperarm_r.flex_frame | 加工塑料 | peek | 1 |  |  |  |  | 1.0 x 25.0 x 27.2 | POM-C / 未填充 PEEK / PA12 按材质分别加工；薄件不等同 PLA 打印 | parts/r_abduct_clutch_keyed_lining.step |  | 1 mm replaceable lining; coefficient and wear unqualified; inner radius 6.8 mm leaves a 0.3 mm radial clearance to protected inner travel tabs; unfilled machined PEEK candidate, dry contact; actual torque and creep must be qualified
r_abduct_clutch_reaction_plate | upperarm_r.flex_frame | 加工金属 | aluminum_7075 | 1 |  |  |  |  | 4.0 x 27.4 x 42.0 | 按 STEP 加工并检验配合；复杂框架先反馈 DFM | parts/r_abduct_clutch_reaction_plate.step |  | 3 mm steel reaction plate with keyed lining recess and two M3 frame mounts; spring thrust closes through plate; integral positive travel stops; D14.50 x0.85 upper retaining counterbore, flat Z3.15
r_abduct_clutch_radial_bush | upperarm_r.flex_frame | 加工塑料 | pom | 1 |  |  |  |  | 2.8 x 14.4 x 14.4 | POM-C / 未填充 PEEK / PA12 按材质分别加工；薄件不等同 PLA 打印 | parts/r_abduct_clutch_radial_bush.step |  | POM radial guide, clear of thrust faces; press fit/retention pending; D14.40 x0.70 flange at Z3.20..3.90, captured below thrust washer Z4.00; 0.15 total nominal axial float
r_abduct_clutch_thrust_washer | upperarm_r.flex_frame | 采购标准件 | thrust | 1 | PCMW 102001.5 E |  |  |  | 1.5 x 20.0 x 20.0 | SKF PCMW 102001.5 E；以当前 STEP 尺寸核对 | parts/r_abduct_clutch_thrust_washer.step |  | SKF dimension candidate; PTFE face towards rotating spring seat; washer retention pending
r_abduct_clutch_spring_seat | upperarm_r.abduct_frame | 加工金属 | metal | 1 |  |  |  |  | 0.5 x 20.0 x 20.0 | 按 STEP 加工并检验配合；复杂框架先反馈 DFM | parts/r_abduct_clutch_spring_seat.step |  | Steel spring seat; thrust washer separates rotation from fixed reaction plate
r_abduct_clutch_disc_spring_a | upperarm_r.abduct_frame | 采购碟簧 | spring | 1 | SCHNORR 002200 |  |  |  | 0.688 x 12.0 x 12.0 | 按弹簧型号和装配方向，不按 CAD 色彩选型 | parts/r_abduct_clutch_disc_spring_a.step |  | SCHNORR 002 200 dimensional candidate at catalog test height
r_abduct_clutch_disc_spring_b | upperarm_r.abduct_frame | 采购碟簧 | spring | 1 | SCHNORR 002200 |  |  |  | 0.688 x 12.0 x 12.0 | 按弹簧型号和装配方向，不按 CAD 色彩选型 | parts/r_abduct_clutch_disc_spring_b.step |  | Opposed pair in series: force is not doubled
r_abduct_clutch_keyed_stop_cap | upperarm_r.abduct_frame | 加工金属 | metal | 1 |  |  |  |  | 3.0 x 14.0 x 14.0 | 按 STEP 加工并检验配合；复杂框架先反馈 DFM | parts/r_abduct_clutch_keyed_stop_cap.step |  | D key follows shaft; cap seats on metal shaft end; shim selection/retention and backlash need physical validation
r_abduct_clutch_outer_M3x8 | upperarm_r.abduct_frame | 采购紧固件 | fastener | 1 |  | M3 | 8 | screw_head_to_drawing | 5.5 x 5.5 x 11.0 | 按螺纹、长度、材料和实际头部包络一起核对 | parts/r_abduct_clutch_outer_M3x8.step |  | Simplified thread envelope; axial cap retention, not hand tightness setting
r_abduct_clutch_drive_retainer_washer | upperarm_r.abduct_frame | 加工金属 | metal | 1 |  |  |  |  | 1.0 x 10.0 x 10.0 | 按 STEP 加工并检验配合；复杂框架先反馈 DFM | parts/r_abduct_clutch_drive_retainer_washer.step |  | Separate washer retains D drive in printed output hub
r_abduct_clutch_inner_M3x8 | upperarm_r.abduct_frame | 采购紧固件 | fastener | 1 |  | M3 | 8 | screw_head_to_drawing | 5.5 x 5.5 x 11.0 | 按螺纹、长度、材料和实际头部包络一起核对 | parts/r_abduct_clutch_inner_M3x8.step |  | Independent output-hub retention; does not set clutch spring compression
r_abduct_clutch_mount_M3x10_0 | upperarm_r.flex_frame | 采购紧固件 | fastener | 1 |  | M3 | 10 | screw_head_to_drawing | 5.5 x 5.5 x 13.0 | 按螺纹、长度、材料和实际头部包络一起核对 | parts/r_abduct_clutch_mount_M3x10_0.step |  | Reaction plate to printed support; simplified thread
r_abduct_clutch_mount_M3_nut_0 | upperarm_r.flex_frame | 采购紧固件 | fastener | 1 |  | M3 |  | hex_nut | 2.4 x 5.5 x 6.351 | 按螺纹、长度、材料和实际头部包络一起核对 | parts/r_abduct_clutch_mount_M3_nut_0.step |  | Captured hex nut, accessible from inside of support
r_abduct_clutch_mount_M3x10_1 | upperarm_r.flex_frame | 采购紧固件 | fastener | 1 |  | M3 | 10 | screw_head_to_drawing | 5.5 x 5.5 x 13.0 | 按螺纹、长度、材料和实际头部包络一起核对 | parts/r_abduct_clutch_mount_M3x10_1.step |  | Reaction plate to printed support; simplified thread
r_abduct_clutch_mount_M3_nut_1 | upperarm_r.flex_frame | 采购紧固件 | fastener | 1 |  | M3 |  | hex_nut | 2.4 x 5.5 x 6.351 | 按螺纹、长度、材料和实际头部包络一起核对 | parts/r_abduct_clutch_mount_M3_nut_1.step |  | Captured hex nut, accessible from inside of support
l_flex_drive_split_hub | upperarm_l.flex_frame | 加工金属 | aluminum | 1 |  |  |  |  | 5.5 x 16.2 x 17.0 | 按 STEP 加工并检验配合；复杂框架先反馈 DFM | parts/l_flex_drive_split_hub.step |  | Custom split metal D hub; M2 tapped clamp ear; preload/elastic closure not simulated
l_flex_drive_pinch_M2x10 | upperarm_l.flex_frame | 采购紧固件 | fastener | 1 |  | M2 | 10 | screw_head_to_drawing | 3.8 x 3.8 x 12.0 | 按螺纹、长度、材料和实际头部包络一起核对 | parts/l_flex_drive_pinch_M2x10.step |  | M2 transverse pinch screw takes up shaft fit clearance; tightening torque not yet qualified
l_flex_drive_mount_M2x4_0 | upperarm_l.flex_frame | 采购紧固件 | fastener | 1 |  | M2 | 4 | hex_nut | 3.8 x 3.8 x 6.0 | 按螺纹、长度、材料和实际头部包络一起核对 | parts/l_flex_drive_mount_M2x4_0.step |  | Flange screw with trapped M2 nut; 1.6 mm nominal nut engagement
l_flex_drive_mount_M2_nut_0 | upperarm_l.flex_frame | 采购紧固件 | fastener | 1 |  | M2 |  | hex_nut | 1.6 x 4.0 x 4.619 | 按螺纹、长度、材料和实际头部包络一起核对 | parts/l_flex_drive_mount_M2_nut_0.step |  | Captured nut inside output yoke; fit and creep require testing
l_flex_drive_mount_M2x4_1 | upperarm_l.flex_frame | 采购紧固件 | fastener | 1 |  | M2 | 4 | hex_nut | 3.8 x 3.8 x 6.0 | 按螺纹、长度、材料和实际头部包络一起核对 | parts/l_flex_drive_mount_M2x4_1.step |  | Flange screw with trapped M2 nut; 1.6 mm nominal nut engagement
l_flex_drive_mount_M2_nut_1 | upperarm_l.flex_frame | 采购紧固件 | fastener | 1 |  | M2 |  | hex_nut | 1.6 x 4.0 x 4.619 | 按螺纹、长度、材料和实际头部包络一起核对 | parts/l_flex_drive_mount_M2_nut_1.step |  | Captured nut inside output yoke; fit and creep require testing
l_abduct_drive_split_hub | upperarm_l.abduct_frame | 加工金属 | aluminum | 1 |  |  |  |  | 5.5 x 16.2 x 17.0 | 按 STEP 加工并检验配合；复杂框架先反馈 DFM | parts/l_abduct_drive_split_hub.step |  | Custom split metal D hub; M2 tapped clamp ear; preload/elastic closure not simulated
l_abduct_drive_pinch_M2x10 | upperarm_l.abduct_frame | 采购紧固件 | fastener | 1 |  | M2 | 10 | screw_head_to_drawing | 3.8 x 3.8 x 12.0 | 按螺纹、长度、材料和实际头部包络一起核对 | parts/l_abduct_drive_pinch_M2x10.step |  | M2 transverse pinch screw takes up shaft fit clearance; tightening torque not yet qualified
l_abduct_drive_mount_M2x4_0 | upperarm_l.abduct_frame | 采购紧固件 | fastener | 1 |  | M2 | 4 | hex_nut | 3.8 x 3.8 x 6.0 | 按螺纹、长度、材料和实际头部包络一起核对 | parts/l_abduct_drive_mount_M2x4_0.step |  | Flange screw with trapped M2 nut; 1.6 mm nominal nut engagement
l_abduct_drive_mount_M2_nut_0 | upperarm_l.abduct_frame | 采购紧固件 | fastener | 1 |  | M2 |  | hex_nut | 1.6 x 4.0 x 4.619 | 按螺纹、长度、材料和实际头部包络一起核对 | parts/l_abduct_drive_mount_M2_nut_0.step |  | Captured nut inside output yoke; fit and creep require testing
l_abduct_drive_mount_M2x4_1 | upperarm_l.abduct_frame | 采购紧固件 | fastener | 1 |  | M2 | 4 | hex_nut | 3.8 x 3.8 x 6.0 | 按螺纹、长度、材料和实际头部包络一起核对 | parts/l_abduct_drive_mount_M2x4_1.step |  | Flange screw with trapped M2 nut; 1.6 mm nominal nut engagement
l_abduct_drive_mount_M2_nut_1 | upperarm_l.abduct_frame | 采购紧固件 | fastener | 1 |  | M2 |  | hex_nut | 1.6 x 4.0 x 4.619 | 按螺纹、长度、材料和实际头部包络一起核对 | parts/l_abduct_drive_mount_M2_nut_1.step |  | Captured nut inside output yoke; fit and creep require testing
r_flex_drive_split_hub | upperarm_r.flex_frame | 加工金属 | aluminum | 1 |  |  |  |  | 5.5 x 16.2 x 17.0 | 按 STEP 加工并检验配合；复杂框架先反馈 DFM | parts/r_flex_drive_split_hub.step |  | Custom split metal D hub; M2 tapped clamp ear; preload/elastic closure not simulated
r_flex_drive_pinch_M2x10 | upperarm_r.flex_frame | 采购紧固件 | fastener | 1 |  | M2 | 10 | screw_head_to_drawing | 3.8 x 3.8 x 12.0 | 按螺纹、长度、材料和实际头部包络一起核对 | parts/r_flex_drive_pinch_M2x10.step |  | M2 transverse pinch screw takes up shaft fit clearance; tightening torque not yet qualified
r_flex_drive_mount_M2x4_0 | upperarm_r.flex_frame | 采购紧固件 | fastener | 1 |  | M2 | 4 | hex_nut | 3.8 x 3.8 x 6.0 | 按螺纹、长度、材料和实际头部包络一起核对 | parts/r_flex_drive_mount_M2x4_0.step |  | Flange screw with trapped M2 nut; 1.6 mm nominal nut engagement
r_flex_drive_mount_M2_nut_0 | upperarm_r.flex_frame | 采购紧固件 | fastener | 1 |  | M2 |  | hex_nut | 1.6 x 4.0 x 4.619 | 按螺纹、长度、材料和实际头部包络一起核对 | parts/r_flex_drive_mount_M2_nut_0.step |  | Captured nut inside output yoke; fit and creep require testing
r_flex_drive_mount_M2x4_1 | upperarm_r.flex_frame | 采购紧固件 | fastener | 1 |  | M2 | 4 | hex_nut | 3.8 x 3.8 x 6.0 | 按螺纹、长度、材料和实际头部包络一起核对 | parts/r_flex_drive_mount_M2x4_1.step |  | Flange screw with trapped M2 nut; 1.6 mm nominal nut engagement
r_flex_drive_mount_M2_nut_1 | upperarm_r.flex_frame | 采购紧固件 | fastener | 1 |  | M2 |  | hex_nut | 1.6 x 4.0 x 4.619 | 按螺纹、长度、材料和实际头部包络一起核对 | parts/r_flex_drive_mount_M2_nut_1.step |  | Captured nut inside output yoke; fit and creep require testing
r_abduct_drive_split_hub | upperarm_r.abduct_frame | 加工金属 | aluminum | 1 |  |  |  |  | 5.5 x 16.2 x 17.0 | 按 STEP 加工并检验配合；复杂框架先反馈 DFM | parts/r_abduct_drive_split_hub.step |  | Custom split metal D hub; M2 tapped clamp ear; preload/elastic closure not simulated
r_abduct_drive_pinch_M2x10 | upperarm_r.abduct_frame | 采购紧固件 | fastener | 1 |  | M2 | 10 | screw_head_to_drawing | 3.8 x 3.8 x 12.0 | 按螺纹、长度、材料和实际头部包络一起核对 | parts/r_abduct_drive_pinch_M2x10.step |  | M2 transverse pinch screw takes up shaft fit clearance; tightening torque not yet qualified
r_abduct_drive_mount_M2x4_0 | upperarm_r.abduct_frame | 采购紧固件 | fastener | 1 |  | M2 | 4 | hex_nut | 3.8 x 3.8 x 6.0 | 按螺纹、长度、材料和实际头部包络一起核对 | parts/r_abduct_drive_mount_M2x4_0.step |  | Flange screw with trapped M2 nut; 1.6 mm nominal nut engagement
r_abduct_drive_mount_M2_nut_0 | upperarm_r.abduct_frame | 采购紧固件 | fastener | 1 |  | M2 |  | hex_nut | 1.6 x 4.0 x 4.619 | 按螺纹、长度、材料和实际头部包络一起核对 | parts/r_abduct_drive_mount_M2_nut_0.step |  | Captured nut inside output yoke; fit and creep require testing
r_abduct_drive_mount_M2x4_1 | upperarm_r.abduct_frame | 采购紧固件 | fastener | 1 |  | M2 | 4 | hex_nut | 3.8 x 3.8 x 6.0 | 按螺纹、长度、材料和实际头部包络一起核对 | parts/r_abduct_drive_mount_M2x4_1.step |  | Flange screw with trapped M2 nut; 1.6 mm nominal nut engagement
r_abduct_drive_mount_M2_nut_1 | upperarm_r.abduct_frame | 采购紧固件 | fastener | 1 |  | M2 |  | hex_nut | 1.6 x 4.0 x 4.619 | 按螺纹、长度、材料和实际头部包络一起核对 | parts/r_abduct_drive_mount_M2_nut_1.step |  | Captured nut inside output yoke; fit and creep require testing
l_abduct_sensor_rear_journal | upperarm_l.abduct_frame | 加工金属 | aluminum | 1 |  |  |  |  | 4.0 x 4.0 x 18.0 | 按 STEP 加工并检验配合；复杂框架先反馈 DFM | parts/l_abduct_sensor_rear_journal.step |  | Custom nonferromagnetic 4 mm journal; inner radial M2 and outer axial M2 retention
l_abduct_sensor_journal_radial_M2x4 | upperarm_l.abduct_frame | 采购紧固件 | brass | 1 |  | M2 | 4 | screw_head_to_drawing | 3.8 x 3.8 x 6.0 | 按螺纹、长度、材料和实际头部包络一起核对 | parts/l_abduct_sensor_journal_radial_M2x4.step |  | Candidate nonferromagnetic M2x4; keyed shaft is installed after front clutch screw, before twist shaft
l_abduct_sensor_magnet_carrier | upperarm_l.abduct_frame | 打印 | frame | 1 |  |  |  |  | 10.6 x 12.5 x 14.8 | PLA 候选，按随件 STL 和切片复核要求 | parts/l_abduct_sensor_magnet_carrier.step | print_candidates/l_abduct_sensor_magnet_carrier.stl | D driven magnet cup with separate axial screw; 0.1 mm radial adhesive bed prevents magnet rotation; adhesive selection and rotational slip test pending
l_abduct_sensor_carrier_axial_M2x6 | upperarm_l.abduct_frame | 采购紧固件 | nylon | 1 |  | M2 | 6 | screw_head_to_drawing | 3.5 x 3.5 x 7.4 | 按螺纹、长度、材料和实际头部包络一起核对 | parts/l_abduct_sensor_carrier_axial_M2x6.step |  | Insert before magnet; nonmagnetic M2 screw into rear journal
l_abduct_sensor_diametric_magnet_6x2p5 | upperarm_l.abduct_frame | 采购标准件 | magnet | 1 | AS5000-MD6H-2 |  |  |  | 2.5 x 6.0 x 6.0 | AS5000-MD6H-2 候选，Ø6×2.5 径向充磁，逐件核对磁场 | parts/l_abduct_sensor_diametric_magnet_6x2p5.step |  | 6 x 2.5 mm diametrically magnetized candidate, never axially magnetized; grade and diagnostics require testing
l_abduct_sensor_magnet_retaining_bridge | upperarm_l.abduct_frame | 打印 | frame | 1 |  |  |  |  | 0.8 x 4.8 x 14.8 | PLA 候选，按随件 STL 和切片复核要求 | parts/l_abduct_sensor_magnet_retaining_bridge.step | print_candidates/l_abduct_sensor_magnet_retaining_bridge.stl | Positive removable cover; magnet face seats at 36.5 mm, no adhesive-only axial retention
l_abduct_sensor_magnet_cover_M2x6_0 | upperarm_l.abduct_frame | 采购紧固件 | nylon | 1 |  | M2 | 6 | screw_head_to_drawing | 3.5 x 3.5 x 7.4 | 按螺纹、长度、材料和实际头部包络一起核对 | parts/l_abduct_sensor_magnet_cover_M2x6_0.step |  | Nominal M2 nylon screw into cup; printed threads not qualified
l_abduct_sensor_magnet_cover_M2x6_1 | upperarm_l.abduct_frame | 采购紧固件 | nylon | 1 |  | M2 | 6 | screw_head_to_drawing | 3.5 x 3.5 x 7.4 | 按螺纹、长度、材料和实际头部包络一起核对 | parts/l_abduct_sensor_magnet_cover_M2x6_1.step |  | Nominal M2 nylon screw into cup; printed threads not qualified
l_abduct_sensor_pcb_AS5048A | upperarm_l.flex_frame | PCBA内含 | pcb_component | 1 |  |  |  |  | 1.0 x 5.0 x 6.4 | 按电子板成套，不按机械实体重复采购 | parts/l_abduct_sensor_pcb_AS5048A.step |  | Actual sensor_revB STEP; model holes/parts preserved; 1.51 mm STEP board versus 1.6 mm nominal fabrication
l_abduct_sensor_pcb_passive_1 | upperarm_l.flex_frame | PCBA内含 | pcb_component | 1 |  |  |  |  | 0.8 x 0.8 x 1.6 | 按电子板成套，不按机械实体重复采购 | parts/l_abduct_sensor_pcb_passive_1.step |  | Actual sensor_revB STEP; model holes/parts preserved; 1.51 mm STEP board versus 1.6 mm nominal fabrication
l_abduct_sensor_pcb_passive_2 | upperarm_l.flex_frame | PCBA内含 | pcb_component | 1 |  |  |  |  | 0.45 x 0.8 x 1.6 | 按电子板成套，不按机械实体重复采购 | parts/l_abduct_sensor_pcb_passive_2.step |  | Actual sensor_revB STEP; model holes/parts preserved; 1.51 mm STEP board versus 1.6 mm nominal fabrication
l_abduct_sensor_pcb_passive_3 | upperarm_l.flex_frame | PCBA内含 | pcb_component | 1 |  |  |  |  | 1.05 x 1.45 x 2.3 | 按电子板成套，不按机械实体重复采购 | parts/l_abduct_sensor_pcb_passive_3.step |  | Murata GRM219R61E106KA12D 10 uF 25 V X5R, max .95 mm body + .10 mm solder seating allocation
l_abduct_sensor_pcb_passive_4 | upperarm_l.flex_frame | PCBA内含 | pcb_component | 1 |  |  |  |  | 0.45 x 0.8 x 1.6 | 按电子板成套，不按机械实体重复采购 | parts/l_abduct_sensor_pcb_passive_4.step |  | Actual sensor_revB STEP; model holes/parts preserved; 1.51 mm STEP board versus 1.6 mm nominal fabrication
l_abduct_sensor_pcb_J1_back_connector | upperarm_l.flex_frame | PCBA内含 | pcb_component | 1 |  |  |  |  | 3.3 x 9.4 x 9.6 | 按电子板成套，不按机械实体重复采购 | parts/l_abduct_sensor_pcb_J1_back_connector.step |  | JST SH6 SM06B-SRSS-TB with conservative mated allocation; actual 18 x20 x1.6 PCB keeps chip, holes and native pin order; wire exit toward local +Y
l_abduct_sensor_pcb_board | upperarm_l.flex_frame | PCBA内含 | pcb | 1 |  |  |  |  | 1.51 x 18.0 x 20.0 | 按电子板成套，不按机械实体重复采购 | parts/l_abduct_sensor_pcb_board.step |  | Actual sensor_revB STEP; model holes/parts preserved; 1.51 mm STEP board versus 1.6 mm nominal fabrication
l_abduct_sensor_nylon_spacer_0 | upperarm_l.flex_frame | 加工塑料 | nylon | 1 |  |  |  |  | 4.6 x 4.6 x 6.0 | POM-C / 未填充 PEEK / PA12 按材质分别加工；薄件不等同 PLA 打印 | parts/l_abduct_sensor_nylon_spacer_0.step |  | M2 female 6 mm spacer; electrical insulation and spreaders required
l_abduct_sensor_nylon_spreader_0 | upperarm_l.flex_frame | 加工塑料 | nylon | 1 |  |  |  |  | 0.5 x 4.4 x 4.4 | POM-C / 未填充 PEEK / PA12 按材质分别加工；薄件不等同 PLA 打印 | parts/l_abduct_sensor_nylon_spreader_0.step |  | 0.5 mm insulating spreader, OD4.4/ID2.2
l_abduct_sensor_board_M2x4_0 | upperarm_l.flex_frame | 采购紧固件 | nylon | 1 |  | M2 | 4 | screw_head_to_drawing | 3.5 x 3.5 x 5.4 | 按螺纹、长度、材料和实际头部包络一起核对 | parts/l_abduct_sensor_board_M2x4_0.step |  | Front board screw; 1.99 mm nominal engagement
l_abduct_sensor_support_M2x6_0 | upperarm_l.flex_frame | 采购紧固件 | nylon | 1 |  | M2 | 6 | screw_head_to_drawing | 3.5 x 3.5 x 7.4 | 按螺纹、长度、材料和实际头部包络一起核对 | parts/l_abduct_sensor_support_M2x6_0.step |  | Rear support screw; 3 mm nominal engagement; 1.01 mm gap to opposing screw
l_abduct_sensor_nylon_spacer_1 | upperarm_l.flex_frame | 加工塑料 | nylon | 1 |  |  |  |  | 4.6 x 4.6 x 6.0 | POM-C / 未填充 PEEK / PA12 按材质分别加工；薄件不等同 PLA 打印 | parts/l_abduct_sensor_nylon_spacer_1.step |  | M2 female 6 mm spacer; electrical insulation and spreaders required
l_abduct_sensor_nylon_spreader_1 | upperarm_l.flex_frame | 加工塑料 | nylon | 1 |  |  |  |  | 0.5 x 4.4 x 4.4 | POM-C / 未填充 PEEK / PA12 按材质分别加工；薄件不等同 PLA 打印 | parts/l_abduct_sensor_nylon_spreader_1.step |  | 0.5 mm insulating spreader, OD4.4/ID2.2
l_abduct_sensor_board_M2x4_1 | upperarm_l.flex_frame | 采购紧固件 | nylon | 1 |  | M2 | 4 | screw_head_to_drawing | 3.5 x 3.5 x 5.4 | 按螺纹、长度、材料和实际头部包络一起核对 | parts/l_abduct_sensor_board_M2x4_1.step |  | Front board screw; 1.99 mm nominal engagement
l_abduct_sensor_support_M2x6_1 | upperarm_l.flex_frame | 采购紧固件 | nylon | 1 |  | M2 | 6 | screw_head_to_drawing | 3.5 x 3.5 x 7.4 | 按螺纹、长度、材料和实际头部包络一起核对 | parts/l_abduct_sensor_support_M2x6_1.step |  | Rear support screw; 3 mm nominal engagement; 1.01 mm gap to opposing screw
r_abduct_sensor_rear_journal | upperarm_r.abduct_frame | 加工金属 | aluminum | 1 |  |  |  |  | 4.0 x 4.0 x 18.0 | 按 STEP 加工并检验配合；复杂框架先反馈 DFM | parts/r_abduct_sensor_rear_journal.step |  | Custom nonferromagnetic 4 mm journal; inner radial M2 and outer axial M2 retention
r_abduct_sensor_journal_radial_M2x4 | upperarm_r.abduct_frame | 采购紧固件 | brass | 1 |  | M2 | 4 | screw_head_to_drawing | 3.8 x 3.8 x 6.0 | 按螺纹、长度、材料和实际头部包络一起核对 | parts/r_abduct_sensor_journal_radial_M2x4.step |  | Candidate nonferromagnetic M2x4; keyed shaft is installed after front clutch screw, before twist shaft
r_abduct_sensor_magnet_carrier | upperarm_r.abduct_frame | 打印 | frame | 1 |  |  |  |  | 10.6 x 12.5 x 14.8 | PLA 候选，按随件 STL 和切片复核要求 | parts/r_abduct_sensor_magnet_carrier.step | print_candidates/r_abduct_sensor_magnet_carrier.stl | D driven magnet cup with separate axial screw; 0.1 mm radial adhesive bed prevents magnet rotation; adhesive selection and rotational slip test pending
r_abduct_sensor_carrier_axial_M2x6 | upperarm_r.abduct_frame | 采购紧固件 | nylon | 1 |  | M2 | 6 | screw_head_to_drawing | 3.5 x 3.5 x 7.4 | 按螺纹、长度、材料和实际头部包络一起核对 | parts/r_abduct_sensor_carrier_axial_M2x6.step |  | Insert before magnet; nonmagnetic M2 screw into rear journal
r_abduct_sensor_diametric_magnet_6x2p5 | upperarm_r.abduct_frame | 采购标准件 | magnet | 1 | AS5000-MD6H-2 |  |  |  | 2.5 x 6.0 x 6.0 | AS5000-MD6H-2 候选，Ø6×2.5 径向充磁，逐件核对磁场 | parts/r_abduct_sensor_diametric_magnet_6x2p5.step |  | 6 x 2.5 mm diametrically magnetized candidate, never axially magnetized; grade and diagnostics require testing
r_abduct_sensor_magnet_retaining_bridge | upperarm_r.abduct_frame | 打印 | frame | 1 |  |  |  |  | 0.8 x 4.8 x 14.8 | PLA 候选，按随件 STL 和切片复核要求 | parts/r_abduct_sensor_magnet_retaining_bridge.step | print_candidates/r_abduct_sensor_magnet_retaining_bridge.stl | Positive removable cover; magnet face seats at 36.5 mm, no adhesive-only axial retention
r_abduct_sensor_magnet_cover_M2x6_0 | upperarm_r.abduct_frame | 采购紧固件 | nylon | 1 |  | M2 | 6 | screw_head_to_drawing | 3.5 x 3.5 x 7.4 | 按螺纹、长度、材料和实际头部包络一起核对 | parts/r_abduct_sensor_magnet_cover_M2x6_0.step |  | Nominal M2 nylon screw into cup; printed threads not qualified
r_abduct_sensor_magnet_cover_M2x6_1 | upperarm_r.abduct_frame | 采购紧固件 | nylon | 1 |  | M2 | 6 | screw_head_to_drawing | 3.5 x 3.5 x 7.4 | 按螺纹、长度、材料和实际头部包络一起核对 | parts/r_abduct_sensor_magnet_cover_M2x6_1.step |  | Nominal M2 nylon screw into cup; printed threads not qualified
r_abduct_sensor_pcb_AS5048A | upperarm_r.flex_frame | PCBA内含 | pcb_component | 1 |  |  |  |  | 1.0 x 5.0 x 6.4 | 按电子板成套，不按机械实体重复采购 | parts/r_abduct_sensor_pcb_AS5048A.step |  | Actual sensor_revB STEP; model holes/parts preserved; 1.51 mm STEP board versus 1.6 mm nominal fabrication
r_abduct_sensor_pcb_passive_1 | upperarm_r.flex_frame | PCBA内含 | pcb_component | 1 |  |  |  |  | 0.8 x 0.8 x 1.6 | 按电子板成套，不按机械实体重复采购 | parts/r_abduct_sensor_pcb_passive_1.step |  | Actual sensor_revB STEP; model holes/parts preserved; 1.51 mm STEP board versus 1.6 mm nominal fabrication
r_abduct_sensor_pcb_passive_2 | upperarm_r.flex_frame | PCBA内含 | pcb_component | 1 |  |  |  |  | 0.45 x 0.8 x 1.6 | 按电子板成套，不按机械实体重复采购 | parts/r_abduct_sensor_pcb_passive_2.step |  | Actual sensor_revB STEP; model holes/parts preserved; 1.51 mm STEP board versus 1.6 mm nominal fabrication
r_abduct_sensor_pcb_passive_3 | upperarm_r.flex_frame | PCBA内含 | pcb_component | 1 |  |  |  |  | 1.05 x 1.45 x 2.3 | 按电子板成套，不按机械实体重复采购 | parts/r_abduct_sensor_pcb_passive_3.step |  | Murata GRM219R61E106KA12D 10 uF 25 V X5R, max .95 mm body + .10 mm solder seating allocation
r_abduct_sensor_pcb_passive_4 | upperarm_r.flex_frame | PCBA内含 | pcb_component | 1 |  |  |  |  | 0.45 x 0.8 x 1.6 | 按电子板成套，不按机械实体重复采购 | parts/r_abduct_sensor_pcb_passive_4.step |  | Actual sensor_revB STEP; model holes/parts preserved; 1.51 mm STEP board versus 1.6 mm nominal fabrication
r_abduct_sensor_pcb_J1_back_connector | upperarm_r.flex_frame | PCBA内含 | pcb_component | 1 |  |  |  |  | 3.3 x 9.4 x 9.6 | 按电子板成套，不按机械实体重复采购 | parts/r_abduct_sensor_pcb_J1_back_connector.step |  | JST SH6 SM06B-SRSS-TB with conservative mated allocation; actual 18 x20 x1.6 PCB keeps chip, holes and native pin order; wire exit toward local +Y
r_abduct_sensor_pcb_board | upperarm_r.flex_frame | PCBA内含 | pcb | 1 |  |  |  |  | 1.51 x 18.0 x 20.0 | 按电子板成套，不按机械实体重复采购 | parts/r_abduct_sensor_pcb_board.step |  | Actual sensor_revB STEP; model holes/parts preserved; 1.51 mm STEP board versus 1.6 mm nominal fabrication
r_abduct_sensor_nylon_spacer_0 | upperarm_r.flex_frame | 加工塑料 | nylon | 1 |  |  |  |  | 4.6 x 4.6 x 6.0 | POM-C / 未填充 PEEK / PA12 按材质分别加工；薄件不等同 PLA 打印 | parts/r_abduct_sensor_nylon_spacer_0.step |  | M2 female 6 mm spacer; electrical insulation and spreaders required
r_abduct_sensor_nylon_spreader_0 | upperarm_r.flex_frame | 加工塑料 | nylon | 1 |  |  |  |  | 0.5 x 4.4 x 4.4 | POM-C / 未填充 PEEK / PA12 按材质分别加工；薄件不等同 PLA 打印 | parts/r_abduct_sensor_nylon_spreader_0.step |  | 0.5 mm insulating spreader, OD4.4/ID2.2
r_abduct_sensor_board_M2x4_0 | upperarm_r.flex_frame | 采购紧固件 | nylon | 1 |  | M2 | 4 | screw_head_to_drawing | 3.5 x 3.5 x 5.4 | 按螺纹、长度、材料和实际头部包络一起核对 | parts/r_abduct_sensor_board_M2x4_0.step |  | Front board screw; 1.99 mm nominal engagement
r_abduct_sensor_support_M2x6_0 | upperarm_r.flex_frame | 采购紧固件 | nylon | 1 |  | M2 | 6 | screw_head_to_drawing | 3.5 x 3.5 x 7.4 | 按螺纹、长度、材料和实际头部包络一起核对 | parts/r_abduct_sensor_support_M2x6_0.step |  | Rear support screw; 3 mm nominal engagement; 1.01 mm gap to opposing screw
r_abduct_sensor_nylon_spacer_1 | upperarm_r.flex_frame | 加工塑料 | nylon | 1 |  |  |  |  | 4.6 x 4.6 x 6.0 | POM-C / 未填充 PEEK / PA12 按材质分别加工；薄件不等同 PLA 打印 | parts/r_abduct_sensor_nylon_spacer_1.step |  | M2 female 6 mm spacer; electrical insulation and spreaders required
r_abduct_sensor_nylon_spreader_1 | upperarm_r.flex_frame | 加工塑料 | nylon | 1 |  |  |  |  | 0.5 x 4.4 x 4.4 | POM-C / 未填充 PEEK / PA12 按材质分别加工；薄件不等同 PLA 打印 | parts/r_abduct_sensor_nylon_spreader_1.step |  | 0.5 mm insulating spreader, OD4.4/ID2.2
r_abduct_sensor_board_M2x4_1 | upperarm_r.flex_frame | 采购紧固件 | nylon | 1 |  | M2 | 4 | screw_head_to_drawing | 3.5 x 3.5 x 5.4 | 按螺纹、长度、材料和实际头部包络一起核对 | parts/r_abduct_sensor_board_M2x4_1.step |  | Front board screw; 1.99 mm nominal engagement
r_abduct_sensor_support_M2x6_1 | upperarm_r.flex_frame | 采购紧固件 | nylon | 1 |  | M2 | 6 | screw_head_to_drawing | 3.5 x 3.5 x 7.4 | 按螺纹、长度、材料和实际头部包络一起核对 | parts/r_abduct_sensor_support_M2x6_1.step |  | Rear support screw; 3 mm nominal engagement; 1.01 mm gap to opposing screw
l_twist_sensor_integral_magnet_shaft | upperarm_l | 加工金属 | aluminum_7075 | 1 |  |  |  |  | 10.6 x 10.6 x 33.0 | 按 STEP 加工并检验配合；复杂框架先反馈 DFM | parts/l_twist_sensor_integral_magnet_shaft.step |  | D4 arm drive and friction rotor drive; side-assembled keyed groove on Z -17.626..-16.426, D3 / flat 1.1; no inaccessible end nut; integral magnet cup and metal thrust shoulder
l_twist_sensor_diametric_magnet_6x2p5 | upperarm_l | 采购标准件 | magnet | 1 | AS5000-MD6H-2 |  |  |  | 2.5 x 6.0 x 6.0 | AS5000-MD6H-2 候选，Ø6×2.5 径向充磁，逐件核对磁场 | parts/l_twist_sensor_diametric_magnet_6x2p5.step |  | 6 x 2.5 diametric magnet; 0.1 mm radial adhesive allowance; grade and field not qualified
l_twist_sensor_magnet_keeper | upperarm_l | 打印 | frame | 1 |  |  |  |  | 2.6 x 13.0 x 13.0 | PLA 候选，按随件 STL 和切片复核要求 | parts/l_twist_sensor_magnet_keeper.step | print_candidates/l_twist_sensor_magnet_keeper.stl | Removable rigid cover retains outer 0.5 mm of magnet face; 0.6 mm cover, radial brass screw attachment; print durability pending
l_twist_sensor_keeper_set_M2x3_0 | upperarm_l | 采购紧固件 | brass | 1 |  | M2 | 3 | set_screw | 2.0 x 2.0 x 3.0 | 按螺纹、长度、材料和实际头部包络一起核对 | parts/l_twist_sensor_keeper_set_M2x3_0.step |  | Nominal slotted brass M2x3 set screw; exact purchased part and slot specification pending
l_twist_sensor_keeper_set_M2x3_1 | upperarm_l | 采购紧固件 | brass | 1 |  | M2 | 3 | set_screw | 2.0 x 2.0 x 3.0 | 按螺纹、长度、材料和实际头部包络一起核对 | parts/l_twist_sensor_keeper_set_M2x3_1.step |  | Nominal slotted brass M2x3 set screw; exact purchased part and slot specification pending
l_twist_sensor_arm_radial_M2x6 | upperarm_l | 采购紧固件 | brass | 1 |  | M2 | 6 | screw_head_to_drawing | 3.8 x 3.8 x 8.0 | 按螺纹、长度、材料和实际头部包络一起核对 | parts/l_twist_sensor_arm_radial_M2x6.step |  | Simplified brass M2x6; 1.5 mm nominal thread engagement through the D flat; head tool recess is an envelope
l_twist_sensor_pcb_AS5048A | upperarm_l.abduct_frame | PCBA内含 | pcb_component | 1 |  |  |  |  | 1.0 x 5.0 x 6.4 | 按电子板成套，不按机械实体重复采购 | parts/l_twist_sensor_pcb_AS5048A.step |  | actual_KiCad_STEP
l_twist_sensor_pcb_C1 | upperarm_l.abduct_frame | PCBA内含 | pcb_component | 1 |  |  |  |  | 0.8 x 0.8 x 1.6 | 按电子板成套，不按机械实体重复采购 | parts/l_twist_sensor_pcb_C1.step |  | actual_KiCad_STEP
l_twist_sensor_pcb_C2 | upperarm_l.abduct_frame | PCBA内含 | pcb_component | 1 |  |  |  |  | 1.05 x 1.45 x 2.3 | 按电子板成套，不按机械实体重复采购 | parts/l_twist_sensor_pcb_C2.step |  | Murata GRM219R61E106KA12D 10 uF 25 V X5R, max .95 mm body + .10 mm solder seating allocation
l_twist_sensor_pcb_R1 | upperarm_l.abduct_frame | PCBA内含 | pcb_component | 1 |  |  |  |  | 0.45 x 0.8 x 1.6 | 按电子板成套，不按机械实体重复采购 | parts/l_twist_sensor_pcb_R1.step |  | actual_KiCad_STEP
l_twist_sensor_pcb_R2 | upperarm_l.abduct_frame | PCBA内含 | pcb_component | 1 |  |  |  |  | 0.45 x 0.8 x 1.6 | 按电子板成套，不按机械实体重复采购 | parts/l_twist_sensor_pcb_R2.step |  | actual_KiCad_STEP
l_twist_sensor_pcb_board | upperarm_l.abduct_frame | PCBA内含 | pcb | 1 |  |  |  |  | 0.91 x 10.0 x 12.0 | 按电子板成套，不按机械实体重复采购 | parts/l_twist_sensor_pcb_board.step |  | actual_KiCad_STEP
l_twist_sensor_pcb_J1_dimension_envelope | upperarm_l.abduct_frame | PCBA内含 | pcb_component | 1 |  |  |  |  | 3.3 x 9.4 x 9.6 | 按电子板成套，不按机械实体重复采购 | parts/l_twist_sensor_pcb_J1_dimension_envelope.step |  | JST SM06B-SRSS-TB side-entry SH6, conservative 9.4 x9.6 x3.3 mm mated plug allocation; cable bend remains a separate harness requirement
l_twist_sensor_board_seat_saddle_0 | upperarm_l.abduct_frame | 打印 | frame | 1 |  |  |  |  | 1.8 x 4.0 x 4.25 | PLA 候选，按随件 STL 和切片复核要求 | parts/l_twist_sensor_board_seat_saddle_0.step | print_candidates/l_twist_sensor_board_seat_saddle_0.stl | Separate L saddle installed after complete magnet shaft; locating wall at +/-6.1, nominal 1.0 mm board slot; never fuse to base posts
l_twist_sensor_board_seat_saddle_1 | upperarm_l.abduct_frame | 打印 | frame | 1 |  |  |  |  | 1.8 x 4.0 x 4.25 | PLA 候选，按随件 STL 和切片复核要求 | parts/l_twist_sensor_board_seat_saddle_1.step | print_candidates/l_twist_sensor_board_seat_saddle_1.stl | Separate L saddle installed after complete magnet shaft; locating wall at +/-6.1, nominal 1.0 mm board slot; never fuse to base posts
l_twist_sensor_board_edge_cap_0 | upperarm_l.abduct_frame | 加工塑料 | nylon | 1 |  |  |  |  | 0.8 x 4.0 x 4.25 | POM-C / 未填充 PEEK / PA12 按材质分别加工；薄件不等同 PLA 打印 | parts/l_twist_sensor_board_edge_cap_0.step |  | Removable insulating edge retainer; nominal 1.0 mm board stack; STEP FR4 body is 0.91 mm excluding copper/model offsets; fit requires physical verification
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
