fukawachan/PoseDollLab_Design/Hardware/PoseDoll44/generated/revO2/runs/o2_20260923_r1/electronics/proximal5/proximal5_with_mating_study.step

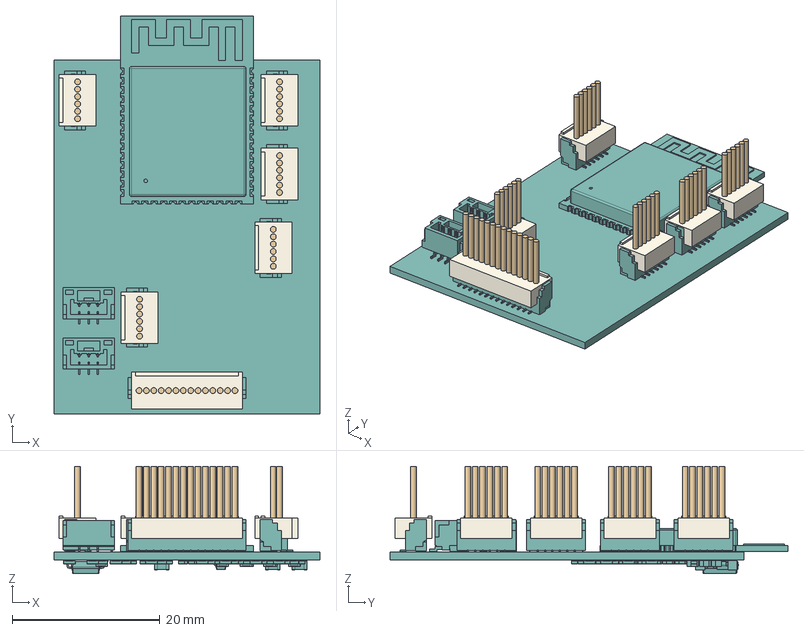
[picture p21: CAD file, 2026-09-23]
Hardware/PoseDoll44/generated/revO2/runs/o2_20260923_r1/electronics/proximal5/proximal5_with_mating_study.step
36.0 x 54.0 x 14.5 mm
KiCad_export_available_models
J12_mating_housing_study
J12_wire_1
J12_wire_2
J12_wire_3
J12_wire_4
J12_wire_5
J12_wire_6
J11_mating_housing_study
J11_wire_1
J11_wire_2
J11_wire_3
J11_wire_4
J11_wire_5
J11_wire_6
J15_mating_housing_study
J15_wire_1
J15_wire_2
J15_wire_3
J15_wire_4
J15_wire_5
J15_wire_6
J14_mating_housing_study
J14_wire_1
J14_wire_2
J14_wire_3
J14_wire_4
J14_wire_5
J14_wire_6
J50_mating_housing_study
J50_wire_1
J50_wire_2
J50_wire_3
J50_wire_4
J50_wire_5
J50_wire_6
J50_wire_7
J50_wire_8
J50_wire_9
J50_wire_10
J50_wire_11
J50_wire_12
J50_wire_13
J50_wire_14
J13_mating_housing_study
J13_wire_1
J13_wire_2
J13_wire_3
J13_wire_4
J13_wire_5
J13_wire_6
