fukawachan/PoseDollLab_Design/Hardware/PoseDoll44/generated/revO3/runs/o3_20260924_r1/electronics/proximal5/PoseDoll_RevO3_proximal5.step

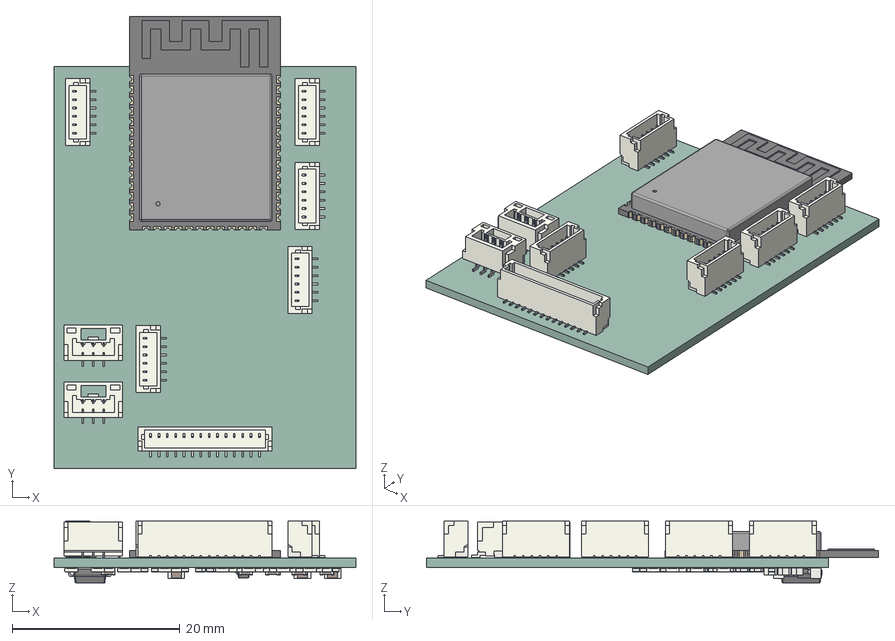
[picture p22: CAD file, 2026-09-23]
Hardware/PoseDoll44/generated/revO3/runs/o3_20260924_r1/electronics/proximal5/PoseDoll_RevO3_proximal5.step
36.0 x 54.0 x 7.35 mm
JST_SH_BM06B-SRSS-TB_1x06-1MP_P1.00mm_Vertical x 5
ESP32-S3-WROOM-1
JST_SH_BM14B-SRSS-TB_1x14-1MP_P1.00mm_Vertical
JST_BM03B_GHS_TBT x 2
R_0603_1608Metric x 56
C_0805_2012Metric x 3
C_0603_1608Metric x 11
SOIC-8_3.9x4.9mm_P1.27mm
SOT-23
PoseDoll_RevO3_proximal5_PCB
