fukawachan/PoseDollLab_Design/Hardware/PoseDoll44/generated/revO3/runs/o3_20260924_r1/joint/disc_spring_2.step

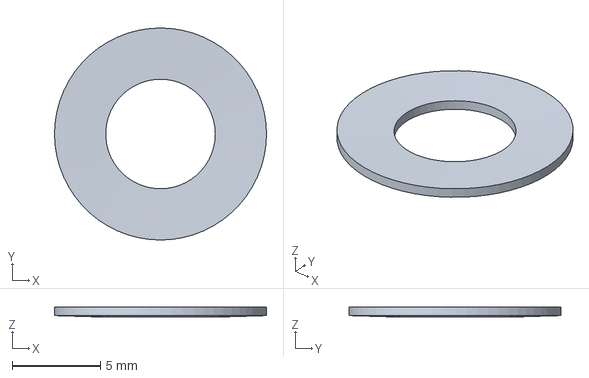
[picture p23: CAD file, 2026-09-23]
Hardware/PoseDoll44/generated/revO3/runs/o3_20260924_r1/joint/disc_spring_2.step
12.0 x 12.0 x 0.588 mm
