fukawachan/PoseDollLab_Design/Hardware/PoseDoll44/generated/revO3/runs/o3_20260924_r1/pcba/distal4/J50_unplug_corridor.step

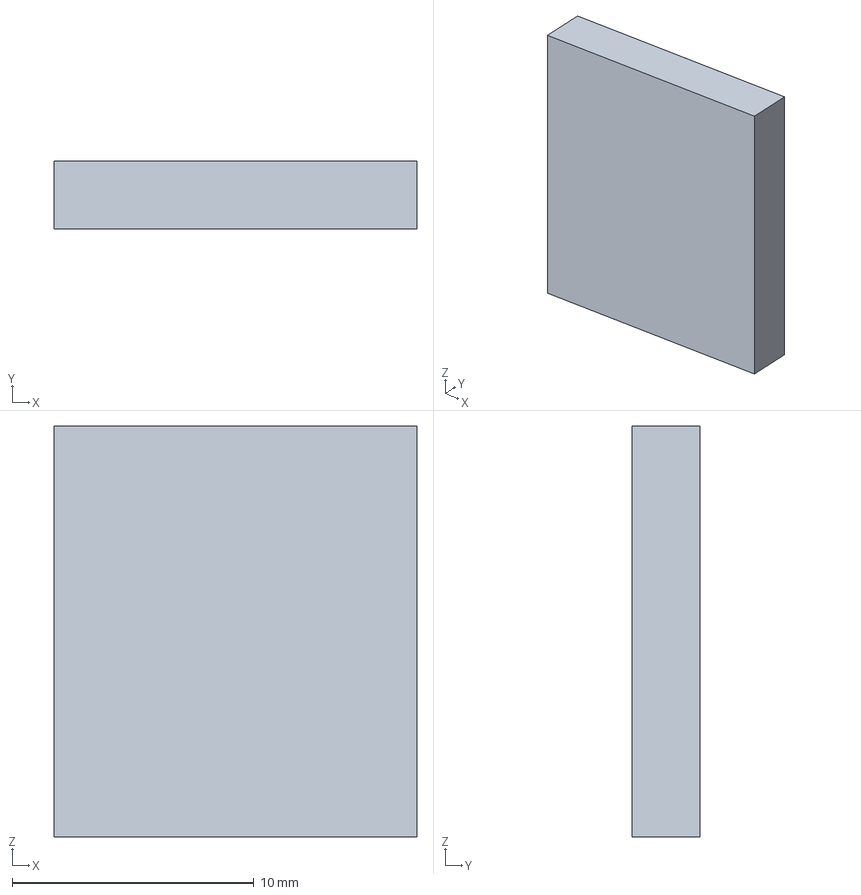
[picture p24: CAD file, 2026-09-23]
Hardware/PoseDoll44/generated/revO3/runs/o3_20260924_r1/pcba/distal4/J50_unplug_corridor.step
15.0 x 2.80 x 17.0 mm
