fukawachan/PoseDollLab_Design/Hardware/PoseDoll44/generated/revO3/runs/o3_20260924_r1/pcba/distal4_narrow/J50_catalog_mating.step

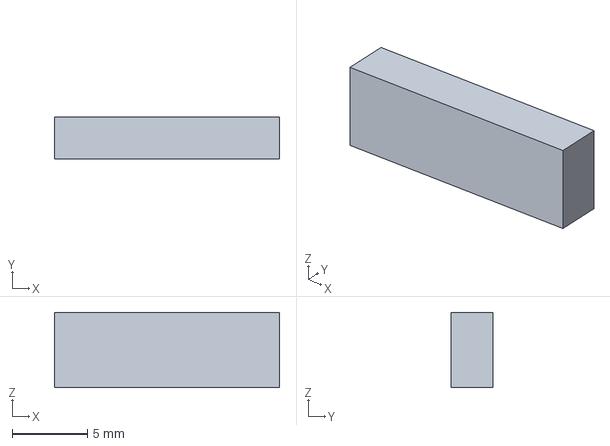
[picture p25: CAD file, 2026-09-23]
Hardware/PoseDoll44/generated/revO3/runs/o3_20260924_r1/pcba/distal4_narrow/J50_catalog_mating.step
15.0 x 2.80 x 5.00 mm
