fukawachan/PoseDollLab_Design/Hardware/PoseDoll44/generated/revO3/runs/o3_20260924_r1/pcba/proximal5/J12_catalog_mating.step

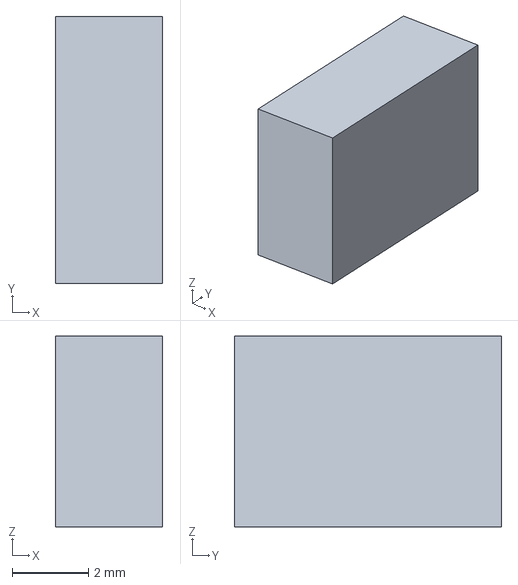
[picture p27: CAD file, 2026-09-23]
Hardware/PoseDoll44/generated/revO3/runs/o3_20260924_r1/pcba/proximal5/J12_catalog_mating.step
2.80 x 7.00 x 5.00 mm
