fukawachan/PoseDollLab_Design/Hardware/PoseDoll44/generated/revO3/runs/o3_20260924_r1/pcba/proximal5_side/J11_bend_R4.step

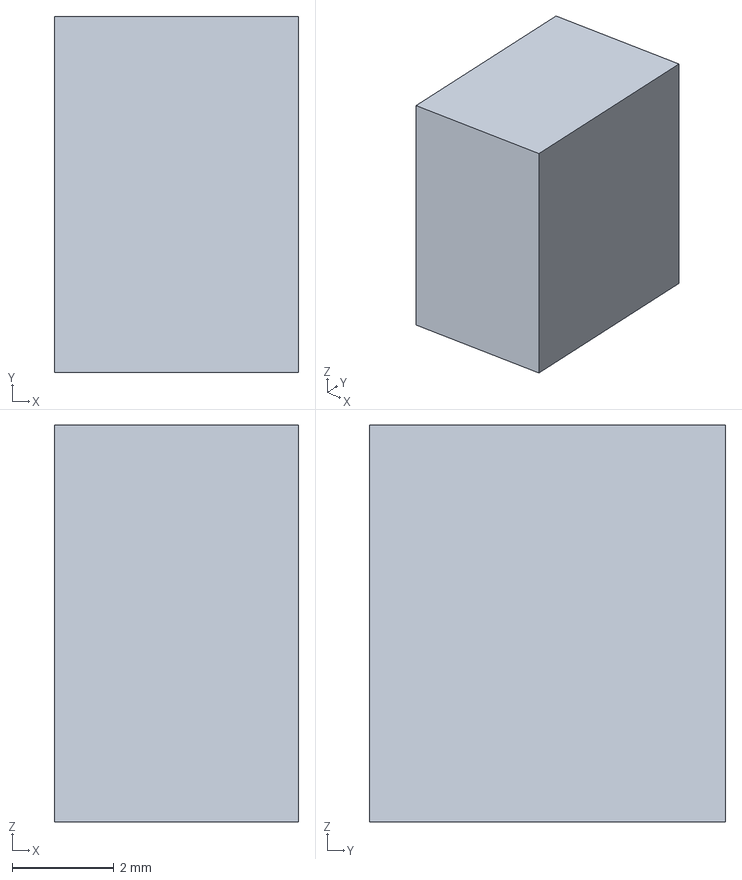
[picture p28: CAD file, 2026-09-23]
Hardware/PoseDoll44/generated/revO3/runs/o3_20260924_r1/pcba/proximal5_side/J11_bend_R4.step
4.80 x 7.00 x 7.80 mm
