fukawachan/PoseDollLab_Design/Hardware/PoseDoll44/generated/revO3/runs/o3_20260924_r2/joint/thrust_rear_R.step

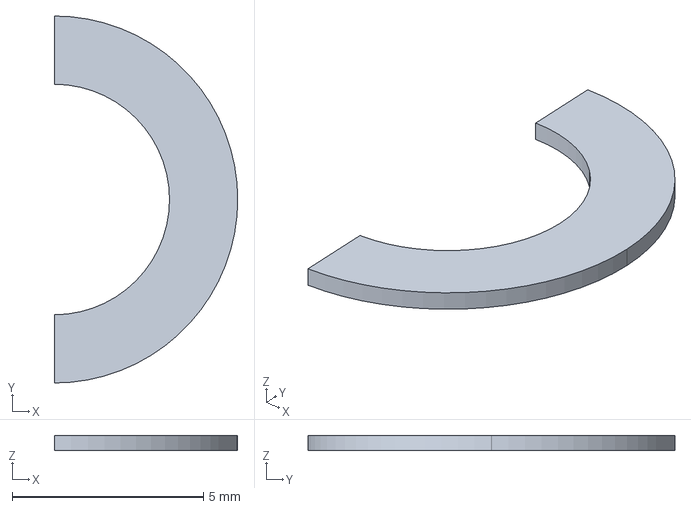
[picture p29: CAD file, 2026-09-23]
Hardware/PoseDoll44/generated/revO3/runs/o3_20260924_r2/joint/thrust_rear_R.step
4.80 x 9.60 x 0.4 mm
