fukawachan/PoseDollLab_Design/Hardware/PoseDoll44/generated/revO3/runs/o3_20260924_r2/pcba/distal4_side/J18_unplug_corridor.step

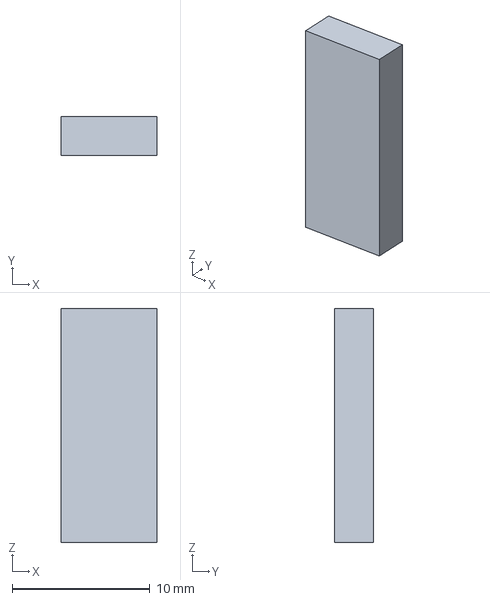
[picture p30: CAD file, 2026-09-23]
Hardware/PoseDoll44/generated/revO3/runs/o3_20260924_r2/pcba/distal4_side/J18_unplug_corridor.step
7.00 x 2.80 x 17.0 mm
