fukawachan/PoseDollLab_Design/Hardware/PoseDoll44/generated/revO3/runs/o3_20260924_r3/joint/cup_mount_1.step

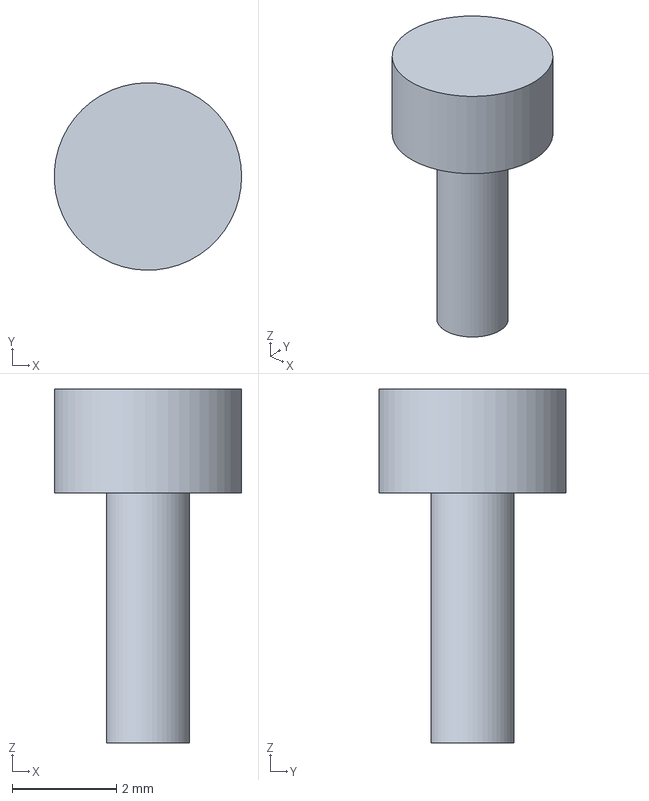
[picture p31: CAD file, 2026-09-23]
Hardware/PoseDoll44/generated/revO3/runs/o3_20260924_r3/joint/cup_mount_1.step
3.60 x 3.60 x 6.80 mm
