fukawachan/PoseDollLab_Design/Hardware/PoseDoll44/generated/revO/prototypes/A01_journal_fit_coupon.step

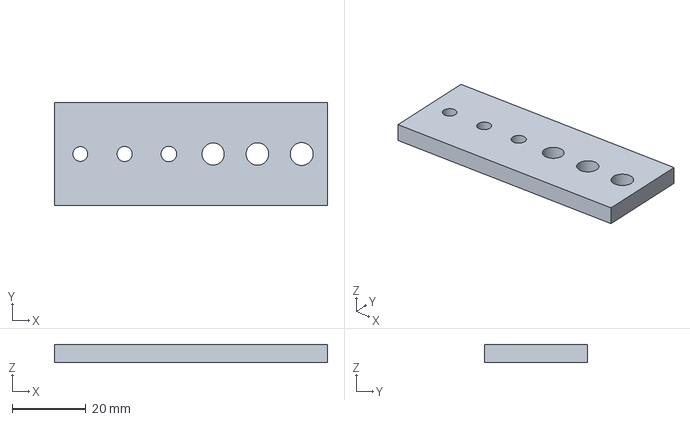
[picture p32: CAD file, 2026-09-23]
Hardware/PoseDoll44/generated/revO/prototypes/A01_journal_fit_coupon.step
74.0 x 28.0 x 5.00 mm
