fukawachan/PoseDollLab_Design/Hardware/PoseDoll44/generated/revO2/runs/o2_20260923_r1/electronics/distal4/distal4_with_mating_study.step

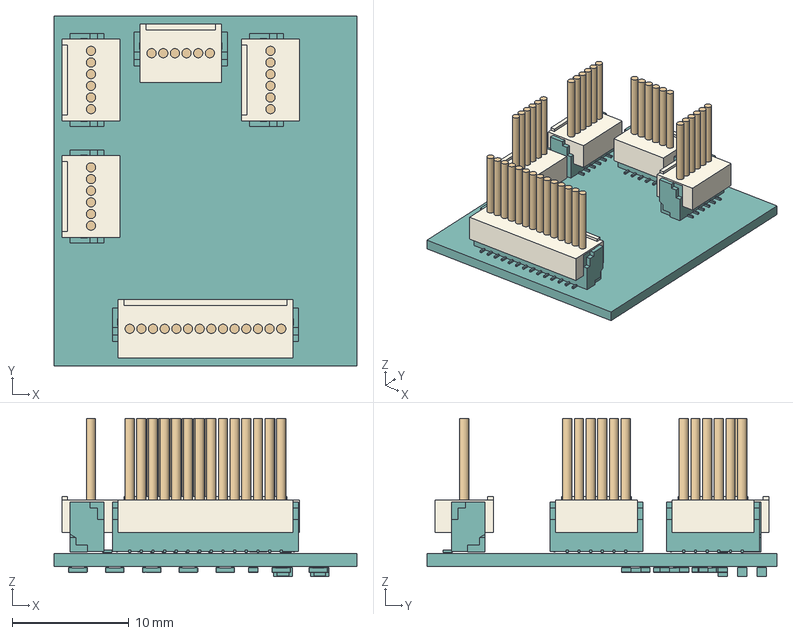
[picture p33: CAD file, 2026-09-23]
Hardware/PoseDoll44/generated/revO2/runs/o2_20260923_r1/electronics/distal4/distal4_with_mating_study.step
26.0 x 30.0 x 13.6 mm
KiCad_export_available_models
J19_mating_housing_study
J19_wire_1
J19_wire_2
J19_wire_3
J19_wire_4
J19_wire_5
J19_wire_6
J18_mating_housing_study
J18_wire_1
J18_wire_2
J18_wire_3
J18_wire_4
J18_wire_5
J18_wire_6
J50_mating_housing_study
J50_wire_1
J50_wire_2
J50_wire_3
J50_wire_4
J50_wire_5
J50_wire_6
J50_wire_7
J50_wire_8
J50_wire_9
J50_wire_10
J50_wire_11
J50_wire_12
J50_wire_13
J50_wire_14
J16_mating_housing_study
J16_wire_1
J16_wire_2
J16_wire_3
J16_wire_4
J16_wire_5
J16_wire_6
J17_mating_housing_study
J17_wire_1
J17_wire_2
J17_wire_3
J17_wire_4
J17_wire_5
J17_wire_6
