fukawachan/PoseDollLab_Design/Hardware/PoseDoll44/generated/revO3/runs/o3_20260924_r1/joint/rear_bush_R.step

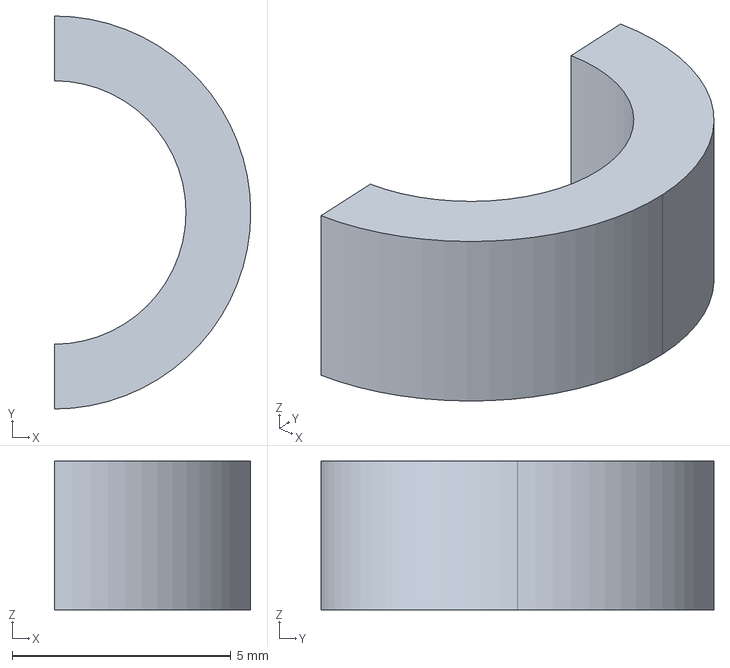
[picture p35: CAD file, 2026-09-23]
Hardware/PoseDoll44/generated/revO3/runs/o3_20260924_r1/joint/rear_bush_R.step
4.49 x 8.98 x 3.40 mm
