fukawachan/PoseDollLab_Design/Hardware/PoseDoll44/generated/revO3/runs/o3_20260924_r2/joint/rear_lining_backing.step

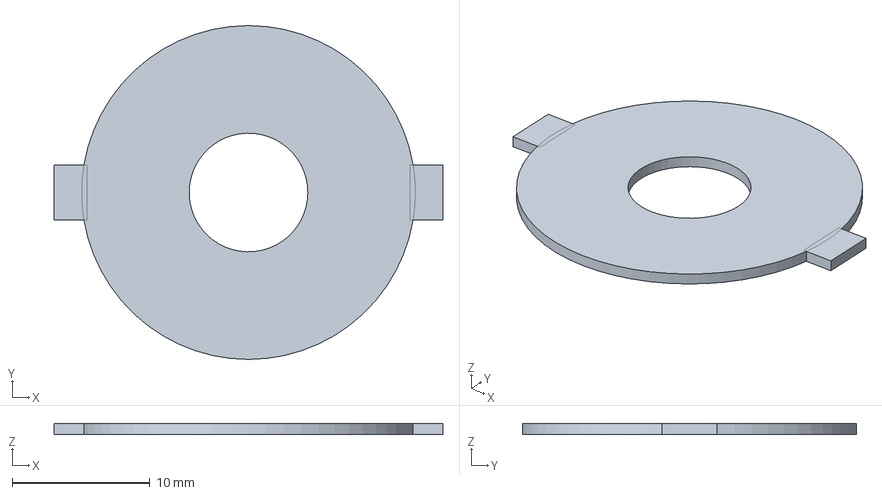
[picture p36: CAD file, 2026-09-23]
Hardware/PoseDoll44/generated/revO3/runs/o3_20260924_r2/joint/rear_lining_backing.step
28.2 x 24.2 x 0.8 mm
