fukawachan/PoseDollLab_Design/Hardware/PoseDoll44/generated/revO3/runs/o3_20260924_r2/pcba/proximal5/J1_missing_model_envelope.step

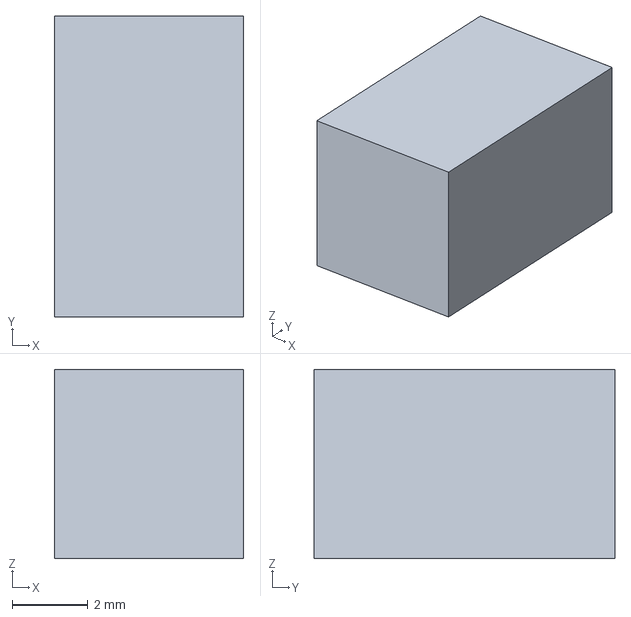
[picture p37: CAD file, 2026-09-23]
Hardware/PoseDoll44/generated/revO3/runs/o3_20260924_r2/pcba/proximal5/J1_missing_model_envelope.step
5.00 x 7.95 x 5.00 mm
