fukawachan/PoseDollLab_Design/Hardware/PoseDoll44/generated/revO3/runs/o3_20260924_r2/joint/measurement_shaft.step

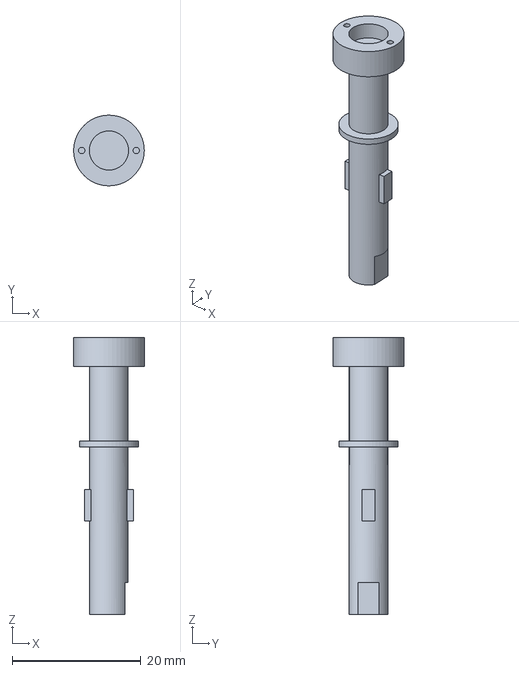
[picture p38: CAD file, 2026-09-23]
Hardware/PoseDoll44/generated/revO3/runs/o3_20260924_r2/joint/measurement_shaft.step
11.0 x 11.0 x 43.1 mm
