fukawachan/PoseDollLab_Design/Hardware/PoseDoll44/generated/revO3/runs/o3_20260924_r3/joint/hollow_pin_spanner.step

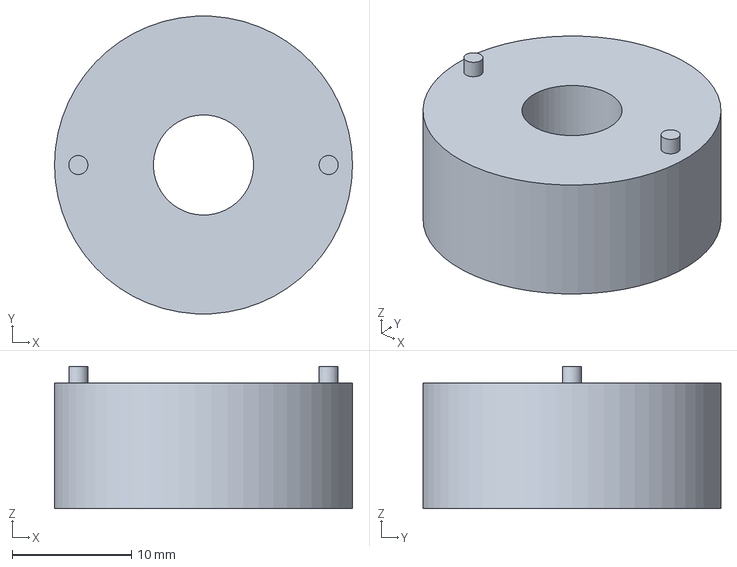
[picture p39: CAD file, 2026-09-23]
Hardware/PoseDoll44/generated/revO3/runs/o3_20260924_r3/joint/hollow_pin_spanner.step
25.0 x 25.0 x 11.9 mm
