fukawachan/PoseDollLab_Design/Hardware/PoseDoll44/generated/revO3/runs/o3_20260924_r1/joint/sensor_pcba_5.step

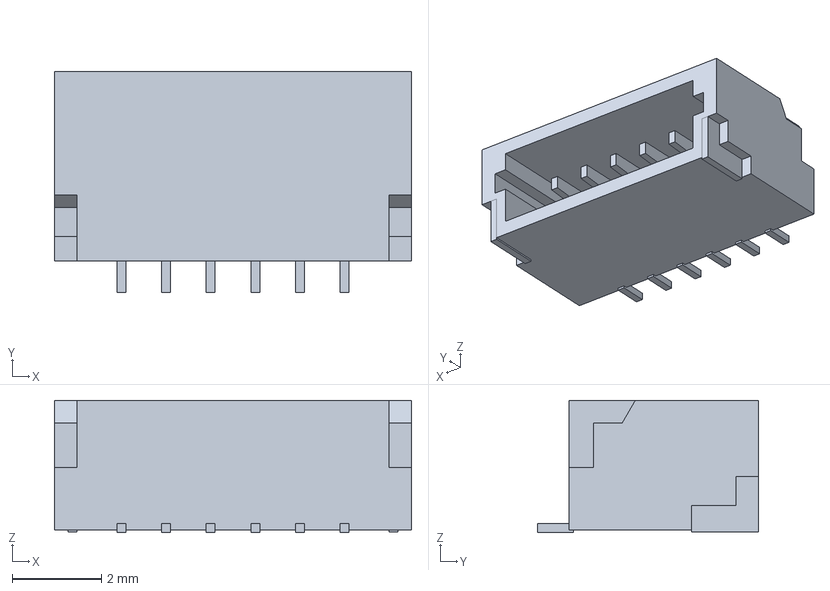
[picture p40: CAD file, 2026-09-23]
Hardware/PoseDoll44/generated/revO3/runs/o3_20260924_r1/joint/sensor_pcba_5.step
8.00 x 4.95 x 2.96 mm
