fukawachan/PoseDollLab_Design/Hardware/PoseDoll44/generated/revO3/runs/o3_20260924_r2/pcba/proximal5_side/antenna_manufacturer_air.step

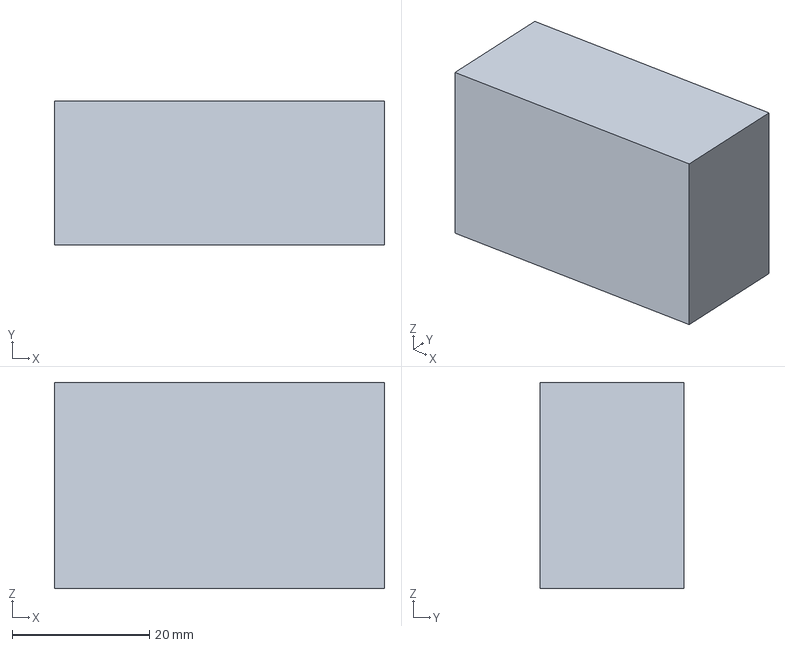
[picture p41: CAD file, 2026-09-23]
Hardware/PoseDoll44/generated/revO3/runs/o3_20260924_r2/pcba/proximal5_side/antenna_manufacturer_air.step
48.0 x 20.9 x 30.0 mm
