fukawachan/PoseDollLab_Design/Hardware/PoseDoll44/generated/revO3/runs/o3_20260924_r3/joint/sensor_pcba_2.step

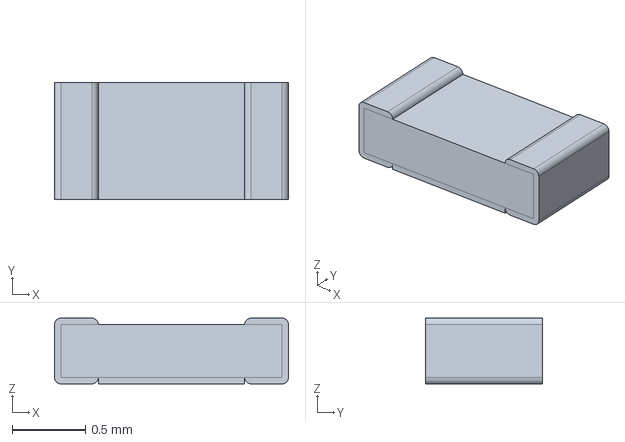
[picture p42: CAD file, 2026-09-23]
Hardware/PoseDoll44/generated/revO3/runs/o3_20260924_r3/joint/sensor_pcba_2.step
1.60 x 0.8 x 0.45 mm
