fukawachan/PoseDollLab_Design/Hardware/PoseDoll44/generated/revO3/runs/o3_20260924_r3/pcba/distal4_side/J50_bend_R4.step

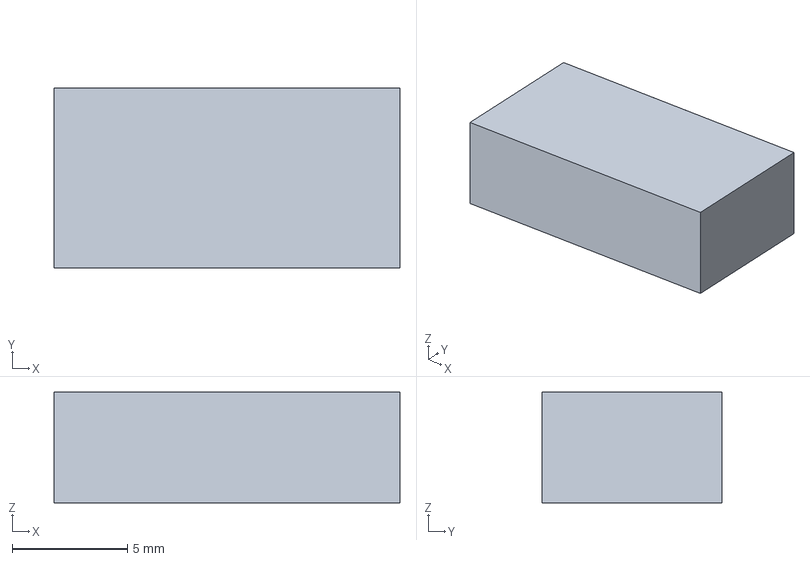
[picture p43: CAD file, 2026-09-23]
Hardware/PoseDoll44/generated/revO3/runs/o3_20260924_r3/pcba/distal4_side/J50_bend_R4.step
15.0 x 7.80 x 4.80 mm
