fukawachan/PoseDollLab_Design/Hardware/PoseDoll44/generated/revO3/runs/o3_20260924_r1/joint/floating_brake_disc.step

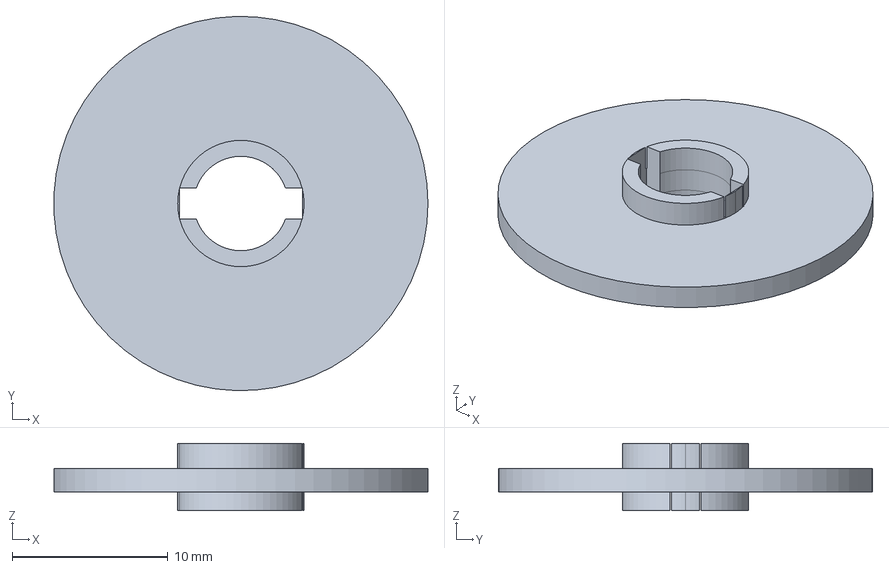
[picture p44: CAD file, 2026-09-23]
Hardware/PoseDoll44/generated/revO3/runs/o3_20260924_r1/joint/floating_brake_disc.step
24.0 x 24.0 x 4.30 mm
