fukawachan/PoseDollLab_Design/Hardware/PoseDoll44/generated/revO3/runs/o3_20260924_r1/pcba/distal4_narrow/J50_bend_R12.step

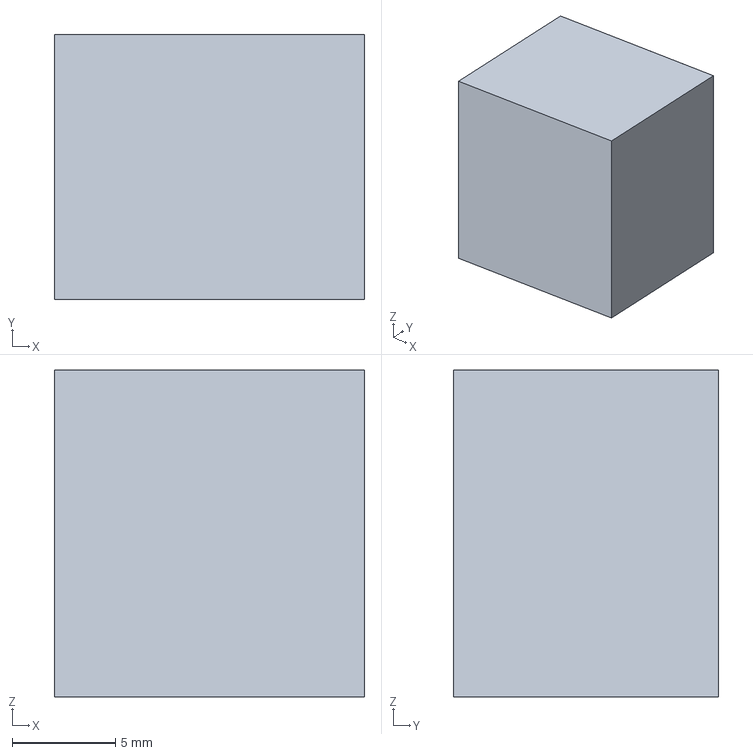
[picture p45: CAD file, 2026-09-23]
Hardware/PoseDoll44/generated/revO3/runs/o3_20260924_r1/pcba/distal4_narrow/J50_bend_R12.step
15.0 x 12.8 x 15.8 mm
