fukawachan/PoseDollLab_Design/Hardware/PoseDoll44/generated/revO3/runs/o3_20260924_r1/joint/keyed_pressure_plate.step

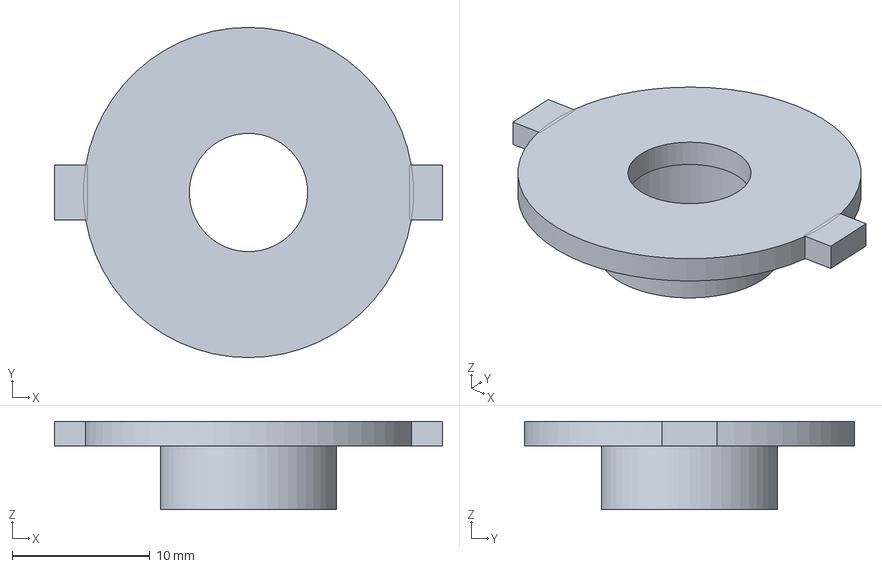
[picture p46: CAD file, 2026-09-23]
Hardware/PoseDoll44/generated/revO3/runs/o3_20260924_r1/joint/keyed_pressure_plate.step
28.2 x 24.0 x 6.40 mm
