fukawachan/PoseDollLab_Design/Hardware/PoseDoll44/docs/WIRING_AND_DIAGNOSTIC.zh-CN.md

# H1 接线与诊断：硬件冻结后执行

本轮没有烧录开发板或连接串口。此表只对应自制传感器板 Rev A 与官方 ESP32-S3-DevKitC-1（8 MB Flash）；不能按数字针脚套用到商城评估板。

## 1. 识别板子

自制板为 32×32 mm、4 个 Ø2.2 mm 安装孔、26 mm 孔距，丝印 PD44 S-A 3V3，J1 为 JST GH 6Pin。[焊盘视图](../generated/drawings/wiring.svg)从**元件面**看。插头正面/背面左右可能相反，不能凭线色判断；预制线束要附 pin1 标记和逐线导通记录。

MCU 要求官方 DevKitC-1，排针已焊、USB 线能传数据。电子板/线束由供应商完成焊接与通断检查，不需要用户焊 TSSOP 或压接 GH 端子。

## 2. 断电接线

| 自制板 J1 | 信号 | DevKitC-1 |
|---:|---|---|
| 1 | GND | GND，J1 排针第 22 脚 |
| 2 | +3V3 | 3V3，J1 第 1 或第 2 脚 |
| 3 | SCK | GPIO12，J1 第 18 脚 |
| 4 | MOSI | GPIO11，J1 第 17 脚 |
| 5 | MISO | GPIO13，J1 第 19 脚 |
| 6 | CS_N | GPIO10，J1 第 16 脚 |

先只接一颗传感器，线长目标 ≤150 mm。自制板已连接芯片 pin11/12，J1-2 不接 5V。H1 仅由开发板 USB 供电，不接外部 5V，也没有 CAN 连接。原生 USB 使用 GPIO19/20，不能占用。

官方 AS5048A 评估板的 P1 编号与此板不同，部分版本排针未焊。需要按实物修订和信号丝印另行制作线束；“5V”节点在 3.3V 模式下的接法要按原理图核对，不能靠名称猜测。

供应商应提供首次限流上电、电压/电流、无短路和接口导通记录。实物外形、接口、版本与工单不一致时停止，由设计端复核。

## 3. 固件上传入口

源码在 Firmware/PoseDollHardware，已用 ESP-IDF 6.1 编译。确认 ESP32-S3、8 MB Flash、实物端口和工单后，才能在该目录执行：

~~~
idf.py -p COM实际端口 flash
~~~

这里没有可直接粘贴的 COM 编号。烧录说明要与到货板的端口一起冻结；**当前不用执行**。程序从原生 USB Serial/JTAG 输出二进制诊断，UART 输出常规日志。烧录后 COM 变化时重新核对原生 USB；不占用模拟器正在使用的串口。程序不写传感器 OTP、不写 MCU 熔丝。

## 4. 点击记录

1. 双击 Tools/PoseDollHardwareBridge/Open_Diagnostic.cmd。
2. 刷新端口并选择已核对的开发板；界面不会自动连接。
3. 固定关节，点击“记录 10 秒”，应显示递增帧数、valid 和原始角度。
4. 打开日志文件夹，每次生成 .bin 原始字节、.jsonl 逐帧数据和 .summary.json。
5. 先看 frames、valid_frames、framing_or_session_errors、sequence_gaps、transport_error。

flags 位值：1 SPI I/O；2 校验；4 芯片错误；8 磁场/启动诊断异常；16 零点寄存器非零，可组合。错误帧角度为无效，不能当作有效零。重启或换板需新建记录，会话混入和旧时间戳会被拒绝。

先测静止 → 空载扫角 → 重复静止 → 独立基准重复到位 → 审查后的负载。359°/0° 是正常周期边界；程序只在统计时展开周期，没有替机械零点校准。

静止 RMS ≤0.15° 只有在机械固定、完整 10 秒且原始数据无异常时才可比较；小噪声不证明绝对准确。绝对误差需要独立角度基准，打印刻度不能证明 ≤1.5°。

## 与 UE 的边界

H1 标记 H1_SINGLE_REAL_AXIS_DIAGNOSTIC，只含索引 17（elbow_l.flex）的一个测试通道。其他 43 轴不存在，也不会向当前模拟器端口发数据。

后续仍需 6 区域 CAN、完整 cohort、设备选择、实体校准与 UE 回归。新增实体 profile 只用于布局，不能替换虚拟 profile 或模拟 calibration。
