fukawachan/PoseDollLab_Design/Hardware/PoseDoll44/docs/WIRING_REVM.zh-CN.md

# Rev M 线束和接线

每款人偶有 **41 根传感器线、5 根 CAN 线、6 根电源支路线**，合计 52 根内部成品线。另需一根数据 USB 线及外部 5 V 适配器的直流线。下料表对应 Manny / Quinn 各自固定点，单位 mm，长度是每一根芯线的候选下料长度，不是把六根芯线长度相加。

- [Manny 下料表](../harness/manny_cut_list_revM.csv) / [带坐标与长度推导的数据](../harness/manny_revM.json)
- [Quinn 下料表](../harness/quinn_cut_list_revM.csv) / [带坐标与长度推导的数据](../harness/quinn_revM.json)

## 接头：按引脚编号接，不按插头朝向猜

| 连接 | 插壳和端子 | 引脚顺序 |
|---|---|---|
| 传感器 ↔ 区域板 | 两端 SHR-06V-S，SSH-003T-P0.2-H | 1 GND，2 3V3，3 SCK，4 MOSI，5 MISO，6 CS_N |
| CAN 节点 ↔ 节点 | 两端 GHR-03V-S，SSHL-002T-P0.2 | 1 GND，2 CAN_L，3 CAN_H |
| 分配板 ↔ 区域板 | 两端 PHR-2，SPH-002T-P0.5S | 1 5V，2 GND |

所有线均为 **1→1、2→2……**，不是“把同一颜色放在看起来同一边”。从插合面和进线面看，引脚位置相反；以 PCB 的 1 脚标记、封装焊盘编号及 JST 图纸为准。成品线逐芯通断、相邻短路测试后再贴标签。

推荐颜色只是辅助：GND 黑、3V3 红、SCK 黄、MOSI 蓝、MISO 绿、CS_N 白；电源 5V 红/GND 黑；CAN_H 白/CAN_L 蓝/GND 黑。用万用表确认的引脚编号优先于颜色。

## 区域板端口

N1：腰 3 路；N2：胸 3 路、头 3 路；N3：左肩带/手臂 9 路；N4：右肩带/手臂 9 路；N5：左腿/脚 7 路；N6：右腿/脚 7 路。

P1…P9 对应 PCB 的 J11…J19。逐轴具体端口以线束表和 `network_revM.json` 为准；未使用的端口留空，不能把它们接到旧 44 轴方案的骨盆通道上。

CAN 采用一条连续总线：

```text
N6 — N1 — N5 — N3 — N2 — N4
```

每段由前一节点 J3 接后一节点 J2。**仅 N6、N4 接通 120 Ω 终端跳线 JP1**，其余节点断开终端；N1 网关位于总线中间是正常的。断电测 CAN_H 与 CAN_L 之间，目标约 60 Ω，先排查错误终端再通电。

电源采用独立六路星形支线：POWER.J2→N1.J1，J3→N2.J1……J7→N6.J1。CAN 接头只有信号和参考地，不负责全身供电。外部电源必须是**稳压 5 V、至少 3 A、中心正极、带短路保护的隔离适配器**；插头为匹配 PJ-002AH 的 5.5 mm 外径 / 2.1 mm 标称内径类型，插入长度按插座图纸核对。USB 只传数据，不为全身供电。

## 导线与固定

- 传感器：Alpha 2841/7，30 AWG 多股 PTFE，标称外径 0.61 mm，匹配 SH 端子。
- CAN：Alpha 5851，30 AWG 多股 PTFE，标称外径 0.81 mm，匹配 GH 端子。H/L 绞合，候选节距 20 mm，地线伴随。
- 电源：Alpha 3049，26 AWG 多股 PVC，标称外径 1.30 mm，匹配 PH 端子。

不要只按 AWG 代购线：绝缘外径也必须进入端子的允许范围。这里没有选更粗的 3050，是因为其标称导体面积超出该 PH 端子表中的上限。导线候选并未获得这套人偶的反复弯曲寿命认证。

稳定肢段有 8 处绑带式线夹，孔径 4.8 mm，使用 0.5 mm 自由厚度硅胶垫（安装约 0.4 mm）和 2.5 mm 扎带。夹在骨架梁上，不夹转轴。外壳先卸下再安装这些夹。线束可以分股通过，不要把整段导线灌胶或套成僵硬粗管。

每块传感器附近，将导线经硅胶保护后松绑到该传感器**固定侧**的隔柱/板托，保留约 35 mm 接头服务段。不能收紧扎带压裸 PCB、元器件或接头锁扣。表中给出了固定部件的准确名称。

关节之间用朝外的松弛 U 形线段，候选最小弯曲半径 12 mm；电源活动段用 15 mm。肘膝尽量走外侧，不跨在屈曲后被夹住的内侧缝隙。区域仓内的六股传感器线先平铺为 R6.5 的固定 S 弯，再汇到带硅胶边条的下出口；这段不承担反复运动。

## 计算能证明什么

下料长度不是只量中立姿势下的直线距离。程序按两端所属的刚体和中间所有转轴，计算旋转半径保持不变时的距离上界，再加入服务弯和装配余量；另用规定姿态及 1,000 个随机组合独立检查该上界。

这能检查“所留线长是否覆盖两端的距离变化”，**不能证明柔性线在所有动作中会自动沿无障碍路径弯曲**。最终布线时仍要逐轴做全行程检查；不得把查看器中的固定点当作已经仿真过的柔性电缆。

最长传感器线还需要做示波器/误码与断线测试。SPI 250 kHz 并不自动保证任何长度都能可靠工作；AS5048A 输出负载、边沿振铃、接地与真实线缆电容均是实物验收项目。
