fukawachan/PoseDollLab_Design/Hardware/PoseDoll44/verification/revO3/runs/o3_20260924_r1/assembly.txt

01 shaft datum PASS_SAMPLED_NOMINAL_ONLY 0
03 radial rear_bush L PASS_SAMPLED_NOMINAL_ONLY 0
03 radial rear_bush R PASS_SAMPLED_NOMINAL_ONLY 0
03 radial front_bush L PASS_SAMPLED_NOMINAL_ONLY 0
03 radial front_bush R PASS_SAMPLED_NOMINAL_ONLY 0
03 radial thrust_rear L PASS_SAMPLED_NOMINAL_ONLY 0
03 radial thrust_rear R PASS_SAMPLED_NOMINAL_ONLY 0
03 radial thrust_front L PASS_SAMPLED_NOMINAL_ONLY 0
03 radial thrust_front R PASS_SAMPLED_NOMINAL_ONLY 0
04 split housing L PASS_SAMPLED_NOMINAL_ONLY 0
04 split housing R PASS_SAMPLED_NOMINAL_ONLY 0
04b rear cup registered to cartridge PASS_SAMPLED_NOMINAL_ONLY 0
04c axial cup screw 0 PASS_SAMPLED_NOMINAL_ONLY 0
04c axial cup screw 1 PASS_SAMPLED_NOMINAL_ONLY 0
04c axial cup screw 2 PASS_SAMPLED_NOMINAL_ONLY 0
04c axial cup screw 3 PASS_SAMPLED_NOMINAL_ONLY 0
05 case fastening bearing_clamp_-6 PASS_SAMPLED_NOMINAL_ONLY 0
05 case fastening bearing_clamp_6 PASS_SAMPLED_NOMINAL_ONLY 0
06 rear loading front_lining_backing PASS_SAMPLED_NOMINAL_ONLY 0
06 rear loading front_friction_lining PASS_SAMPLED_NOMINAL_ONLY 0
06 rear loading floating_brake_disc PASS_SAMPLED_NOMINAL_ONLY 0
06 rear loading rear_friction_lining PASS_SAMPLED_NOMINAL_ONLY 0
06 rear loading rear_lining_backing PASS_SAMPLED_NOMINAL_ONLY 0
06 rear loading keyed_pressure_plate PASS_SAMPLED_NOMINAL_ONLY 0
06 rear loading spring_front_washer PASS_SAMPLED_NOMINAL_ONLY 0
07 free spring 4 PASS_SAMPLED_NOMINAL_ONLY 0
07 free spring 3 PASS_SAMPLED_NOMINAL_ONLY 0
07 free spring 2 PASS_SAMPLED_NOMINAL_ONLY 0
07 free spring 1 PASS_SAMPLED_NOMINAL_ONLY 0
08 rear free washer PASS_SAMPLED_NOMINAL_ONLY 0
sample 09 helical cap insertion -10.05
sample 09 helical cap insertion -9.8
sample 09 helical cap insertion -9.55
sample 09 helical cap insertion -9.3
sample 09 helical cap insertion -9.05
sample 09 helical cap insertion -8.8
sample 09 helical cap insertion -8.55
sample 09 helical cap insertion -8.3
sample 09 helical cap insertion -8.05
sample 09 helical cap insertion -7.8
sample 09 helical cap insertion -7.55
sample 09 helical cap insertion -7.3
sample 09 helical cap insertion -7.05
sample 09 helical cap insertion -6.8
sample 09 helical cap insertion -6.55
sample 09 helical cap insertion -6.3
sample 09 helical cap insertion -6.05
sample 09 helical cap insertion -5.8
sample 09 helical cap insertion -5.55
sample 09 helical cap insertion -5.3
sample 09 helical cap insertion -5.05
sample 09 helical cap insertion -4.8
sample 09 helical cap insertion -4.55
sample 09 helical cap insertion -4.3
sample 09 helical cap insertion -4.05
