fukawachan/PoseDollLab_Design/Hardware/PoseDoll44/verification/revO2/runs/o2_20260923_r1/assembly.txt

01 shaft datum PASS_SAMPLED_NOMINAL_ONLY 0
03 radial rear_bush L PASS_SAMPLED_NOMINAL_ONLY 0
03 radial rear_bush R PASS_SAMPLED_NOMINAL_ONLY 0
03 radial front_bush L PASS_SAMPLED_NOMINAL_ONLY 0
03 radial front_bush R PASS_SAMPLED_NOMINAL_ONLY 0
03 radial thrust_rear L PASS_SAMPLED_NOMINAL_ONLY 0
03 radial thrust_rear R PASS_SAMPLED_NOMINAL_ONLY 0
03 radial thrust_front L PASS_SAMPLED_NOMINAL_ONLY 0
03 radial thrust_front R PASS_SAMPLED_NOMINAL_ONLY 0
04 split housing L PASS_SAMPLED_NOMINAL_ONLY 0
04 split housing R PASS_SAMPLED_NOMINAL_ONLY 0
04b rear cup registered to cartridge PASS_SAMPLED_NOMINAL_ONLY 0
04c axial cup screw 0 PASS_SAMPLED_NOMINAL_ONLY 0
04c axial cup screw 1 PASS_SAMPLED_NOMINAL_ONLY 0
04c axial cup screw 2 PASS_SAMPLED_NOMINAL_ONLY 0
04c axial cup screw 3 PASS_SAMPLED_NOMINAL_ONLY 0
05 case fastening bearing_clamp_-6 PASS_SAMPLED_NOMINAL_ONLY 0
05 case fastening bearing_clamp_6 PASS_SAMPLED_NOMINAL_ONLY 0
06 rear loading front_friction_lining PASS_SAMPLED_NOMINAL_ONLY 0
06 rear loading floating_brake_disc PASS_SAMPLED_NOMINAL_ONLY 0
06 rear loading rear_friction_lining PASS_SAMPLED_NOMINAL_ONLY 0
06 rear loading wear_sheet PASS_SAMPLED_NOMINAL_ONLY 0
06 rear loading keyed_pressure_plate PASS_SAMPLED_NOMINAL_ONLY 0
06 rear loading spring_front_washer PASS_SAMPLED_NOMINAL_ONLY 0
07 free spring 4 PASS_SAMPLED_NOMINAL_ONLY 0
07 free spring 3 PASS_SAMPLED_NOMINAL_ONLY 0
07 free spring 2 PASS_SAMPLED_NOMINAL_ONLY 0
07 free spring 1 PASS_SAMPLED_NOMINAL_ONLY 0
08 rear free washer PASS_SAMPLED_NOMINAL_ONLY 0
09 helical cap insertion PASS_SAMPLED_NOMINAL_ONLY 0
10 coordinated spring compression PASS_SAMPLED_NOMINAL_ONLY 0
11 positive cap lock PASS_SAMPLED_NOMINAL_ONLY 0
12 sensor support diametric_magnet PASS_SAMPLED_NOMINAL_ONLY 0
12 sensor support magnet_keeper PASS_SAMPLED_NOMINAL_ONLY 0
12 sensor support keeper_screw_-4.25 PASS_SAMPLED_NOMINAL_ONLY 0
12 sensor support keeper_screw_4.25 PASS_SAMPLED_NOMINAL_ONLY 0
12 sensor support sensor_post_-7.7 PASS_SAMPLED_NOMINAL_ONLY 0
12 sensor support sensor_post_7.7 PASS_SAMPLED_NOMINAL_ONLY 0
13 unscaled sensor PCBA PASS_SAMPLED_NOMINAL_ONLY 0
14 PCBA retention pcb_edge_clamp_-7.7 PASS_SAMPLED_NOMINAL_ONLY 0
14 PCBA retention pcb_edge_clamp_7.7 PASS_SAMPLED_NOMINAL_ONLY 0
14 PCBA retention pcb_clamp_screw_-7.7 PASS_SAMPLED_NOMINAL_ONLY 0
14 PCBA retention pcb_clamp_screw_7.7 PASS_SAMPLED_NOMINAL_ONLY 0
15 hollow tool insertion PASS_SAMPLED_NOMINAL_ONLY 0
16 single-axis rotation PASS_SAMPLED_NOMINAL_ONLY 0
