fukawachan/PoseDollLab_Design/Hardware/PoseDoll44/verification/PROPORTION_AUDIT.zh-CN.md

# Manny 体格比例核对

**结论：当前 Rev C 布局不满足等比例要求，不能据此固定全身尺寸。**

目标为项目已验证的 `SKM_Manny_Simple` / `CR_Mannequin_Body`。尺寸取自此前 UE 导出的真实网格参考骨架；已有测试的 Rig 指纹与目标配置一致。本次没有改动 UE 资产或模拟器，也没有重新读取当前编辑器资产。

下表以左腿“髋—膝—踝”总长 235 mm 为统一比较基准，将 Manny 等比缩小。它用于暴露偏差，不是已经选定的最终身高。

| 测量段（关节中心之间） | 当前 Rev C | 按 Manny 比例应为 | 偏差 |
|---|---:|---:|---:|
| 上臂：肩外展轴—肘 | 130.0 mm | 76.3 mm | +70.4% |
| 前臂：肘—腕 | 130.0 mm | 74.8 mm | +73.7% |
| 大腿：髋—膝 | 130.0 mm | 119.0 mm | +9.2% |
| 小腿：膝—踝 | 105.0 mm | 116.0 mm | -9.4% |

两节手臂 / 两节腿长：Manny 为 **0.643**，Rev C 为 **1.106**。这项比例已经明显不同，与整机最终缩放为多高无关。

当前肩屈伸轴与外展轴还相距 56 mm，因此不存在一个与 Manny 对应的共同肩关节中心。这会造成随姿势变化的位置差，不能仅缩短两根连杆就宣称解决。

现有 UE 适配层主要采用源肢体朝向，并保留目标 Manny 自己的骨长；角度映射通过不等于身体比例或手脚接触通过。尤其双手合拢、抱臂、扶额、叉腰、跪坐需要单独的空间误差检查。

## 修订后的设计约束

1. 以同一份 Manny 参考数据生成机械关节目标坐标和比例报告，所有主要尺寸使用同一个缩放系数。
2. 同时约束上臂、前臂、大腿、小腿、肩宽、髋宽、骨盆至肩的高度，以及头、手、脚的外形参考。
3. 关节中心及转动轨迹优先；电子板、摩擦模块和外壳围绕这些位置布置。需要空间时优先增大全身统一比例或改机构，不能单独拉长胳膊、扩大肩宽。
4. 机械多轴中心偏移和简化躯干轴的影响必须进入 FK 比较；在统一根坐标、等比例和相同输入下，核对腕、踝、头及接触点。
5. 全身外形高度以脚底到头顶定义，支架、外伸传感器和旧 head_tip 的绝对 Z 坐标不作为身高。
6. 现有单关节模块保留为结构研究件，全身安装位置与尺寸等待这项比例检查通过。无需用户先行打印或测量。

数字目标见 [比例约束](../mechanical_manifest/proportion_constraints_revD.json)。它们是新设定的设计验收目标，尚未达到，不是制造误差或人体标准。

[机器可读结果](proportion_audit_revC_vs_manny.json) · [检查脚本](../tools/audit_proportions.py)
