fukawachan/PoseDollLab_Design/Hardware/PoseDoll44/verification/browser_revM/manny_desktop.png

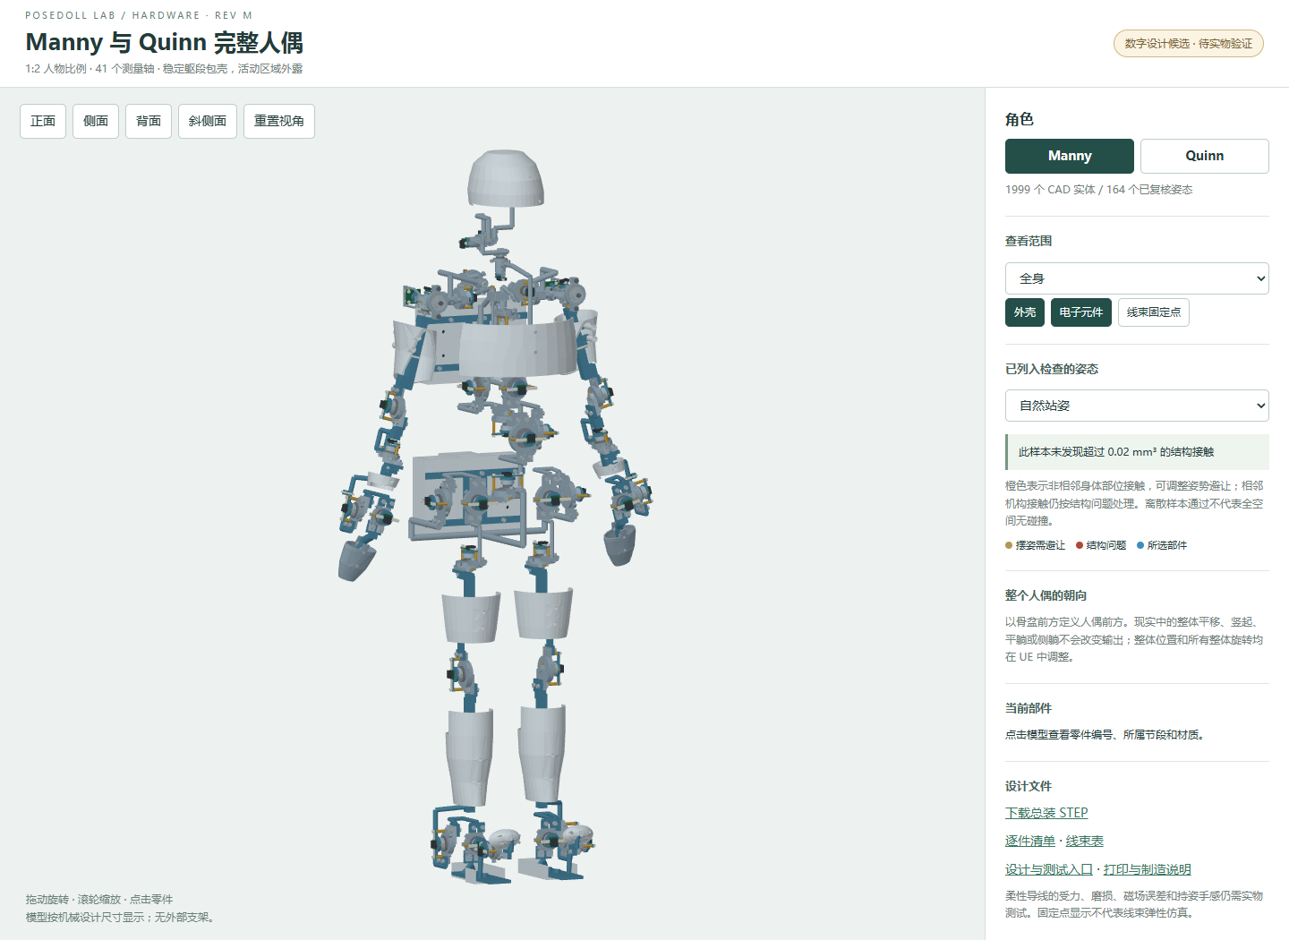
Hardware/PoseDoll44/verification/browser_revM/manny_desktop.png
