fukawachan/PoseDollLab_Design/Hardware/PoseDoll44/verification/browser_revM/mobile.png

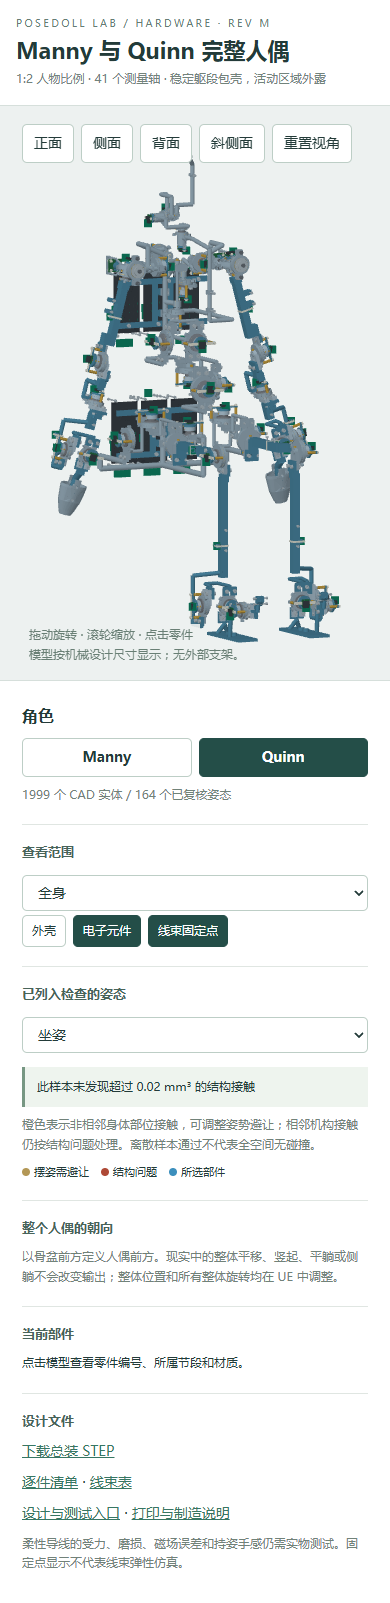
Hardware/PoseDoll44/verification/browser_revM/mobile.png
