fukawachan/PoseDollLab_Design/Hardware/PoseDoll44/verification/browser_revM/quinn_sitting.png

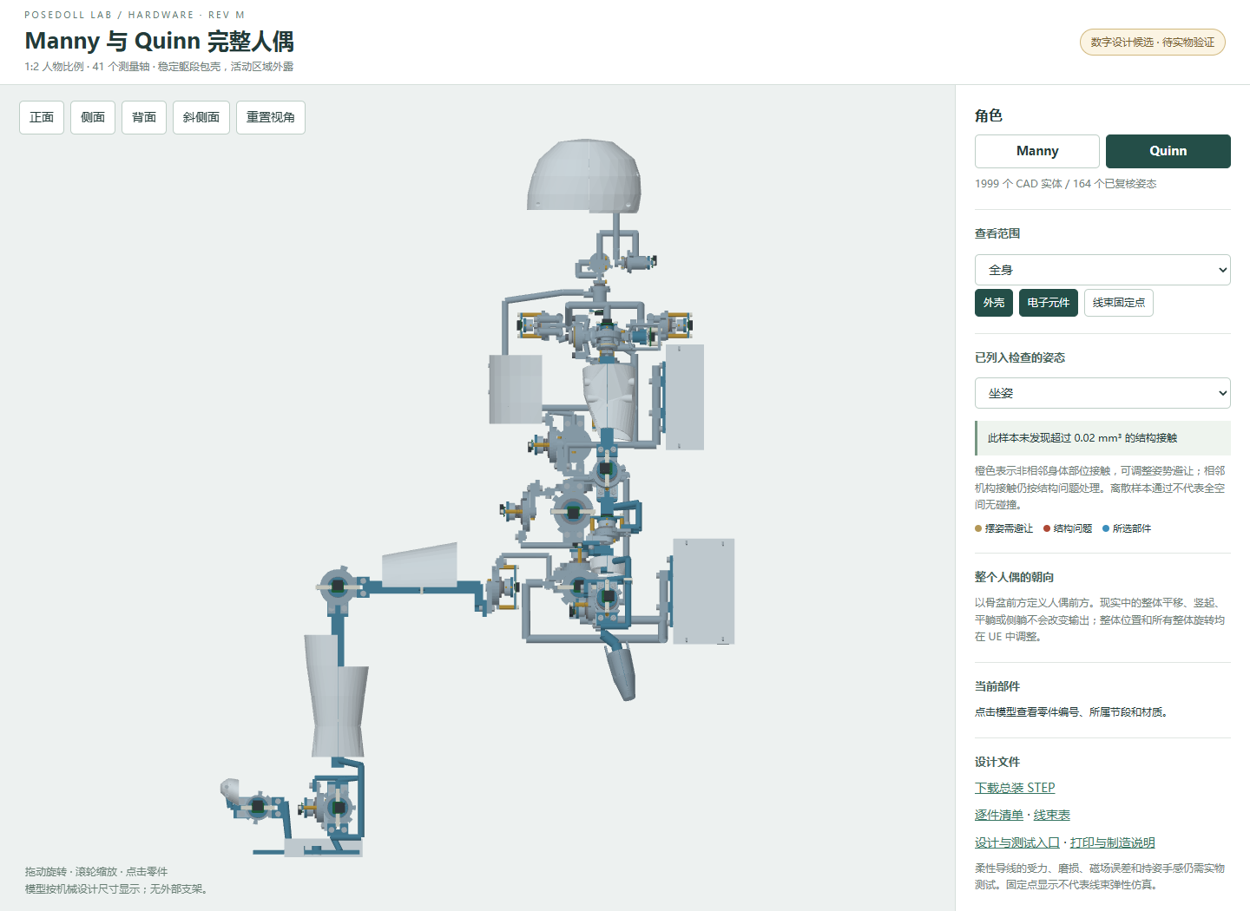
Hardware/PoseDoll44/verification/browser_revM/quinn_sitting.png
