fukawachan/PoseDollLab_Design/Hardware/PoseDoll44/verification/browser_revN/manny_front.png

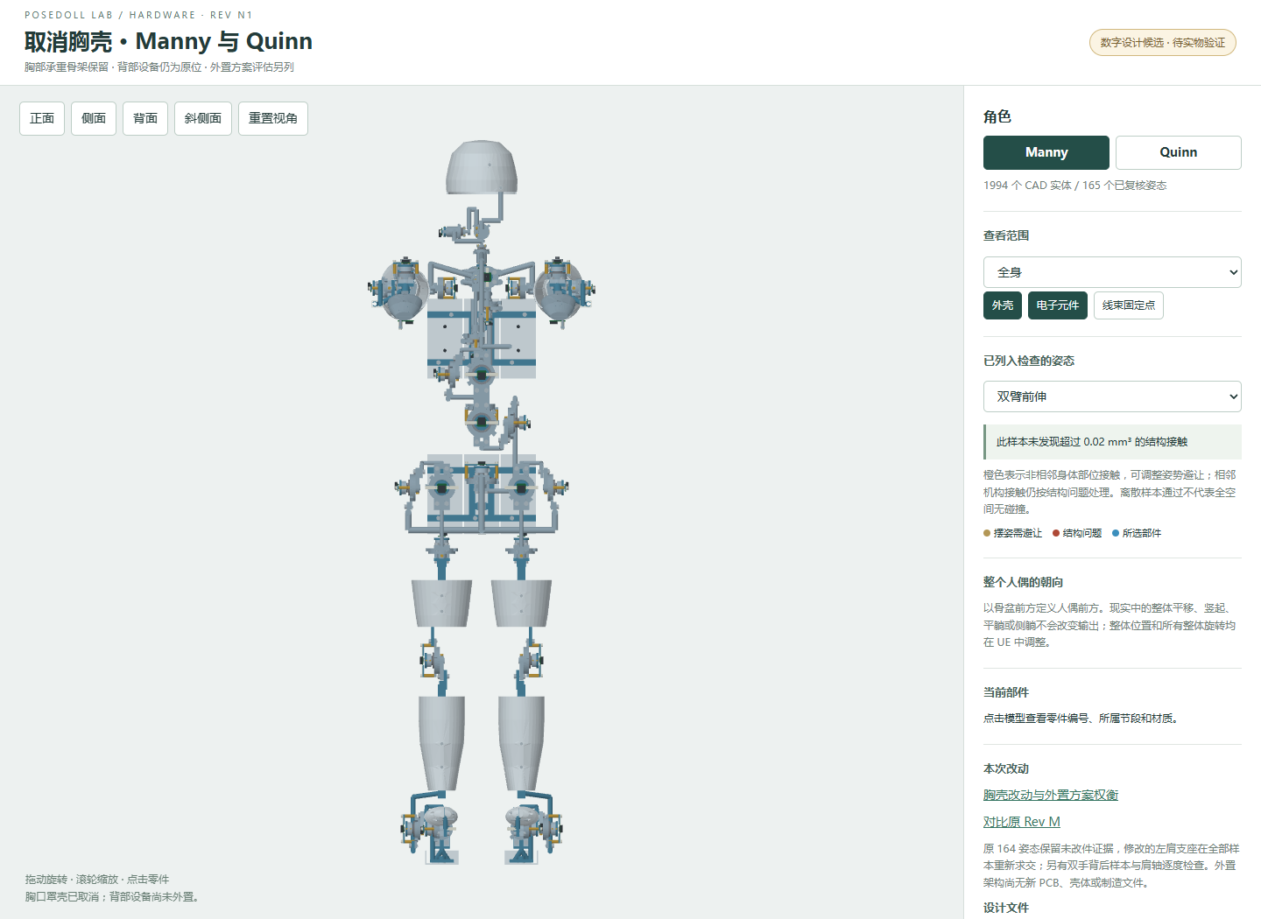
Hardware/PoseDoll44/verification/browser_revN/manny_front.png
