fukawachan/PoseDollLab_Design/Hardware/PoseDoll44/verification/browser_revN/mobile.png

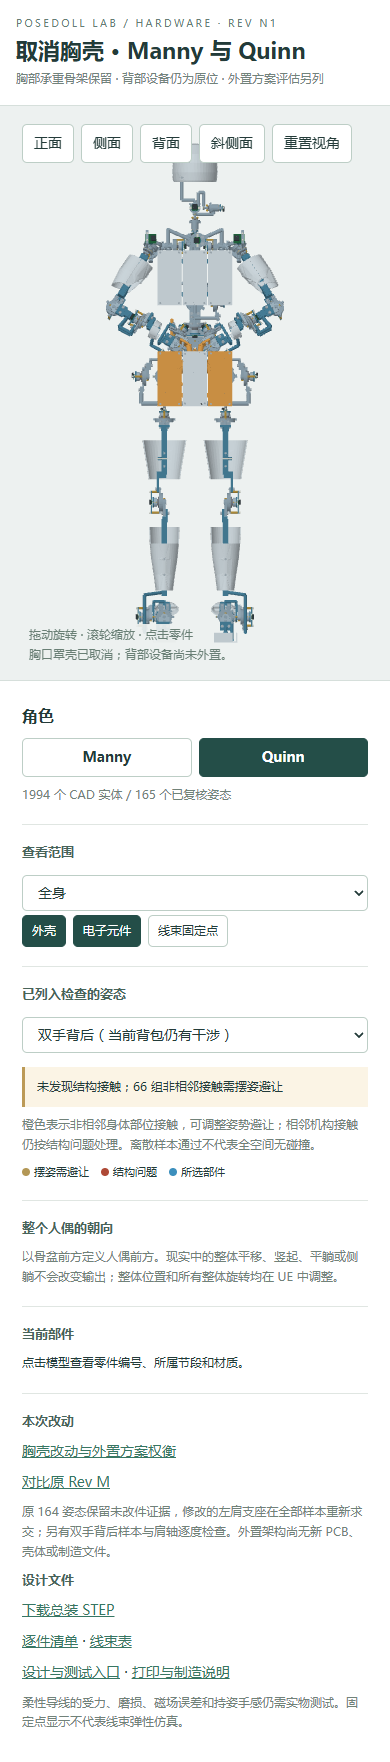
Hardware/PoseDoll44/verification/browser_revN/mobile.png
