fukawachan/PoseDollLab_Design/Hardware/PoseDoll44/verification/browser_revN/quinn_behind.png

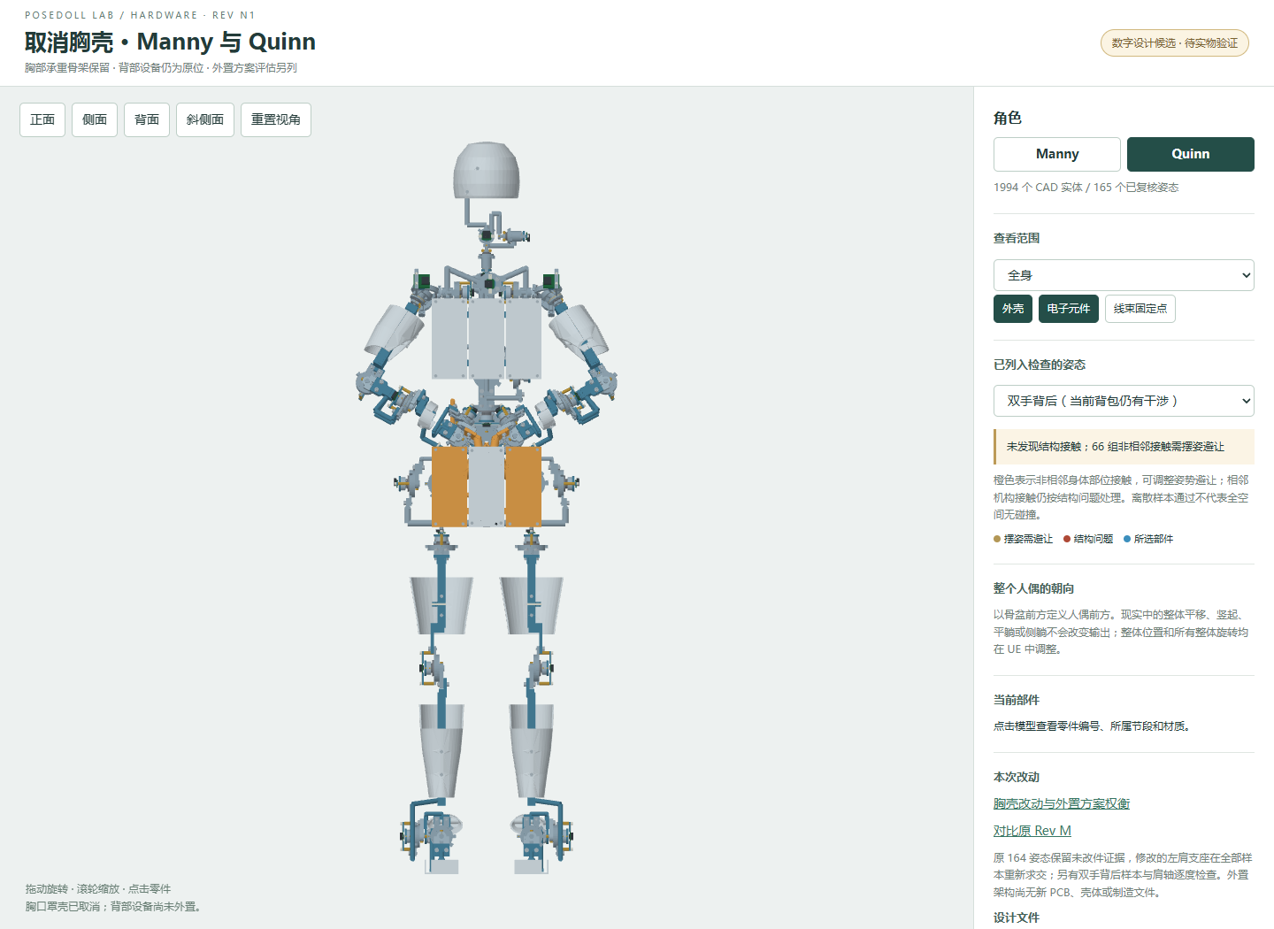
Hardware/PoseDoll44/verification/browser_revN/quinn_behind.png
