fukawachan/PoseDollLab_Design/Hardware/PoseDoll44/verification/revE_viewer.png

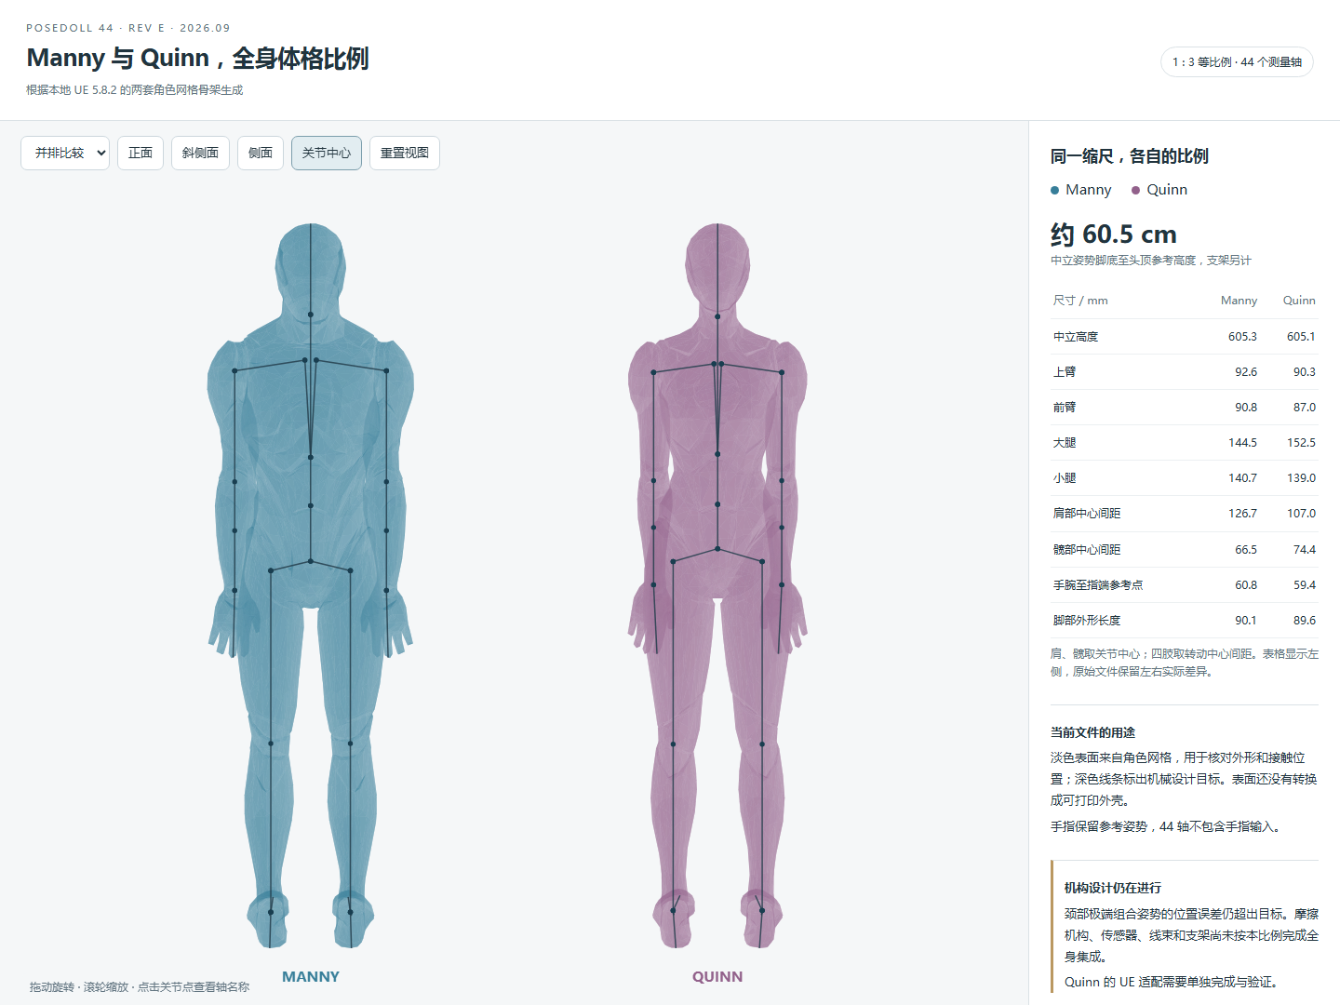
Hardware/PoseDoll44/verification/revE_viewer.png
