fukawachan/PoseDollLab_Design/Hardware/PoseDoll44/electronics/sensor_revB/PoseDoll_AS5048A_revB.kicad_pcb

## KiCad design Hardware/PoseDoll44/electronics/sensor_revB/PoseDoll_AS5048A_revB.kicad_pcb (2026-09-23)

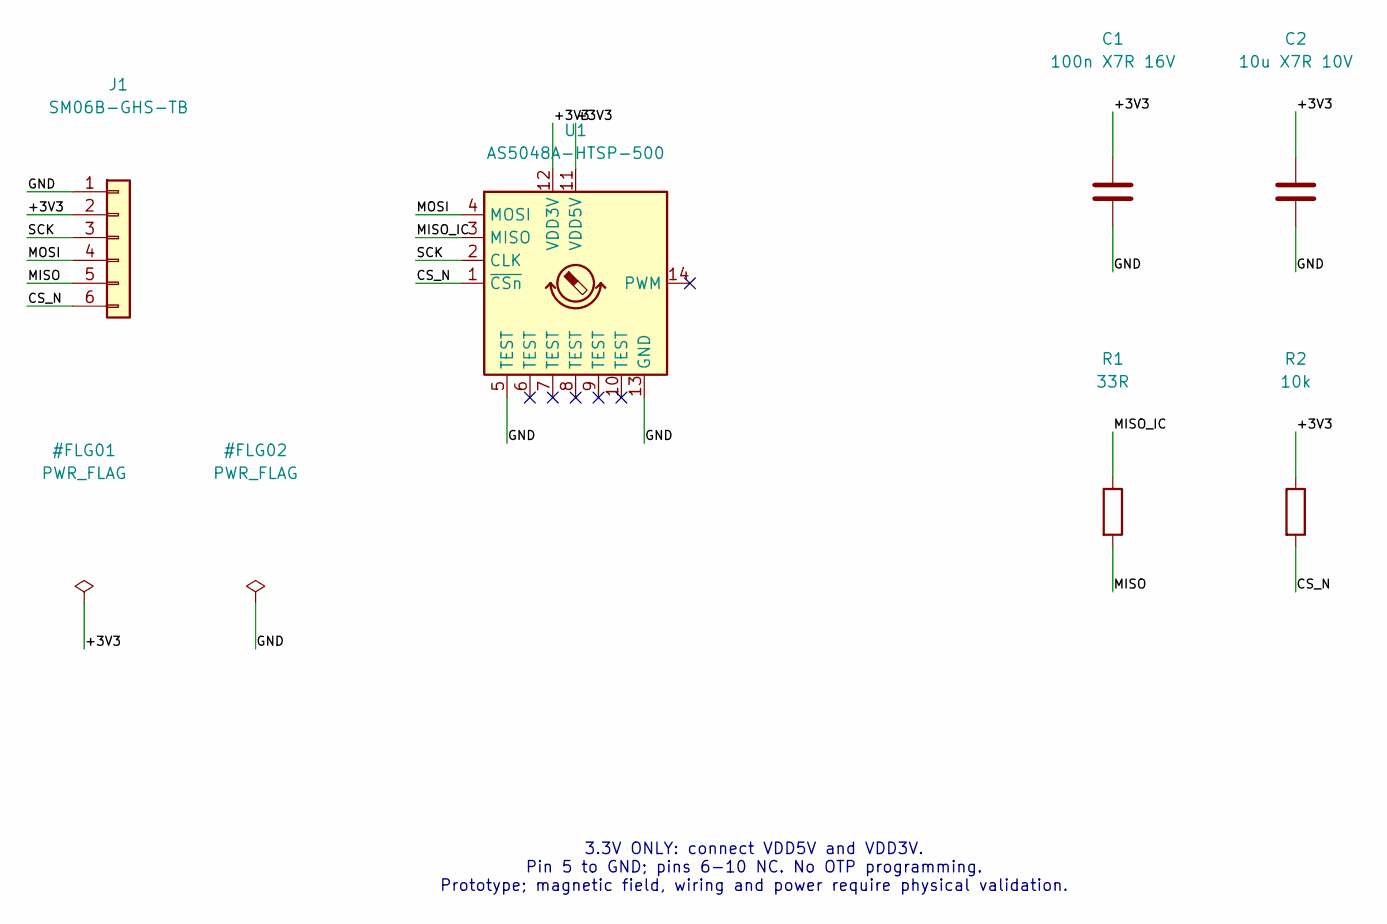
[picture p75: schematic PoseDoll_AS5048A_revB.kicad_sch]

Parts:
C1: 100n X7R 16V; C_0603_1608Metric
C2: 10u X7R 10V; C_0805_2012Metric
J1: SM06B-GHS-TB; JST_GH_SM06B-GHS-TB_1x06-1MP_P1.25mm_Horizontal
R1: 33R; R_0603_1608Metric
R2: 10k; R_0603_1608Metric
U1: AS5048A-HTSP-500; TSSOP-14_4.4x5mm_P0.65mm

Connections:
/+3V3: C1.1, C2.1, J1.2, R2.1, U1.11 (VDD5V), U1.12 (VDD3V)
/CS_N: J1.6, R2.2, U1.1 (~CSn)
/GND: C1.2, C2.2, J1.1, U1.5 (TEST), U1.13 (GND)
/MISO: J1.5, R1.2
/MISO_IC: R1.1, U1.3 (MISO)
/MOSI: J1.4, U1.4 (MOSI)
/SCK: J1.3, U1.2 (CLK)

Notes on the sheet:
3.3V ONLY: connect VDD5V and VDD3V. Pin 5 to GND; pins 6-10 NC. No OTP programming. Prototype; magnetic field, wiring and power require physical validation.

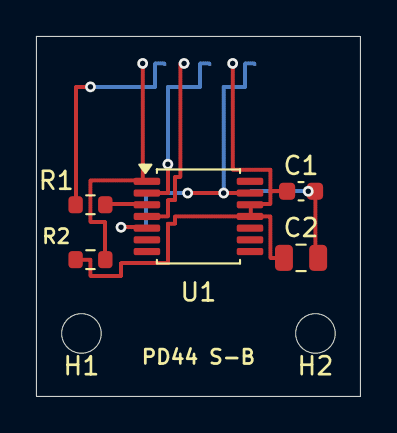
[picture p76: board PoseDoll_AS5048A_revB.kicad_pcb from above]

Board: 2 copper layers, 18.0 x 20.0 mm, 8 parts (1 on the bottom side), 7 nets.

Other parts of the board:
H1, H2: MountingHole_2.2mm_M2
