fukawachan/PoseDollLab_Design/Hardware/PoseDoll44/electronics/power_revM/PoseDoll_PD41_Power_revM.kicad_pcb

## KiCad design Hardware/PoseDoll44/electronics/power_revM/PoseDoll_PD41_Power_revM.kicad_pcb (2026-09-23)

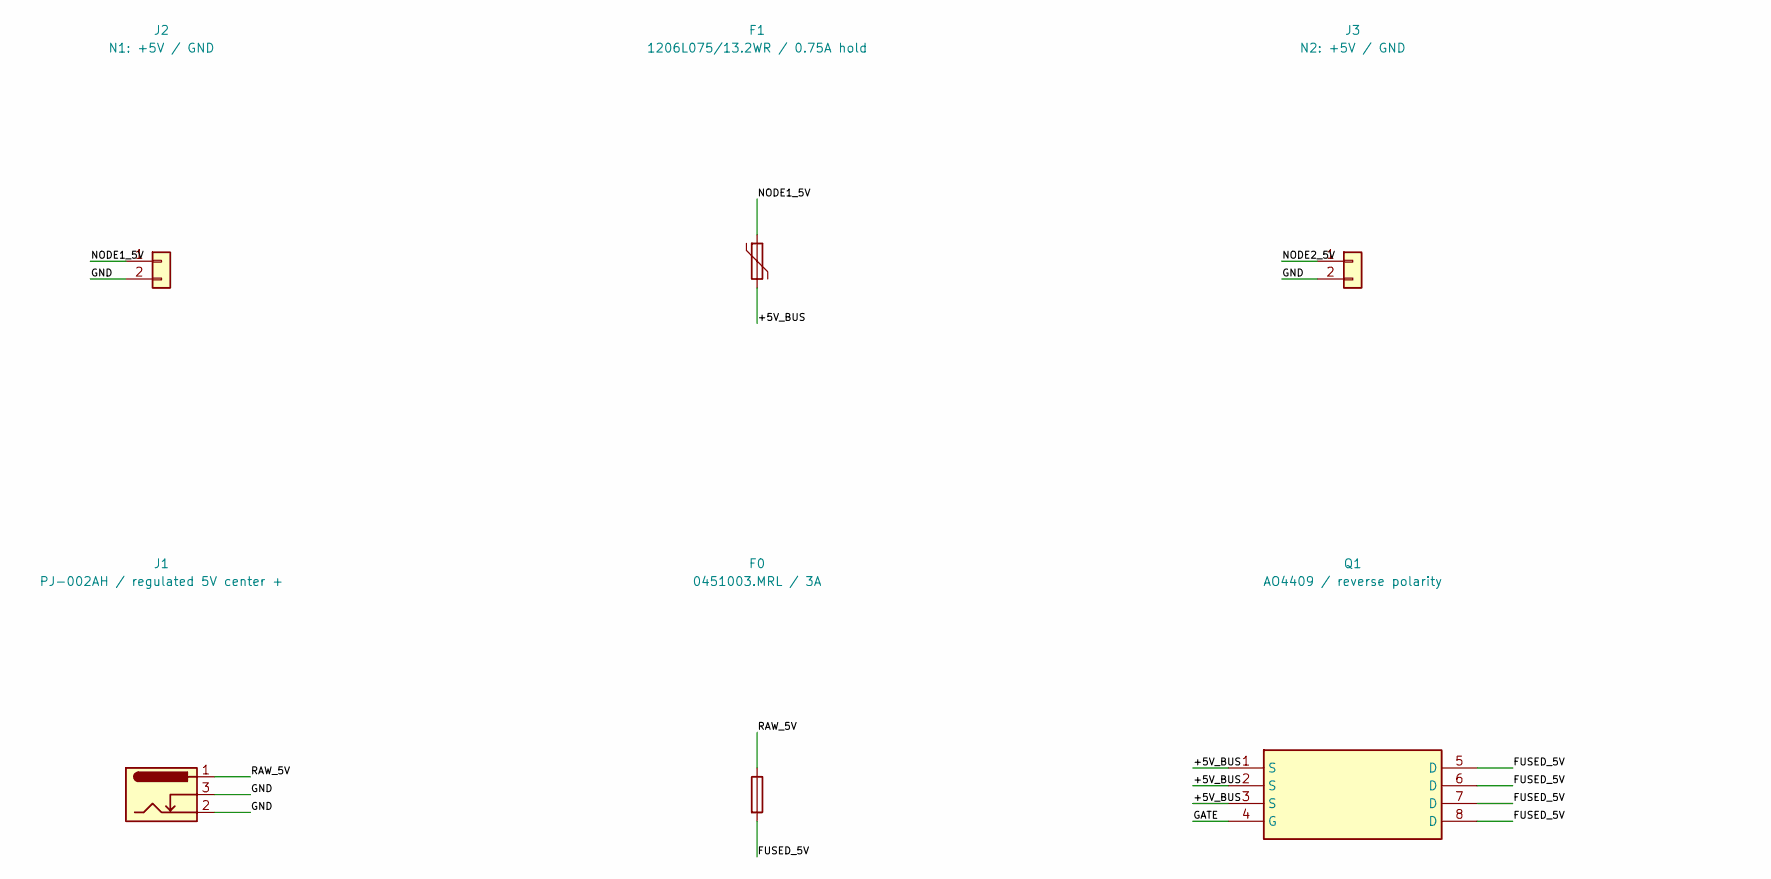
[picture p77: schematic PoseDoll_PD41_Power_revM.kicad_sch, part in row 1, column 1]

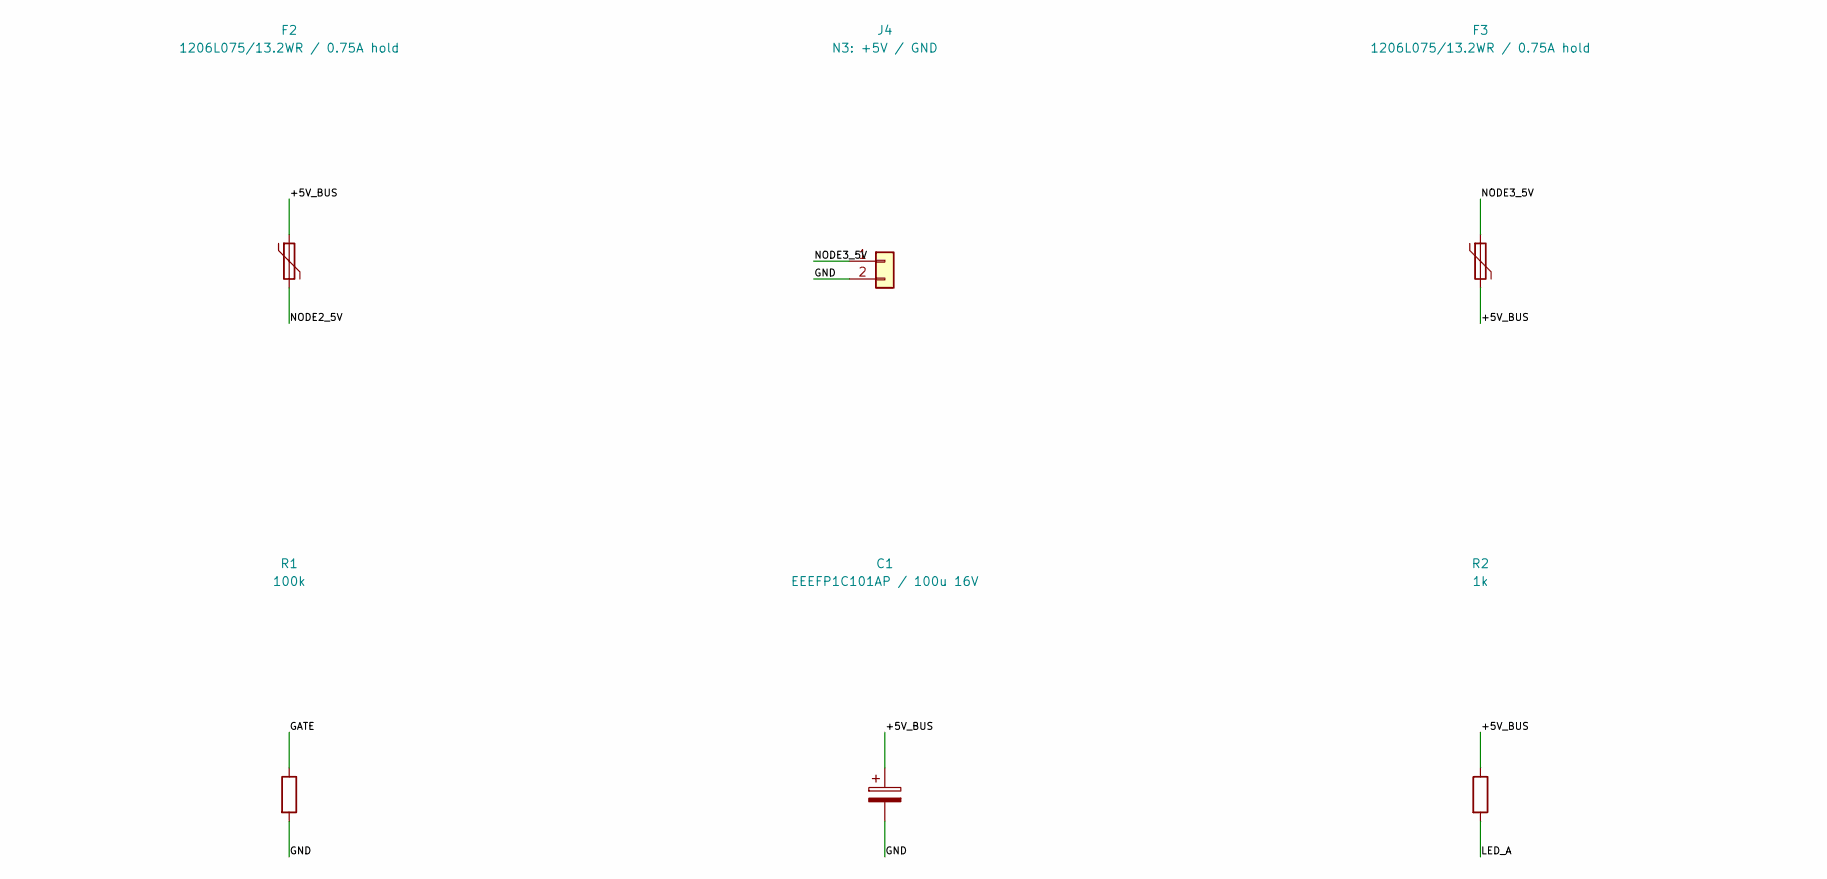
[picture p78: schematic PoseDoll_PD41_Power_revM.kicad_sch, part in row 1, column 2]

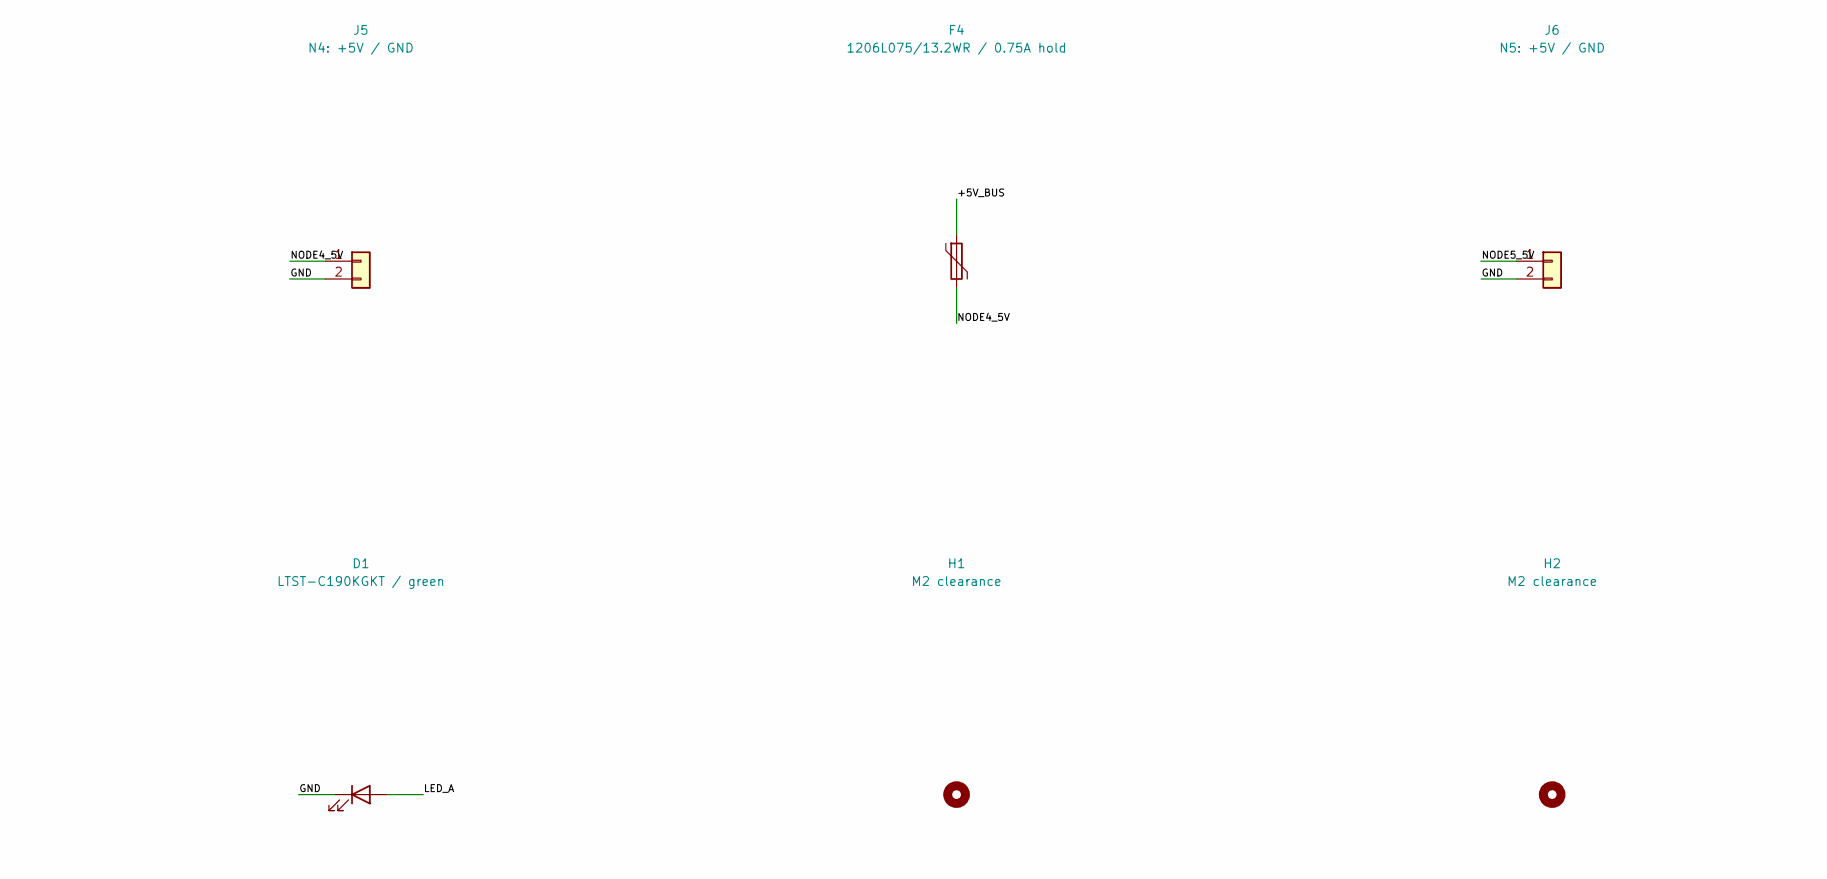
[picture p79: schematic PoseDoll_PD41_Power_revM.kicad_sch, part in row 1, column 3]

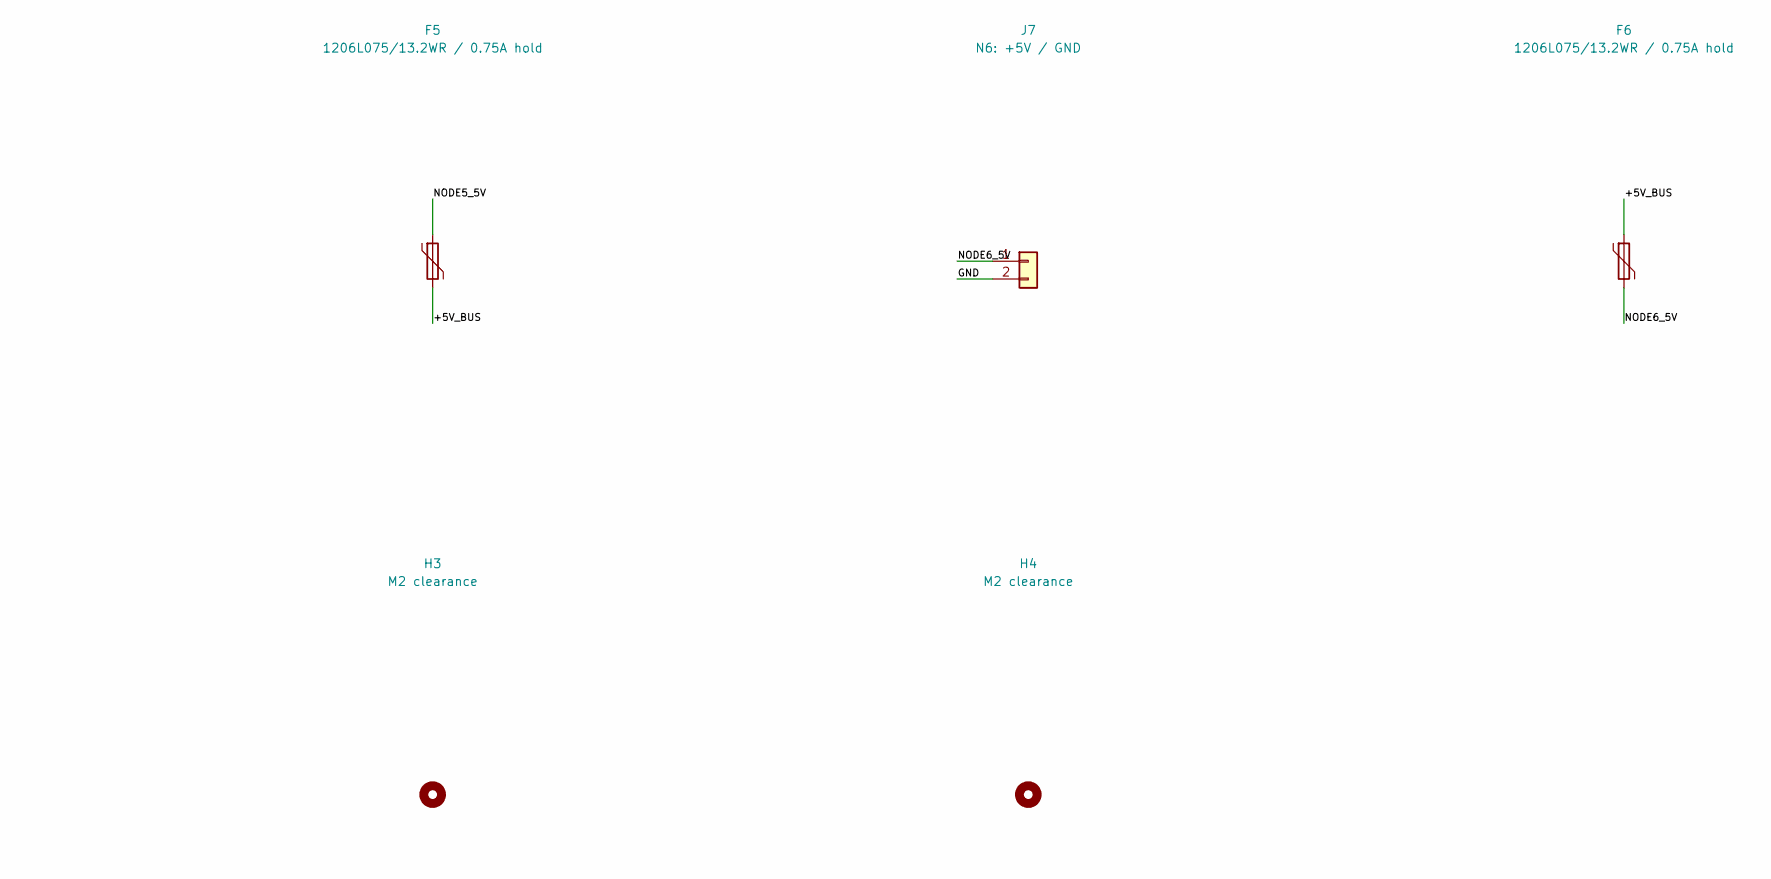
[picture p80: schematic PoseDoll_PD41_Power_revM.kicad_sch, part in row 1, column 4]

Parts:
C1: EEEFP1C101AP / 100u 16V; CP_Elec_6.3x5.8
D1: LTST-C190KGKT / green; LED_0603_1608Metric
F0: 0451003.MRL / 3A; Fuse_Littelfuse-NANO2-451_453
F1, F2, F3, F4, F5, F6: 1206L075/13.2WR / 0.75A hold; Fuse_1206_3216Metric
H1, H2, H3, H4: M2 clearance; MountingHole_2.2mm_M2
J1: PJ-002AH / regulated 5V center +; PJ_002AH_verified
J2: N1: +5V / GND; JST_PH_B2B-PH-K_1x02_P2.00mm_Vertical
J3: N2: +5V / GND; JST_PH_B2B-PH-K_1x02_P2.00mm_Vertical
J4: N3: +5V / GND; JST_PH_B2B-PH-K_1x02_P2.00mm_Vertical
J5: N4: +5V / GND; JST_PH_B2B-PH-K_1x02_P2.00mm_Vertical
J6: N5: +5V / GND; JST_PH_B2B-PH-K_1x02_P2.00mm_Vertical
J7: N6: +5V / GND; JST_PH_B2B-PH-K_1x02_P2.00mm_Vertical
Q1: AO4409 / reverse polarity; SOIC-8_3.9x4.9mm_P1.27mm
R1: 100k; R_0603_1608Metric
R2: 1k; R_0603_1608Metric

Connections:
/+5V_BUS: C1.1, F1.2, F2.1, F3.2, F4.1, F5.2, F6.1, Q1.1 (S), Q1.2 (S), Q1.3 (S), R2.1
/FUSED_5V: F0.2, Q1.5 (D), Q1.6 (D), Q1.7 (D), Q1.8 (D)
/GATE: Q1.4 (G), R1.1
/GND: C1.2, D1.1 (K), J1.2, J1.3, J2.2, J3.2, J4.2, J5.2, J6.2, J7.2, R1.2
/LED_A: D1.2 (A), R2.2
/NODE1_5V: F1.1, J2.1
/NODE2_5V: F2.2, J3.1
/NODE3_5V: F3.1, J4.1
/NODE4_5V: F4.2, J5.1
/NODE5_5V: F5.1, J6.1
/NODE6_5V: F6.2, J7.1
/RAW_5V: F0.1, J1.1

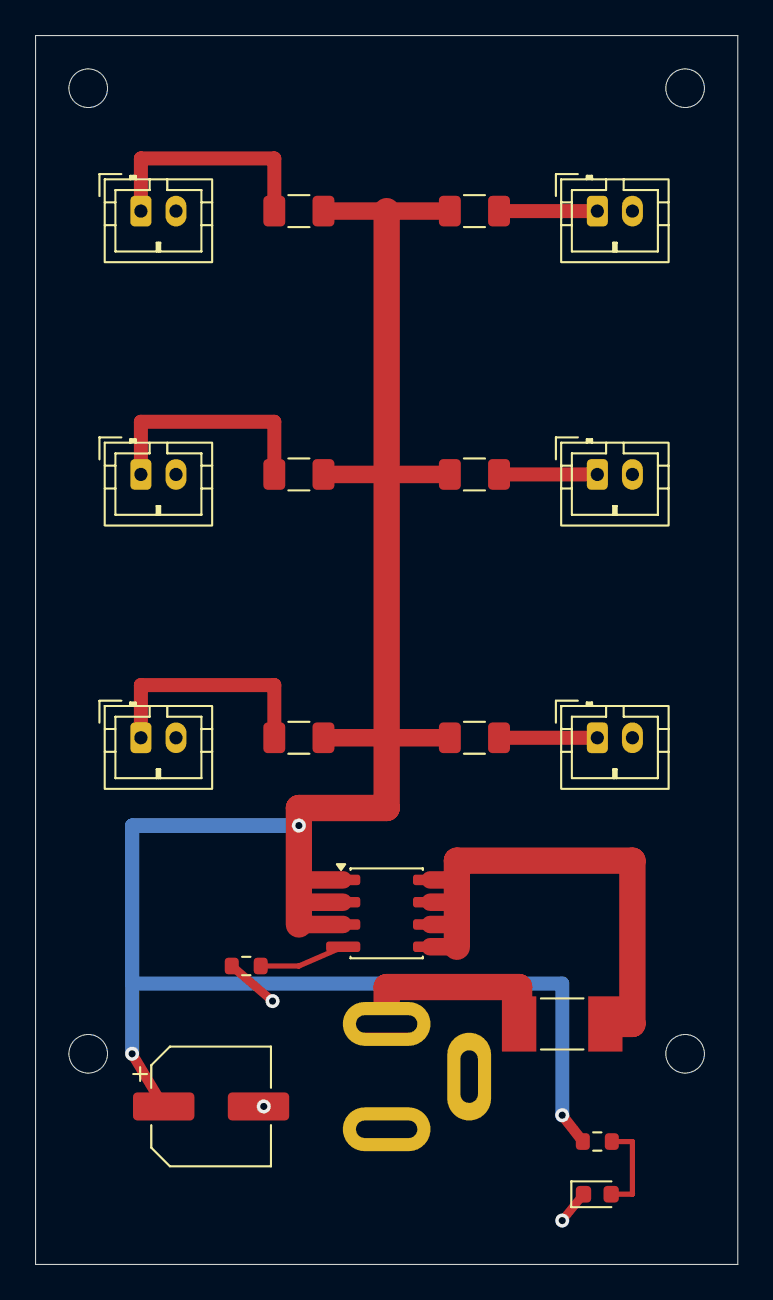
[picture p81: board PoseDoll_PD41_Power_revM.kicad_pcb from above]

Board: 2 copper layers, 40.0 x 70.0 mm, 23 parts (0 on the bottom side), 12 nets.
